pocper/SoC-GPS-Hybrid-Acquisition/firmware/hps_core/DE10_serial_parallel/INC/ARMCA9.h

/**************************************************************************//**
 * @file     ARMCA9.h
 * @brief    CMSIS-Core(A) Device Header File for Device ARMCA9
 *
 * @version  V1.1.0
 * @date     18. July 2023
 ******************************************************************************/
/*
 * Copyright (c) 2009-2023 Arm Limited. All rights reserved.
 *
 * SPDX-License-Identifier: Apache-2.0
 *
 * Licensed under the Apache License, Version 2.0 (the License); you may
 * not use this file except in compliance with the License.
 * You may obtain a copy of the License at
 *
 * www.apache.org/licenses/LICENSE-2.0
 *
 * Unless required by applicable law or agreed to in writing, software
 * distributed under the License is distributed on an AS IS BASIS, WITHOUT
 * WARRANTIES OR CONDITIONS OF ANY KIND, either express or implied.
 * See the License for the specific language governing permissions and
 * limitations under the License.
 */

#ifndef ARMCA9_H
#define ARMCA9_H

#ifdef __cplusplus
extern "C" {
#endif


/* ------------------  Interrupt Number Definition  ------------------------ */

typedef enum IRQn
{
/* ------------------  SGI Interrupts Numbers  ----------------------------- */
  SGI0_IRQn            =  0,        /* Software Generated Interrupt 0 */
  SGI1_IRQn            =  1,        /* Software Generated Interrupt 1 */
  SGI2_IRQn            =  2,        /* Software Generated Interrupt 2 */
  SGI3_IRQn            =  3,        /* Software Generated Interrupt 3 */
  SGI4_IRQn            =  4,        /* Software Generated Interrupt 4 */
  SGI5_IRQn            =  5,        /* Software Generated Interrupt 5 */
  SGI6_IRQn            =  6,        /* Software Generated Interrupt 6 */
  SGI7_IRQn            =  7,        /* Software Generated Interrupt 7 */
  SGI8_IRQn            =  8,        /* Software Generated Interrupt 8 */
  SGI9_IRQn            =  9,        /* Software Generated Interrupt 9 */
  SGI10_IRQn           = 10,        /* Software Generated Interrupt 10 */
  SGI11_IRQn           = 11,        /* Software Generated Interrupt 11 */
  SGI12_IRQn           = 12,        /* Software Generated Interrupt 12 */
  SGI13_IRQn           = 13,        /* Software Generated Interrupt 13 */
  SGI14_IRQn           = 14,        /* Software Generated Interrupt 14 */
  SGI15_IRQn           = 15,        /* Software Generated Interrupt 15 */

/* ------------------  Cortex-A9 Processor Exceptions Numbers  ------------- */
  GlobalTimer_IRQn     = 27,        /* Global Timer Interrupt */
  PrivTimer_IRQn       = 29,        /* Private Timer Interrupt */
  PrivWatchdog_IRQn    = 30,        /* Private Watchdog Interrupt */

/* ------------------  Platform Interrupt Numbers  ------------------------- */
  FPGA_IRQ0            = 72,        /* Parallel Search Interrupt */
  FPGA_IRQ1            = 73,
  FPGA_IRQ2            = 74,
  FPGA_IRQ3            = 75,
  UART0_IRQ            = 194,
  UART1_IRQ            = 195
} IRQn_Type;

/*****************************************************************************/
/*                         Peripheral memory map                             */
/*****************************************************************************/

/* Peripheral and RAM base address */
#define VE_A9_MP_FLASH_BASE0                  (0x00000000UL)                                /* (FLASH0     ) Base Address */
#define VE_A9_MP_FLASH_BASE1                  (0x0C000000UL)                                /* (FLASH1     ) Base Address */
#define VE_A9_MP_SRAM_BASE                    (0x14000000UL)                                /* (SRAM       ) Base Address */
#define VE_A9_MP_PERIPH_BASE_CS2              (0x18000000UL)                                /* (Peripheral ) Base Address */
#define VE_A9_MP_VRAM_BASE                    (0x00000000UL + VE_A9_MP_PERIPH_BASE_CS2)     /* (VRAM       ) Base Address */
#define VE_A9_MP_ETHERNET_BASE                (0x02000000UL + VE_A9_MP_PERIPH_BASE_CS2)     /* (ETHERNET   ) Base Address */
#define VE_A9_MP_USB_BASE                     (0x03000000UL + VE_A9_MP_PERIPH_BASE_CS2)     /* (USB        ) Base Address */
#define VE_A9_MP_PERIPH_BASE_CS3              (0x1C000000UL)                                /* (Peripheral ) Base Address */
#define VE_A9_MP_DAP_BASE                     (0x00000000UL + VE_A9_MP_PERIPH_BASE_CS3)     /* (LOCAL DAP  ) Base Address */
#define VE_A9_MP_SYSTEM_REG_BASE              (0x00010000UL + VE_A9_MP_PERIPH_BASE_CS3)     /* (SYSTEM REG ) Base Address */
#define VE_A9_MP_SERIAL_BASE                  (0x00030000UL + VE_A9_MP_PERIPH_BASE_CS3)     /* (SERIAL     ) Base Address */
#define VE_A9_MP_AACI_BASE                    (0x00040000UL + VE_A9_MP_PERIPH_BASE_CS3)     /* (AACI       ) Base Address */
#define VE_A9_MP_MMCI_BASE                    (0x00050000UL + VE_A9_MP_PERIPH_BASE_CS3)     /* (MMCI       ) Base Address */
#define VE_A9_MP_KMI0_BASE                    (0x00060000UL + VE_A9_MP_PERIPH_BASE_CS3)     /* (KMI0       ) Base Address */
#define VE_A9_MP_UART_BASE                    (0x00090000UL + VE_A9_MP_PERIPH_BASE_CS3)     /* (UART       ) Base Address */
#define VE_A9_MP_WDT_BASE                     (0x000F0000UL + VE_A9_MP_PERIPH_BASE_CS3)     /* (WDT        ) Base Address */
#define VE_A9_MP_TIMER_BASE                   (0x00110000UL + VE_A9_MP_PERIPH_BASE_CS3)     /* (TIMER      ) Base Address */
#define VE_A9_MP_DVI_BASE                     (0x00160000UL + VE_A9_MP_PERIPH_BASE_CS3)     /* (DVI        ) Base Address */
#define VE_A9_MP_RTC_BASE                     (0x00170000UL + VE_A9_MP_PERIPH_BASE_CS3)     /* (RTC        ) Base Address */
#define VE_A9_MP_UART4_BASE                   (0x001B0000UL + VE_A9_MP_PERIPH_BASE_CS3)     /* (UART4      ) Base Address */
#define VE_A9_MP_CLCD_BASE                    (0x001F0000UL + VE_A9_MP_PERIPH_BASE_CS3)     /* (CLCD       ) Base Address */
#define VE_A9_MP_PL310_BASE                   (0x1E00A000UL)                                /* (L2C-310    ) Base Address */
#define VE_A9_MP_PRIVATE_PERIPH_BASE          (0x2C000000UL)                                /* (Peripheral ) Base Address */
#define VE_A9_MP_GIC_DISTRIBUTOR_BASE         (0x00001000UL + VE_A9_MP_PRIVATE_PERIPH_BASE) /* (GIC DIST   ) Base Address */
#define VE_A9_MP_GIC_INTERFACE_BASE           (0x00000100UL + VE_A9_MP_PRIVATE_PERIPH_BASE) /* (GIC CPU IF ) Base Address */
#define VE_A9_MP_PRIVATE_TIMER                (0x00000600UL + VE_A9_MP_PRIVATE_PERIPH_BASE) /* (PTIM       ) Base Address */
#define VE_A9_MP_SSRAM_BASE                   (0x2E000000UL)                                /* (System SRAM) Base Address */
#define VE_A9_MP_DRAM_BASE                    (0x80000000UL)                                /* (DRAM       ) Base Address */

// Cyclone V HPS Register Address Map
// https://www.intel.com/content/www/us/en/programmable/hps/cyclone-v/hps.html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
#define GIC_DISTRIBUTOR_BASE (0xFFFED000UL)
#define GIC_INTERFACE_BASE   (0xFFFEC100UL)
#define GLOBAL_TIMER_BASE    (0xFFFEC200UL)
#define TIMER_BASE   (0xFFFEC600UL)

/* The VE-A9 model implements L1 cache as architecturally defined, but does not implement L2 cache */
/* Do not enable the L2 cache if you are running RTX on a VE-A9 model as it may cause a data abort */
#define L2C_310_BASE                          VE_A9_MP_PL310_BASE


/* ----  Start of section using anonymous unions and disabling warnings  --- */
#if   defined (__CC_ARM)
  #pragma push
  #pragma anon_unions
#elif defined (__ICCARM__)
  #pragma language=extended
#elif defined(__ARMCC_VERSION) && (__ARMCC_VERSION >= 6010050)
  #pragma clang diagnostic push
  #pragma clang diagnostic ignored "-Wc11-extensions"
  #pragma clang diagnostic ignored "-Wreserved-id-macro"
#elif defined (__GNUC__)
  /* anonymous unions are enabled by default */
#elif defined (__TMS470__)
  /* anonymous unions are enabled by default */
#elif defined (__TASKING__)
  #pragma warning 586
#elif defined (__CSMC__)
  /* anonymous unions are enabled by default */
#else
  #warning Not supported compiler type
#endif


/* ----  Configuration of Core Peripherals  -------------------------------- */
#define __CA_REV                  0x0000U   /* Core revision r0p0 */
#define __CORTEX_A                9U        /* Cortex-A9 Core */
#define __FPU_PRESENT             1U        /* FPU present */
#define __GIC_PRESENT             1U        /* GIC present */
#define __TIM_PRESENT             1U        /* TIM present */
#define __L2C_PRESENT             0U        /* L2C present */

#include "core_ca.h"                        /* Processor and core peripherals */
#include <system_ARMCA9.h>                  /* System Header */


/* ----  End of section using anonymous unions and disabling warnings  ----- */
#if   defined (__CC_ARM)
  #pragma pop
#elif defined (__ICCARM__)
  /* leave anonymous unions enabled */
#elif (defined(__ARMCC_VERSION) && (__ARMCC_VERSION >= 6010050))
  #pragma clang diagnostic pop
#elif defined (__GNUC__)
  /* anonymous unions are enabled by default */
#elif defined (__TMS470__)
  /* anonymous unions are enabled by default */
#elif defined (__TASKING__)
  #pragma warning restore
#elif defined (__CSMC__)
  /* anonymous unions are enabled by default */
#else
  #warning Not supported compiler type
#endif


#ifdef __cplusplus
}
#endif

#endif  /* ARMCA9_H */
