pocper/SoC-GPS-Hybrid-Acquisition/rtl/ip/FP_accumulator/FP_accumulator/FP_accumulator_0002.vhd

-- ------------------------------------------------------------------------- 
-- High Level Design Compiler for Intel(R) FPGAs Version 25.1std (Release Build #1129)
-- Quartus Prime development tool and MATLAB/Simulink Interface
-- 
-- Legal Notice: Copyright 2025 Intel Corporation.  All rights reserved.
-- Your use of  Intel Corporation's design tools,  logic functions and other
-- software and  tools, and its AMPP partner logic functions, and any output
-- files any  of the foregoing (including  device programming  or simulation
-- files), and  any associated  documentation  or information  are expressly
-- subject  to the terms and  conditions of the  Intel FPGA Software License
-- Agreement, Intel MegaCore Function License Agreement, or other applicable
-- license agreement,  including,  without limitation,  that your use is for
-- the  sole  purpose of  programming  logic devices  manufactured by  Intel
-- and  sold by Intel  or its authorized  distributors. Please refer  to the
-- applicable agreement for further details.
-- ---------------------------------------------------------------------------

-- VHDL created from FP_accumulator_0002
-- VHDL created on Mon Feb 23 20:37:34 2026


library IEEE;
use IEEE.std_logic_1164.all;
use IEEE.NUMERIC_STD.all;
use IEEE.MATH_REAL.all;
use std.TextIO.all;
use work.dspba_library_package.all;

LIBRARY altera_mf;
USE altera_mf.altera_mf_components.all;
LIBRARY altera_lnsim;
USE altera_lnsim.altera_lnsim_components.altera_syncram;
LIBRARY lpm;
USE lpm.lpm_components.all;

entity FP_accumulator_0002 is
    port (
        x : in std_logic_vector(31 downto 0);  -- float32_m23
        n : in std_logic_vector(0 downto 0);  -- ufix1
        r : out std_logic_vector(31 downto 0);  -- float32_m23
        xo : out std_logic_vector(0 downto 0);  -- ufix1
        xu : out std_logic_vector(0 downto 0);  -- ufix1
        ao : out std_logic_vector(0 downto 0);  -- ufix1
        clk : in std_logic;
        areset : in std_logic
    );
end FP_accumulator_0002;

architecture normal of FP_accumulator_0002 is

    attribute altera_attribute : string;
    attribute altera_attribute of normal : architecture is "-name AUTO_SHIFT_REGISTER_RECOGNITION OFF; -name PHYSICAL_SYNTHESIS_REGISTER_DUPLICATION ON; -name MESSAGE_DISABLE 10036; -name MESSAGE_DISABLE 10037; -name MESSAGE_DISABLE 14130; -name MESSAGE_DISABLE 14320; -name MESSAGE_DISABLE 15400; -name MESSAGE_DISABLE 14130; -name MESSAGE_DISABLE 10036; -name MESSAGE_DISABLE 12020; -name MESSAGE_DISABLE 12030; -name MESSAGE_DISABLE 12010; -name MESSAGE_DISABLE 12110; -name MESSAGE_DISABLE 14320; -name MESSAGE_DISABLE 13410; -name MESSAGE_DISABLE 113007";
    
    signal GND_q : STD_LOGIC_VECTOR (0 downto 0);
    signal VCC_q : STD_LOGIC_VECTOR (0 downto 0);
    signal expX_uid6_fpAccTest_b : STD_LOGIC_VECTOR (7 downto 0);
    signal fracX_uid7_fpAccTest_b : STD_LOGIC_VECTOR (22 downto 0);
    signal signX_uid8_fpAccTest_b : STD_LOGIC_VECTOR (0 downto 0);
    signal oFracX_uid10_fpAccTest_q : STD_LOGIC_VECTOR (23 downto 0);
    signal expLTLSBA_uid11_fpAccTest_q : STD_LOGIC_VECTOR (7 downto 0);
    signal cmpLT_expX_expLTLSBA_uid12_fpAccTest_a : STD_LOGIC_VECTOR (9 downto 0);
    signal cmpLT_expX_expLTLSBA_uid12_fpAccTest_b : STD_LOGIC_VECTOR (9 downto 0);
    signal cmpLT_expX_expLTLSBA_uid12_fpAccTest_o : STD_LOGIC_VECTOR (9 downto 0);
    signal cmpLT_expX_expLTLSBA_uid12_fpAccTest_c : STD_LOGIC_VECTOR (0 downto 0);
    signal expGTMaxMSBX_uid13_fpAccTest_q : STD_LOGIC_VECTOR (7 downto 0);
    signal cmpGT_expX_expGTMaxMSBX_uid14_fpAccTest_a : STD_LOGIC_VECTOR (9 downto 0);
    signal cmpGT_expX_expGTMaxMSBX_uid14_fpAccTest_b : STD_LOGIC_VECTOR (9 downto 0);
    signal cmpGT_expX_expGTMaxMSBX_uid14_fpAccTest_o : STD_LOGIC_VECTOR (9 downto 0);
    signal cmpGT_expX_expGTMaxMSBX_uid14_fpAccTest_c : STD_LOGIC_VECTOR (0 downto 0);
    signal rShiftConstant_uid15_fpAccTest_q : STD_LOGIC_VECTOR (8 downto 0);
    signal rightShiftValue_uid16_fpAccTest_a : STD_LOGIC_VECTOR (9 downto 0);
    signal rightShiftValue_uid16_fpAccTest_b : STD_LOGIC_VECTOR (9 downto 0);
    signal rightShiftValue_uid16_fpAccTest_o : STD_LOGIC_VECTOR (9 downto 0);
    signal rightShiftValue_uid16_fpAccTest_q : STD_LOGIC_VECTOR (9 downto 0);
    signal padConst_uid17_fpAccTest_q : STD_LOGIC_VECTOR (42 downto 0);
    signal rightPaddedIn_uid18_fpAccTest_q : STD_LOGIC_VECTOR (66 downto 0);
    signal shiftedFracUpper_uid20_fpAccTest_b : STD_LOGIC_VECTOR (42 downto 0);
    signal extendedAlignedShiftedFrac_uid21_fpAccTest_q : STD_LOGIC_VECTOR (43 downto 0);
    signal onesComplementExtendedFrac_uid22_fpAccTest_b : STD_LOGIC_VECTOR (43 downto 0);
    signal onesComplementExtendedFrac_uid22_fpAccTest_q : STD_LOGIC_VECTOR (43 downto 0);
    signal accumulator_uid24_fpAccTest_a : STD_LOGIC_VECTOR (60 downto 0);
    signal accumulator_uid24_fpAccTest_b : STD_LOGIC_VECTOR (60 downto 0);
    signal accumulator_uid24_fpAccTest_i : STD_LOGIC_VECTOR (60 downto 0);
    signal accumulator_uid24_fpAccTest_o : STD_LOGIC_VECTOR (60 downto 0);
    signal accumulator_uid24_fpAccTest_cin : STD_LOGIC_VECTOR (0 downto 0);
    signal accumulator_uid24_fpAccTest_c : STD_LOGIC_VECTOR (0 downto 0);
    signal accumulator_uid24_fpAccTest_q : STD_LOGIC_VECTOR (58 downto 0);
    signal os_uid25_fpAccTest_q : STD_LOGIC_VECTOR (59 downto 0);
    signal osr_uid26_fpAccTest_in : STD_LOGIC_VECTOR (58 downto 0);
    signal osr_uid26_fpAccTest_b : STD_LOGIC_VECTOR (58 downto 0);
    signal sum_uid27_fpAccTest_in : STD_LOGIC_VECTOR (57 downto 0);
    signal sum_uid27_fpAccTest_b : STD_LOGIC_VECTOR (57 downto 0);
    signal accumulatorSign_uid29_fpAccTest_in : STD_LOGIC_VECTOR (56 downto 0);
    signal accumulatorSign_uid29_fpAccTest_b : STD_LOGIC_VECTOR (0 downto 0);
    signal accOverflowBitMSB_uid30_fpAccTest_b : STD_LOGIC_VECTOR (0 downto 0);
    signal accOverflow_uid32_fpAccTest_q : STD_LOGIC_VECTOR (0 downto 0);
    signal accValidRange_uid33_fpAccTest_in : STD_LOGIC_VECTOR (56 downto 0);
    signal accValidRange_uid33_fpAccTest_b : STD_LOGIC_VECTOR (56 downto 0);
    signal accOnesComplement_uid34_fpAccTest_b : STD_LOGIC_VECTOR (56 downto 0);
    signal accOnesComplement_uid34_fpAccTest_q : STD_LOGIC_VECTOR (56 downto 0);
    signal accValuePositive_uid35_fpAccTest_a : STD_LOGIC_VECTOR (57 downto 0);
    signal accValuePositive_uid35_fpAccTest_b : STD_LOGIC_VECTOR (57 downto 0);
    signal accValuePositive_uid35_fpAccTest_o : STD_LOGIC_VECTOR (57 downto 0);
    signal accValuePositive_uid35_fpAccTest_q : STD_LOGIC_VECTOR (57 downto 0);
    signal posAccWoLeadingZeroBit_uid36_fpAccTest_in : STD_LOGIC_VECTOR (55 downto 0);
    signal posAccWoLeadingZeroBit_uid36_fpAccTest_b : STD_LOGIC_VECTOR (55 downto 0);
    signal ShiftedOutComparator_uid38_fpAccTest_q : STD_LOGIC_VECTOR (5 downto 0);
    signal accResOutOfExpRange_uid39_fpAccTest_q : STD_LOGIC_VECTOR (0 downto 0);
    signal expRBias_uid41_fpAccTest_q : STD_LOGIC_VECTOR (8 downto 0);
    signal zeroExponent_uid42_fpAccTest_q : STD_LOGIC_VECTOR (7 downto 0);
    signal fracR_uid46_fpAccTest_in : STD_LOGIC_VECTOR (54 downto 0);
    signal fracR_uid46_fpAccTest_b : STD_LOGIC_VECTOR (22 downto 0);
    signal R_uid47_fpAccTest_q : STD_LOGIC_VECTOR (31 downto 0);
    signal delayedXOverflowFeedbackSignal_uid50_fpAccTest_q : STD_LOGIC_VECTOR (0 downto 0);
    signal muxXOverflowFeedbackSignal_uid51_fpAccTest_s : STD_LOGIC_VECTOR (0 downto 0);
    signal muxXOverflowFeedbackSignal_uid51_fpAccTest_q : STD_LOGIC_VECTOR (0 downto 0);
    signal oRXOverflowFlagFeedback_uid52_fpAccTest_qi : STD_LOGIC_VECTOR (0 downto 0);
    signal oRXOverflowFlagFeedback_uid52_fpAccTest_q : STD_LOGIC_VECTOR (0 downto 0);
    signal muxXUnderflowFeedbackSignal_uid55_fpAccTest_s : STD_LOGIC_VECTOR (0 downto 0);
    signal muxXUnderflowFeedbackSignal_uid55_fpAccTest_q : STD_LOGIC_VECTOR (0 downto 0);
    signal expNotZero_uid56_fpAccTest_q : STD_LOGIC_VECTOR (0 downto 0);
    signal underflowCond_uid57_fpAccTest_q : STD_LOGIC_VECTOR (0 downto 0);
    signal oRXUnderflowFlagFeedback_uid58_fpAccTest_qi : STD_LOGIC_VECTOR (0 downto 0);
    signal oRXUnderflowFlagFeedback_uid58_fpAccTest_q : STD_LOGIC_VECTOR (0 downto 0);
    signal delayedAccOverflowFeedbackSignal_uid60_fpAccTest_q : STD_LOGIC_VECTOR (0 downto 0);
    signal muxAccOverflowFeedbackSignal_uid61_fpAccTest_s : STD_LOGIC_VECTOR (0 downto 0);
    signal muxAccOverflowFeedbackSignal_uid61_fpAccTest_q : STD_LOGIC_VECTOR (0 downto 0);
    signal oRAccOverflowFlagFeedback_uid62_fpAccTest_qi : STD_LOGIC_VECTOR (0 downto 0);
    signal oRAccOverflowFlagFeedback_uid62_fpAccTest_q : STD_LOGIC_VECTOR (0 downto 0);
    signal zs_uid66_zeroCounter_uid37_fpAccTest_q : STD_LOGIC_VECTOR (31 downto 0);
    signal vCount_uid68_zeroCounter_uid37_fpAccTest_q : STD_LOGIC_VECTOR (0 downto 0);
    signal mO_uid69_zeroCounter_uid37_fpAccTest_q : STD_LOGIC_VECTOR (7 downto 0);
    signal cStage_uid71_zeroCounter_uid37_fpAccTest_q : STD_LOGIC_VECTOR (31 downto 0);
    signal vStagei_uid73_zeroCounter_uid37_fpAccTest_s : STD_LOGIC_VECTOR (0 downto 0);
    signal vStagei_uid73_zeroCounter_uid37_fpAccTest_q : STD_LOGIC_VECTOR (31 downto 0);
    signal zs_uid74_zeroCounter_uid37_fpAccTest_q : STD_LOGIC_VECTOR (15 downto 0);
    signal vCount_uid76_zeroCounter_uid37_fpAccTest_q : STD_LOGIC_VECTOR (0 downto 0);
    signal vStagei_uid79_zeroCounter_uid37_fpAccTest_s : STD_LOGIC_VECTOR (0 downto 0);
    signal vStagei_uid79_zeroCounter_uid37_fpAccTest_q : STD_LOGIC_VECTOR (15 downto 0);
    signal vCount_uid82_zeroCounter_uid37_fpAccTest_q : STD_LOGIC_VECTOR (0 downto 0);
    signal vStagei_uid85_zeroCounter_uid37_fpAccTest_s : STD_LOGIC_VECTOR (0 downto 0);
    signal vStagei_uid85_zeroCounter_uid37_fpAccTest_q : STD_LOGIC_VECTOR (7 downto 0);
    signal zs_uid86_zeroCounter_uid37_fpAccTest_q : STD_LOGIC_VECTOR (3 downto 0);
    signal vCount_uid88_zeroCounter_uid37_fpAccTest_q : STD_LOGIC_VECTOR (0 downto 0);
    signal vStagei_uid91_zeroCounter_uid37_fpAccTest_s : STD_LOGIC_VECTOR (0 downto 0);
    signal vStagei_uid91_zeroCounter_uid37_fpAccTest_q : STD_LOGIC_VECTOR (3 downto 0);
    signal zs_uid92_zeroCounter_uid37_fpAccTest_q : STD_LOGIC_VECTOR (1 downto 0);
    signal vCount_uid94_zeroCounter_uid37_fpAccTest_q : STD_LOGIC_VECTOR (0 downto 0);
    signal vStagei_uid97_zeroCounter_uid37_fpAccTest_s : STD_LOGIC_VECTOR (0 downto 0);
    signal vStagei_uid97_zeroCounter_uid37_fpAccTest_q : STD_LOGIC_VECTOR (1 downto 0);
    signal rVStage_uid99_zeroCounter_uid37_fpAccTest_b : STD_LOGIC_VECTOR (0 downto 0);
    signal vCount_uid100_zeroCounter_uid37_fpAccTest_q : STD_LOGIC_VECTOR (0 downto 0);
    signal r_uid101_zeroCounter_uid37_fpAccTest_q : STD_LOGIC_VECTOR (5 downto 0);
    signal wIntCst_uid105_alignmentShifter_uid17_fpAccTest_q : STD_LOGIC_VECTOR (6 downto 0);
    signal shiftedOut_uid106_alignmentShifter_uid17_fpAccTest_a : STD_LOGIC_VECTOR (11 downto 0);
    signal shiftedOut_uid106_alignmentShifter_uid17_fpAccTest_b : STD_LOGIC_VECTOR (11 downto 0);
    signal shiftedOut_uid106_alignmentShifter_uid17_fpAccTest_o : STD_LOGIC_VECTOR (11 downto 0);
    signal shiftedOut_uid106_alignmentShifter_uid17_fpAccTest_n : STD_LOGIC_VECTOR (0 downto 0);
    signal rightShiftStage0Idx1Rng32_uid107_alignmentShifter_uid17_fpAccTest_b : STD_LOGIC_VECTOR (34 downto 0);
    signal rightShiftStage0Idx1_uid109_alignmentShifter_uid17_fpAccTest_q : STD_LOGIC_VECTOR (66 downto 0);
    signal rightShiftStage0Idx2Rng64_uid110_alignmentShifter_uid17_fpAccTest_b : STD_LOGIC_VECTOR (2 downto 0);
    signal rightShiftStage0Idx2Pad64_uid111_alignmentShifter_uid17_fpAccTest_q : STD_LOGIC_VECTOR (63 downto 0);
    signal rightShiftStage0Idx2_uid112_alignmentShifter_uid17_fpAccTest_q : STD_LOGIC_VECTOR (66 downto 0);
    signal rightShiftStage0Idx3_uid113_alignmentShifter_uid17_fpAccTest_q : STD_LOGIC_VECTOR (66 downto 0);
    signal rightShiftStage0_uid115_alignmentShifter_uid17_fpAccTest_s : STD_LOGIC_VECTOR (1 downto 0);
    signal rightShiftStage0_uid115_alignmentShifter_uid17_fpAccTest_q : STD_LOGIC_VECTOR (66 downto 0);
    signal rightShiftStage1Idx1Rng8_uid116_alignmentShifter_uid17_fpAccTest_b : STD_LOGIC_VECTOR (58 downto 0);
    signal rightShiftStage1Idx1_uid118_alignmentShifter_uid17_fpAccTest_q : STD_LOGIC_VECTOR (66 downto 0);
    signal rightShiftStage1Idx2Rng16_uid119_alignmentShifter_uid17_fpAccTest_b : STD_LOGIC_VECTOR (50 downto 0);
    signal rightShiftStage1Idx2_uid121_alignmentShifter_uid17_fpAccTest_q : STD_LOGIC_VECTOR (66 downto 0);
    signal rightShiftStage1Idx3Rng24_uid122_alignmentShifter_uid17_fpAccTest_b : STD_LOGIC_VECTOR (42 downto 0);
    signal rightShiftStage1Idx3Pad24_uid123_alignmentShifter_uid17_fpAccTest_q : STD_LOGIC_VECTOR (23 downto 0);
    signal rightShiftStage1Idx3_uid124_alignmentShifter_uid17_fpAccTest_q : STD_LOGIC_VECTOR (66 downto 0);
    signal rightShiftStage1_uid126_alignmentShifter_uid17_fpAccTest_s : STD_LOGIC_VECTOR (1 downto 0);
    signal rightShiftStage1_uid126_alignmentShifter_uid17_fpAccTest_q : STD_LOGIC_VECTOR (66 downto 0);
    signal rightShiftStage2Idx1Rng2_uid127_alignmentShifter_uid17_fpAccTest_b : STD_LOGIC_VECTOR (64 downto 0);
    signal rightShiftStage2Idx1_uid129_alignmentShifter_uid17_fpAccTest_q : STD_LOGIC_VECTOR (66 downto 0);
    signal rightShiftStage2Idx2Rng4_uid130_alignmentShifter_uid17_fpAccTest_b : STD_LOGIC_VECTOR (62 downto 0);
    signal rightShiftStage2Idx2_uid132_alignmentShifter_uid17_fpAccTest_q : STD_LOGIC_VECTOR (66 downto 0);
    signal rightShiftStage2Idx3Rng6_uid133_alignmentShifter_uid17_fpAccTest_b : STD_LOGIC_VECTOR (60 downto 0);
    signal rightShiftStage2Idx3Pad6_uid134_alignmentShifter_uid17_fpAccTest_q : STD_LOGIC_VECTOR (5 downto 0);
    signal rightShiftStage2Idx3_uid135_alignmentShifter_uid17_fpAccTest_q : STD_LOGIC_VECTOR (66 downto 0);
    signal rightShiftStage2_uid137_alignmentShifter_uid17_fpAccTest_s : STD_LOGIC_VECTOR (1 downto 0);
    signal rightShiftStage2_uid137_alignmentShifter_uid17_fpAccTest_q : STD_LOGIC_VECTOR (66 downto 0);
    signal rightShiftStage3Idx1Rng1_uid138_alignmentShifter_uid17_fpAccTest_b : STD_LOGIC_VECTOR (65 downto 0);
    signal rightShiftStage3Idx1_uid140_alignmentShifter_uid17_fpAccTest_q : STD_LOGIC_VECTOR (66 downto 0);
    signal rightShiftStage3_uid142_alignmentShifter_uid17_fpAccTest_s : STD_LOGIC_VECTOR (0 downto 0);
    signal rightShiftStage3_uid142_alignmentShifter_uid17_fpAccTest_q : STD_LOGIC_VECTOR (66 downto 0);
    signal r_uid144_alignmentShifter_uid17_fpAccTest_s : STD_LOGIC_VECTOR (0 downto 0);
    signal r_uid144_alignmentShifter_uid17_fpAccTest_q : STD_LOGIC_VECTOR (66 downto 0);
    signal leftShiftStage0Idx1Rng16_uid149_normalizationShifter_uid40_fpAccTest_in : STD_LOGIC_VECTOR (41 downto 0);
    signal leftShiftStage0Idx1Rng16_uid149_normalizationShifter_uid40_fpAccTest_b : STD_LOGIC_VECTOR (41 downto 0);
    signal leftShiftStage0Idx1_uid150_normalizationShifter_uid40_fpAccTest_q : STD_LOGIC_VECTOR (57 downto 0);
    signal leftShiftStage0Idx2Rng32_uid152_normalizationShifter_uid40_fpAccTest_in : STD_LOGIC_VECTOR (25 downto 0);
    signal leftShiftStage0Idx2Rng32_uid152_normalizationShifter_uid40_fpAccTest_b : STD_LOGIC_VECTOR (25 downto 0);
    signal leftShiftStage0Idx2_uid153_normalizationShifter_uid40_fpAccTest_q : STD_LOGIC_VECTOR (57 downto 0);
    signal leftShiftStage0Idx3Pad48_uid154_normalizationShifter_uid40_fpAccTest_q : STD_LOGIC_VECTOR (47 downto 0);
    signal leftShiftStage0Idx3Rng48_uid155_normalizationShifter_uid40_fpAccTest_in : STD_LOGIC_VECTOR (9 downto 0);
    signal leftShiftStage0Idx3Rng48_uid155_normalizationShifter_uid40_fpAccTest_b : STD_LOGIC_VECTOR (9 downto 0);
    signal leftShiftStage0Idx3_uid156_normalizationShifter_uid40_fpAccTest_q : STD_LOGIC_VECTOR (57 downto 0);
    signal leftShiftStage0_uid158_normalizationShifter_uid40_fpAccTest_s : STD_LOGIC_VECTOR (1 downto 0);
    signal leftShiftStage0_uid158_normalizationShifter_uid40_fpAccTest_q : STD_LOGIC_VECTOR (57 downto 0);
    signal leftShiftStage1Idx1Rng4_uid160_normalizationShifter_uid40_fpAccTest_in : STD_LOGIC_VECTOR (53 downto 0);
    signal leftShiftStage1Idx1Rng4_uid160_normalizationShifter_uid40_fpAccTest_b : STD_LOGIC_VECTOR (53 downto 0);
    signal leftShiftStage1Idx1_uid161_normalizationShifter_uid40_fpAccTest_q : STD_LOGIC_VECTOR (57 downto 0);
    signal leftShiftStage1Idx2Rng8_uid163_normalizationShifter_uid40_fpAccTest_in : STD_LOGIC_VECTOR (49 downto 0);
    signal leftShiftStage1Idx2Rng8_uid163_normalizationShifter_uid40_fpAccTest_b : STD_LOGIC_VECTOR (49 downto 0);
    signal leftShiftStage1Idx2_uid164_normalizationShifter_uid40_fpAccTest_q : STD_LOGIC_VECTOR (57 downto 0);
    signal leftShiftStage1Idx3Pad12_uid165_normalizationShifter_uid40_fpAccTest_q : STD_LOGIC_VECTOR (11 downto 0);
    signal leftShiftStage1Idx3Rng12_uid166_normalizationShifter_uid40_fpAccTest_in : STD_LOGIC_VECTOR (45 downto 0);
    signal leftShiftStage1Idx3Rng12_uid166_normalizationShifter_uid40_fpAccTest_b : STD_LOGIC_VECTOR (45 downto 0);
    signal leftShiftStage1Idx3_uid167_normalizationShifter_uid40_fpAccTest_q : STD_LOGIC_VECTOR (57 downto 0);
    signal leftShiftStage1_uid169_normalizationShifter_uid40_fpAccTest_s : STD_LOGIC_VECTOR (1 downto 0);
    signal leftShiftStage1_uid169_normalizationShifter_uid40_fpAccTest_q : STD_LOGIC_VECTOR (57 downto 0);
    signal leftShiftStage2Idx1Rng1_uid171_normalizationShifter_uid40_fpAccTest_in : STD_LOGIC_VECTOR (56 downto 0);
    signal leftShiftStage2Idx1Rng1_uid171_normalizationShifter_uid40_fpAccTest_b : STD_LOGIC_VECTOR (56 downto 0);
    signal leftShiftStage2Idx1_uid172_normalizationShifter_uid40_fpAccTest_q : STD_LOGIC_VECTOR (57 downto 0);
    signal leftShiftStage2Idx2Rng2_uid174_normalizationShifter_uid40_fpAccTest_in : STD_LOGIC_VECTOR (55 downto 0);
    signal leftShiftStage2Idx2Rng2_uid174_normalizationShifter_uid40_fpAccTest_b : STD_LOGIC_VECTOR (55 downto 0);
    signal leftShiftStage2Idx2_uid175_normalizationShifter_uid40_fpAccTest_q : STD_LOGIC_VECTOR (57 downto 0);
    signal leftShiftStage2Idx3Pad3_uid176_normalizationShifter_uid40_fpAccTest_q : STD_LOGIC_VECTOR (2 downto 0);
    signal leftShiftStage2Idx3Rng3_uid177_normalizationShifter_uid40_fpAccTest_in : STD_LOGIC_VECTOR (54 downto 0);
    signal leftShiftStage2Idx3Rng3_uid177_normalizationShifter_uid40_fpAccTest_b : STD_LOGIC_VECTOR (54 downto 0);
    signal leftShiftStage2Idx3_uid178_normalizationShifter_uid40_fpAccTest_q : STD_LOGIC_VECTOR (57 downto 0);
    signal leftShiftStage2_uid180_normalizationShifter_uid40_fpAccTest_s : STD_LOGIC_VECTOR (1 downto 0);
    signal leftShiftStage2_uid180_normalizationShifter_uid40_fpAccTest_q : STD_LOGIC_VECTOR (57 downto 0);
    signal resExpSub_uid43_fpAccTest_finalExpUpdated_uid45_fpAccTest_merged_a : STD_LOGIC_VECTOR (8 downto 0);
    signal resExpSub_uid43_fpAccTest_finalExpUpdated_uid45_fpAccTest_merged_b : STD_LOGIC_VECTOR (8 downto 0);
    signal resExpSub_uid43_fpAccTest_finalExpUpdated_uid45_fpAccTest_merged_i : STD_LOGIC_VECTOR (8 downto 0);
    signal resExpSub_uid43_fpAccTest_finalExpUpdated_uid45_fpAccTest_merged_o : STD_LOGIC_VECTOR (8 downto 0);
    signal resExpSub_uid43_fpAccTest_finalExpUpdated_uid45_fpAccTest_merged_q : STD_LOGIC_VECTOR (7 downto 0);
    signal rightShiftStageSel6Dto5_uid114_alignmentShifter_uid17_fpAccTest_merged_bit_select_in : STD_LOGIC_VECTOR (6 downto 0);
    signal rightShiftStageSel6Dto5_uid114_alignmentShifter_uid17_fpAccTest_merged_bit_select_b : STD_LOGIC_VECTOR (1 downto 0);
    signal rightShiftStageSel6Dto5_uid114_alignmentShifter_uid17_fpAccTest_merged_bit_select_c : STD_LOGIC_VECTOR (1 downto 0);
    signal rightShiftStageSel6Dto5_uid114_alignmentShifter_uid17_fpAccTest_merged_bit_select_d : STD_LOGIC_VECTOR (1 downto 0);
    signal rightShiftStageSel6Dto5_uid114_alignmentShifter_uid17_fpAccTest_merged_bit_select_e : STD_LOGIC_VECTOR (0 downto 0);
    signal rVStage_uid67_zeroCounter_uid37_fpAccTest_merged_bit_select_b : STD_LOGIC_VECTOR (31 downto 0);
    signal rVStage_uid67_zeroCounter_uid37_fpAccTest_merged_bit_select_c : STD_LOGIC_VECTOR (23 downto 0);
    signal rVStage_uid75_zeroCounter_uid37_fpAccTest_merged_bit_select_b : STD_LOGIC_VECTOR (15 downto 0);
    signal rVStage_uid75_zeroCounter_uid37_fpAccTest_merged_bit_select_c : STD_LOGIC_VECTOR (15 downto 0);
    signal rVStage_uid81_zeroCounter_uid37_fpAccTest_merged_bit_select_b : STD_LOGIC_VECTOR (7 downto 0);
    signal rVStage_uid81_zeroCounter_uid37_fpAccTest_merged_bit_select_c : STD_LOGIC_VECTOR (7 downto 0);
    signal rVStage_uid87_zeroCounter_uid37_fpAccTest_merged_bit_select_b : STD_LOGIC_VECTOR (3 downto 0);
    signal rVStage_uid87_zeroCounter_uid37_fpAccTest_merged_bit_select_c : STD_LOGIC_VECTOR (3 downto 0);
    signal rVStage_uid93_zeroCounter_uid37_fpAccTest_merged_bit_select_b : STD_LOGIC_VECTOR (1 downto 0);
    signal rVStage_uid93_zeroCounter_uid37_fpAccTest_merged_bit_select_c : STD_LOGIC_VECTOR (1 downto 0);
    signal leftShiftStageSel5Dto4_uid157_normalizationShifter_uid40_fpAccTest_merged_bit_select_b : STD_LOGIC_VECTOR (1 downto 0);
    signal leftShiftStageSel5Dto4_uid157_normalizationShifter_uid40_fpAccTest_merged_bit_select_c : STD_LOGIC_VECTOR (1 downto 0);
    signal leftShiftStageSel5Dto4_uid157_normalizationShifter_uid40_fpAccTest_merged_bit_select_d : STD_LOGIC_VECTOR (1 downto 0);
    signal redist1_oRXUnderflowFlagFeedback_uid58_fpAccTest_q_3_q : STD_LOGIC_VECTOR (0 downto 0);
    signal redist3_fracR_uid46_fpAccTest_b_1_q : STD_LOGIC_VECTOR (22 downto 0);
    signal redist4_accumulatorSign_uid29_fpAccTest_b_2_q : STD_LOGIC_VECTOR (0 downto 0);
    signal redist5_xIn_n_1_q : STD_LOGIC_VECTOR (0 downto 0);

begin


    -- VCC(CONSTANT,1)
    VCC_q <= "1";

    -- signX_uid8_fpAccTest(BITSELECT,7)@0
    signX_uid8_fpAccTest_b <= STD_LOGIC_VECTOR(x(31 downto 31));

    -- GND(CONSTANT,0)
    GND_q <= "0";

    -- rightShiftStage0Idx3_uid113_alignmentShifter_uid17_fpAccTest(CONSTANT,112)
    rightShiftStage0Idx3_uid113_alignmentShifter_uid17_fpAccTest_q <= "0000000000000000000000000000000000000000000000000000000000000000000";

    -- rightShiftStage3Idx1Rng1_uid138_alignmentShifter_uid17_fpAccTest(BITSELECT,137)@0
    rightShiftStage3Idx1Rng1_uid138_alignmentShifter_uid17_fpAccTest_b <= rightShiftStage2_uid137_alignmentShifter_uid17_fpAccTest_q(66 downto 1);

    -- rightShiftStage3Idx1_uid140_alignmentShifter_uid17_fpAccTest(BITJOIN,139)@0
    rightShiftStage3Idx1_uid140_alignmentShifter_uid17_fpAccTest_q <= GND_q & rightShiftStage3Idx1Rng1_uid138_alignmentShifter_uid17_fpAccTest_b;

    -- rightShiftStage2Idx3Pad6_uid134_alignmentShifter_uid17_fpAccTest(CONSTANT,133)
    rightShiftStage2Idx3Pad6_uid134_alignmentShifter_uid17_fpAccTest_q <= "000000";

    -- rightShiftStage2Idx3Rng6_uid133_alignmentShifter_uid17_fpAccTest(BITSELECT,132)@0
    rightShiftStage2Idx3Rng6_uid133_alignmentShifter_uid17_fpAccTest_b <= rightShiftStage1_uid126_alignmentShifter_uid17_fpAccTest_q(66 downto 6);

    -- rightShiftStage2Idx3_uid135_alignmentShifter_uid17_fpAccTest(BITJOIN,134)@0
    rightShiftStage2Idx3_uid135_alignmentShifter_uid17_fpAccTest_q <= rightShiftStage2Idx3Pad6_uid134_alignmentShifter_uid17_fpAccTest_q & rightShiftStage2Idx3Rng6_uid133_alignmentShifter_uid17_fpAccTest_b;

    -- zs_uid86_zeroCounter_uid37_fpAccTest(CONSTANT,85)
    zs_uid86_zeroCounter_uid37_fpAccTest_q <= "0000";

    -- rightShiftStage2Idx2Rng4_uid130_alignmentShifter_uid17_fpAccTest(BITSELECT,129)@0
    rightShiftStage2Idx2Rng4_uid130_alignmentShifter_uid17_fpAccTest_b <= rightShiftStage1_uid126_alignmentShifter_uid17_fpAccTest_q(66 downto 4);

    -- rightShiftStage2Idx2_uid132_alignmentShifter_uid17_fpAccTest(BITJOIN,131)@0
    rightShiftStage2Idx2_uid132_alignmentShifter_uid17_fpAccTest_q <= zs_uid86_zeroCounter_uid37_fpAccTest_q & rightShiftStage2Idx2Rng4_uid130_alignmentShifter_uid17_fpAccTest_b;

    -- zs_uid92_zeroCounter_uid37_fpAccTest(CONSTANT,91)
    zs_uid92_zeroCounter_uid37_fpAccTest_q <= "00";

    -- rightShiftStage2Idx1Rng2_uid127_alignmentShifter_uid17_fpAccTest(BITSELECT,126)@0
    rightShiftStage2Idx1Rng2_uid127_alignmentShifter_uid17_fpAccTest_b <= rightShiftStage1_uid126_alignmentShifter_uid17_fpAccTest_q(66 downto 2);

    -- rightShiftStage2Idx1_uid129_alignmentShifter_uid17_fpAccTest(BITJOIN,128)@0
    rightShiftStage2Idx1_uid129_alignmentShifter_uid17_fpAccTest_q <= zs_uid92_zeroCounter_uid37_fpAccTest_q & rightShiftStage2Idx1Rng2_uid127_alignmentShifter_uid17_fpAccTest_b;

    -- rightShiftStage1Idx3Pad24_uid123_alignmentShifter_uid17_fpAccTest(CONSTANT,122)
    rightShiftStage1Idx3Pad24_uid123_alignmentShifter_uid17_fpAccTest_q <= "000000000000000000000000";

    -- rightShiftStage1Idx3Rng24_uid122_alignmentShifter_uid17_fpAccTest(BITSELECT,121)@0
    rightShiftStage1Idx3Rng24_uid122_alignmentShifter_uid17_fpAccTest_b <= rightShiftStage0_uid115_alignmentShifter_uid17_fpAccTest_q(66 downto 24);

    -- rightShiftStage1Idx3_uid124_alignmentShifter_uid17_fpAccTest(BITJOIN,123)@0
    rightShiftStage1Idx3_uid124_alignmentShifter_uid17_fpAccTest_q <= rightShiftStage1Idx3Pad24_uid123_alignmentShifter_uid17_fpAccTest_q & rightShiftStage1Idx3Rng24_uid122_alignmentShifter_uid17_fpAccTest_b;

    -- zs_uid74_zeroCounter_uid37_fpAccTest(CONSTANT,73)
    zs_uid74_zeroCounter_uid37_fpAccTest_q <= "0000000000000000";

    -- rightShiftStage1Idx2Rng16_uid119_alignmentShifter_uid17_fpAccTest(BITSELECT,118)@0
    rightShiftStage1Idx2Rng16_uid119_alignmentShifter_uid17_fpAccTest_b <= rightShiftStage0_uid115_alignmentShifter_uid17_fpAccTest_q(66 downto 16);

    -- rightShiftStage1Idx2_uid121_alignmentShifter_uid17_fpAccTest(BITJOIN,120)@0
    rightShiftStage1Idx2_uid121_alignmentShifter_uid17_fpAccTest_q <= zs_uid74_zeroCounter_uid37_fpAccTest_q & rightShiftStage1Idx2Rng16_uid119_alignmentShifter_uid17_fpAccTest_b;

    -- zeroExponent_uid42_fpAccTest(CONSTANT,41)
    zeroExponent_uid42_fpAccTest_q <= "00000000";

    -- rightShiftStage1Idx1Rng8_uid116_alignmentShifter_uid17_fpAccTest(BITSELECT,115)@0
    rightShiftStage1Idx1Rng8_uid116_alignmentShifter_uid17_fpAccTest_b <= rightShiftStage0_uid115_alignmentShifter_uid17_fpAccTest_q(66 downto 8);

    -- rightShiftStage1Idx1_uid118_alignmentShifter_uid17_fpAccTest(BITJOIN,117)@0
    rightShiftStage1Idx1_uid118_alignmentShifter_uid17_fpAccTest_q <= zeroExponent_uid42_fpAccTest_q & rightShiftStage1Idx1Rng8_uid116_alignmentShifter_uid17_fpAccTest_b;

    -- rightShiftStage0Idx2Pad64_uid111_alignmentShifter_uid17_fpAccTest(CONSTANT,110)
    rightShiftStage0Idx2Pad64_uid111_alignmentShifter_uid17_fpAccTest_q <= "0000000000000000000000000000000000000000000000000000000000000000";

    -- rightShiftStage0Idx2Rng64_uid110_alignmentShifter_uid17_fpAccTest(BITSELECT,109)@0
    rightShiftStage0Idx2Rng64_uid110_alignmentShifter_uid17_fpAccTest_b <= rightPaddedIn_uid18_fpAccTest_q(66 downto 64);

    -- rightShiftStage0Idx2_uid112_alignmentShifter_uid17_fpAccTest(BITJOIN,111)@0
    rightShiftStage0Idx2_uid112_alignmentShifter_uid17_fpAccTest_q <= rightShiftStage0Idx2Pad64_uid111_alignmentShifter_uid17_fpAccTest_q & rightShiftStage0Idx2Rng64_uid110_alignmentShifter_uid17_fpAccTest_b;

    -- zs_uid66_zeroCounter_uid37_fpAccTest(CONSTANT,65)
    zs_uid66_zeroCounter_uid37_fpAccTest_q <= "00000000000000000000000000000000";

    -- rightShiftStage0Idx1Rng32_uid107_alignmentShifter_uid17_fpAccTest(BITSELECT,106)@0
    rightShiftStage0Idx1Rng32_uid107_alignmentShifter_uid17_fpAccTest_b <= rightPaddedIn_uid18_fpAccTest_q(66 downto 32);

    -- rightShiftStage0Idx1_uid109_alignmentShifter_uid17_fpAccTest(BITJOIN,108)@0
    rightShiftStage0Idx1_uid109_alignmentShifter_uid17_fpAccTest_q <= zs_uid66_zeroCounter_uid37_fpAccTest_q & rightShiftStage0Idx1Rng32_uid107_alignmentShifter_uid17_fpAccTest_b;

    -- fracX_uid7_fpAccTest(BITSELECT,6)@0
    fracX_uid7_fpAccTest_b <= x(22 downto 0);

    -- oFracX_uid10_fpAccTest(BITJOIN,9)@0
    oFracX_uid10_fpAccTest_q <= VCC_q & fracX_uid7_fpAccTest_b;

    -- padConst_uid17_fpAccTest(CONSTANT,16)
    padConst_uid17_fpAccTest_q <= "0000000000000000000000000000000000000000000";

    -- rightPaddedIn_uid18_fpAccTest(BITJOIN,17)@0
    rightPaddedIn_uid18_fpAccTest_q <= oFracX_uid10_fpAccTest_q & padConst_uid17_fpAccTest_q;

    -- rightShiftStage0_uid115_alignmentShifter_uid17_fpAccTest(MUX,114)@0
    rightShiftStage0_uid115_alignmentShifter_uid17_fpAccTest_s <= rightShiftStageSel6Dto5_uid114_alignmentShifter_uid17_fpAccTest_merged_bit_select_b;
    rightShiftStage0_uid115_alignmentShifter_uid17_fpAccTest_combproc: PROCESS (rightShiftStage0_uid115_alignmentShifter_uid17_fpAccTest_s, rightPaddedIn_uid18_fpAccTest_q, rightShiftStage0Idx1_uid109_alignmentShifter_uid17_fpAccTest_q, rightShiftStage0Idx2_uid112_alignmentShifter_uid17_fpAccTest_q, rightShiftStage0Idx3_uid113_alignmentShifter_uid17_fpAccTest_q)
    BEGIN
        CASE (rightShiftStage0_uid115_alignmentShifter_uid17_fpAccTest_s) IS
            WHEN "00" => rightShiftStage0_uid115_alignmentShifter_uid17_fpAccTest_q <= rightPaddedIn_uid18_fpAccTest_q;
            WHEN "01" => rightShiftStage0_uid115_alignmentShifter_uid17_fpAccTest_q <= rightShiftStage0Idx1_uid109_alignmentShifter_uid17_fpAccTest_q;
            WHEN "10" => rightShiftStage0_uid115_alignmentShifter_uid17_fpAccTest_q <= rightShiftStage0Idx2_uid112_alignmentShifter_uid17_fpAccTest_q;
            WHEN "11" => rightShiftStage0_uid115_alignmentShifter_uid17_fpAccTest_q <= rightShiftStage0Idx3_uid113_alignmentShifter_uid17_fpAccTest_q;
            WHEN OTHERS => rightShiftStage0_uid115_alignmentShifter_uid17_fpAccTest_q <= (others => '0');
        END CASE;
    END PROCESS;

    -- rightShiftStage1_uid126_alignmentShifter_uid17_fpAccTest(MUX,125)@0
    rightShiftStage1_uid126_alignmentShifter_uid17_fpAccTest_s <= rightShiftStageSel6Dto5_uid114_alignmentShifter_uid17_fpAccTest_merged_bit_select_c;
    rightShiftStage1_uid126_alignmentShifter_uid17_fpAccTest_combproc: PROCESS (rightShiftStage1_uid126_alignmentShifter_uid17_fpAccTest_s, rightShiftStage0_uid115_alignmentShifter_uid17_fpAccTest_q, rightShiftStage1Idx1_uid118_alignmentShifter_uid17_fpAccTest_q, rightShiftStage1Idx2_uid121_alignmentShifter_uid17_fpAccTest_q, rightShiftStage1Idx3_uid124_alignmentShifter_uid17_fpAccTest_q)
    BEGIN
        CASE (rightShiftStage1_uid126_alignmentShifter_uid17_fpAccTest_s) IS
            WHEN "00" => rightShiftStage1_uid126_alignmentShifter_uid17_fpAccTest_q <= rightShiftStage0_uid115_alignmentShifter_uid17_fpAccTest_q;
            WHEN "01" => rightShiftStage1_uid126_alignmentShifter_uid17_fpAccTest_q <= rightShiftStage1Idx1_uid118_alignmentShifter_uid17_fpAccTest_q;
            WHEN "10" => rightShiftStage1_uid126_alignmentShifter_uid17_fpAccTest_q <= rightShiftStage1Idx2_uid121_alignmentShifter_uid17_fpAccTest_q;
            WHEN "11" => rightShiftStage1_uid126_alignmentShifter_uid17_fpAccTest_q <= rightShiftStage1Idx3_uid124_alignmentShifter_uid17_fpAccTest_q;
            WHEN OTHERS => rightShiftStage1_uid126_alignmentShifter_uid17_fpAccTest_q <= (others => '0');
        END CASE;
    END PROCESS;

    -- rightShiftStage2_uid137_alignmentShifter_uid17_fpAccTest(MUX,136)@0
    rightShiftStage2_uid137_alignmentShifter_uid17_fpAccTest_s <= rightShiftStageSel6Dto5_uid114_alignmentShifter_uid17_fpAccTest_merged_bit_select_d;
    rightShiftStage2_uid137_alignmentShifter_uid17_fpAccTest_combproc: PROCESS (rightShiftStage2_uid137_alignmentShifter_uid17_fpAccTest_s, rightShiftStage1_uid126_alignmentShifter_uid17_fpAccTest_q, rightShiftStage2Idx1_uid129_alignmentShifter_uid17_fpAccTest_q, rightShiftStage2Idx2_uid132_alignmentShifter_uid17_fpAccTest_q, rightShiftStage2Idx3_uid135_alignmentShifter_uid17_fpAccTest_q)
    BEGIN
        CASE (rightShiftStage2_uid137_alignmentShifter_uid17_fpAccTest_s) IS
            WHEN "00" => rightShiftStage2_uid137_alignmentShifter_uid17_fpAccTest_q <= rightShiftStage1_uid126_alignmentShifter_uid17_fpAccTest_q;
            WHEN "01" => rightShiftStage2_uid137_alignmentShifter_uid17_fpAccTest_q <= rightShiftStage2Idx1_uid129_alignmentShifter_uid17_fpAccTest_q;
            WHEN "10" => rightShiftStage2_uid137_alignmentShifter_uid17_fpAccTest_q <= rightShiftStage2Idx2_uid132_alignmentShifter_uid17_fpAccTest_q;
            WHEN "11" => rightShiftStage2_uid137_alignmentShifter_uid17_fpAccTest_q <= rightShiftStage2Idx3_uid135_alignmentShifter_uid17_fpAccTest_q;
            WHEN OTHERS => rightShiftStage2_uid137_alignmentShifter_uid17_fpAccTest_q <= (others => '0');
        END CASE;
    END PROCESS;

    -- expX_uid6_fpAccTest(BITSELECT,5)@0
    expX_uid6_fpAccTest_b <= x(30 downto 23);

    -- rShiftConstant_uid15_fpAccTest(CONSTANT,14)
    rShiftConstant_uid15_fpAccTest_q <= "010010000";

    -- rightShiftValue_uid16_fpAccTest(SUB,15)@0
    rightShiftValue_uid16_fpAccTest_a <= STD_LOGIC_VECTOR("0" & rShiftConstant_uid15_fpAccTest_q);
    rightShiftValue_uid16_fpAccTest_b <= STD_LOGIC_VECTOR("00" & expX_uid6_fpAccTest_b);
    rightShiftValue_uid16_fpAccTest_o <= STD_LOGIC_VECTOR(UNSIGNED(rightShiftValue_uid16_fpAccTest_a) - UNSIGNED(rightShiftValue_uid16_fpAccTest_b));
    rightShiftValue_uid16_fpAccTest_q <= rightShiftValue_uid16_fpAccTest_o(9 downto 0);

    -- rightShiftStageSel6Dto5_uid114_alignmentShifter_uid17_fpAccTest_merged_bit_select(BITSELECT,182)@0
    rightShiftStageSel6Dto5_uid114_alignmentShifter_uid17_fpAccTest_merged_bit_select_in <= rightShiftValue_uid16_fpAccTest_q(6 downto 0);
    rightShiftStageSel6Dto5_uid114_alignmentShifter_uid17_fpAccTest_merged_bit_select_b <= rightShiftStageSel6Dto5_uid114_alignmentShifter_uid17_fpAccTest_merged_bit_select_in(6 downto 5);
    rightShiftStageSel6Dto5_uid114_alignmentShifter_uid17_fpAccTest_merged_bit_select_c <= rightShiftStageSel6Dto5_uid114_alignmentShifter_uid17_fpAccTest_merged_bit_select_in(4 downto 3);
    rightShiftStageSel6Dto5_uid114_alignmentShifter_uid17_fpAccTest_merged_bit_select_d <= rightShiftStageSel6Dto5_uid114_alignmentShifter_uid17_fpAccTest_merged_bit_select_in(2 downto 1);
    rightShiftStageSel6Dto5_uid114_alignmentShifter_uid17_fpAccTest_merged_bit_select_e <= rightShiftStageSel6Dto5_uid114_alignmentShifter_uid17_fpAccTest_merged_bit_select_in(0 downto 0);

    -- rightShiftStage3_uid142_alignmentShifter_uid17_fpAccTest(MUX,141)@0
    rightShiftStage3_uid142_alignmentShifter_uid17_fpAccTest_s <= rightShiftStageSel6Dto5_uid114_alignmentShifter_uid17_fpAccTest_merged_bit_select_e;
    rightShiftStage3_uid142_alignmentShifter_uid17_fpAccTest_combproc: PROCESS (rightShiftStage3_uid142_alignmentShifter_uid17_fpAccTest_s, rightShiftStage2_uid137_alignmentShifter_uid17_fpAccTest_q, rightShiftStage3Idx1_uid140_alignmentShifter_uid17_fpAccTest_q)
    BEGIN
        CASE (rightShiftStage3_uid142_alignmentShifter_uid17_fpAccTest_s) IS
            WHEN "0" => rightShiftStage3_uid142_alignmentShifter_uid17_fpAccTest_q <= rightShiftStage2_uid137_alignmentShifter_uid17_fpAccTest_q;
            WHEN "1" => rightShiftStage3_uid142_alignmentShifter_uid17_fpAccTest_q <= rightShiftStage3Idx1_uid140_alignmentShifter_uid17_fpAccTest_q;
            WHEN OTHERS => rightShiftStage3_uid142_alignmentShifter_uid17_fpAccTest_q <= (others => '0');
        END CASE;
    END PROCESS;

    -- wIntCst_uid105_alignmentShifter_uid17_fpAccTest(CONSTANT,104)
    wIntCst_uid105_alignmentShifter_uid17_fpAccTest_q <= "1000011";

    -- shiftedOut_uid106_alignmentShifter_uid17_fpAccTest(COMPARE,105)@0
    shiftedOut_uid106_alignmentShifter_uid17_fpAccTest_a <= STD_LOGIC_VECTOR("00" & rightShiftValue_uid16_fpAccTest_q);
    shiftedOut_uid106_alignmentShifter_uid17_fpAccTest_b <= STD_LOGIC_VECTOR("00000" & wIntCst_uid105_alignmentShifter_uid17_fpAccTest_q);
    shiftedOut_uid106_alignmentShifter_uid17_fpAccTest_o <= STD_LOGIC_VECTOR(UNSIGNED(shiftedOut_uid106_alignmentShifter_uid17_fpAccTest_a) - UNSIGNED(shiftedOut_uid106_alignmentShifter_uid17_fpAccTest_b));
    shiftedOut_uid106_alignmentShifter_uid17_fpAccTest_n(0) <= not (shiftedOut_uid106_alignmentShifter_uid17_fpAccTest_o(11));

    -- r_uid144_alignmentShifter_uid17_fpAccTest(MUX,143)@0
    r_uid144_alignmentShifter_uid17_fpAccTest_s <= shiftedOut_uid106_alignmentShifter_uid17_fpAccTest_n;
    r_uid144_alignmentShifter_uid17_fpAccTest_combproc: PROCESS (r_uid144_alignmentShifter_uid17_fpAccTest_s, rightShiftStage3_uid142_alignmentShifter_uid17_fpAccTest_q, rightShiftStage0Idx3_uid113_alignmentShifter_uid17_fpAccTest_q)
    BEGIN
        CASE (r_uid144_alignmentShifter_uid17_fpAccTest_s) IS
            WHEN "0" => r_uid144_alignmentShifter_uid17_fpAccTest_q <= rightShiftStage3_uid142_alignmentShifter_uid17_fpAccTest_q;
            WHEN "1" => r_uid144_alignmentShifter_uid17_fpAccTest_q <= rightShiftStage0Idx3_uid113_alignmentShifter_uid17_fpAccTest_q;
            WHEN OTHERS => r_uid144_alignmentShifter_uid17_fpAccTest_q <= (others => '0');
        END CASE;
    END PROCESS;

    -- shiftedFracUpper_uid20_fpAccTest(BITSELECT,19)@0
    shiftedFracUpper_uid20_fpAccTest_b <= r_uid144_alignmentShifter_uid17_fpAccTest_q(66 downto 24);

    -- extendedAlignedShiftedFrac_uid21_fpAccTest(BITJOIN,20)@0
    extendedAlignedShiftedFrac_uid21_fpAccTest_q <= GND_q & shiftedFracUpper_uid20_fpAccTest_b;

    -- onesComplementExtendedFrac_uid22_fpAccTest(LOGICAL,21)@0
    onesComplementExtendedFrac_uid22_fpAccTest_b <= STD_LOGIC_VECTOR(STD_LOGIC_VECTOR((43 downto 1 => signX_uid8_fpAccTest_b(0)) & signX_uid8_fpAccTest_b));
    onesComplementExtendedFrac_uid22_fpAccTest_q <= extendedAlignedShiftedFrac_uid21_fpAccTest_q xor onesComplementExtendedFrac_uid22_fpAccTest_b;

    -- accumulator_uid24_fpAccTest(ADD,23)@0 + 1
    accumulator_uid24_fpAccTest_cin <= signX_uid8_fpAccTest_b;
    accumulator_uid24_fpAccTest_a <= STD_LOGIC_VECTOR(STD_LOGIC_VECTOR((59 downto 58 => sum_uid27_fpAccTest_b(57)) & sum_uid27_fpAccTest_b) & '1');
    accumulator_uid24_fpAccTest_b <= STD_LOGIC_VECTOR(STD_LOGIC_VECTOR((59 downto 44 => onesComplementExtendedFrac_uid22_fpAccTest_q(43)) & onesComplementExtendedFrac_uid22_fpAccTest_q) & accumulator_uid24_fpAccTest_cin(0));
    accumulator_uid24_fpAccTest_i <= accumulator_uid24_fpAccTest_b;
    accumulator_uid24_fpAccTest_clkproc: PROCESS (clk, areset)
    BEGIN
        IF (areset = '1') THEN
            accumulator_uid24_fpAccTest_o <= (others => '0');
        ELSIF (clk'EVENT AND clk = '1') THEN
            IF (n = "1") THEN
                accumulator_uid24_fpAccTest_o <= accumulator_uid24_fpAccTest_i;
            ELSE
                accumulator_uid24_fpAccTest_o <= STD_LOGIC_VECTOR(SIGNED(accumulator_uid24_fpAccTest_a) + SIGNED(accumulator_uid24_fpAccTest_b));
            END IF;
        END IF;
    END PROCESS;
    accumulator_uid24_fpAccTest_c(0) <= accumulator_uid24_fpAccTest_o(60);
    accumulator_uid24_fpAccTest_q <= accumulator_uid24_fpAccTest_o(59 downto 1);

    -- os_uid25_fpAccTest(BITJOIN,24)@1
    os_uid25_fpAccTest_q <= accumulator_uid24_fpAccTest_c & accumulator_uid24_fpAccTest_q;

    -- osr_uid26_fpAccTest(BITSELECT,25)@1
    osr_uid26_fpAccTest_in <= STD_LOGIC_VECTOR(os_uid25_fpAccTest_q(58 downto 0));
    osr_uid26_fpAccTest_b <= STD_LOGIC_VECTOR(osr_uid26_fpAccTest_in(58 downto 0));

    -- sum_uid27_fpAccTest(BITSELECT,26)@1
    sum_uid27_fpAccTest_in <= STD_LOGIC_VECTOR(osr_uid26_fpAccTest_b(57 downto 0));
    sum_uid27_fpAccTest_b <= STD_LOGIC_VECTOR(sum_uid27_fpAccTest_in(57 downto 0));

    -- accumulatorSign_uid29_fpAccTest(BITSELECT,28)@1
    accumulatorSign_uid29_fpAccTest_in <= sum_uid27_fpAccTest_b(56 downto 0);
    accumulatorSign_uid29_fpAccTest_b <= accumulatorSign_uid29_fpAccTest_in(56 downto 56);

    -- accOverflowBitMSB_uid30_fpAccTest(BITSELECT,29)@1
    accOverflowBitMSB_uid30_fpAccTest_b <= sum_uid27_fpAccTest_b(57 downto 57);

    -- accOverflow_uid32_fpAccTest(LOGICAL,31)@1
    accOverflow_uid32_fpAccTest_q <= accOverflowBitMSB_uid30_fpAccTest_b xor accumulatorSign_uid29_fpAccTest_b;

    -- redist5_xIn_n_1(DELAY,194)
    redist5_xIn_n_1 : dspba_delay
    GENERIC MAP ( width => 1, depth => 1, reset_kind => "ASYNC" )
    PORT MAP ( xin => n, xout => redist5_xIn_n_1_q, clk => clk, aclr => areset );

    -- muxAccOverflowFeedbackSignal_uid61_fpAccTest(MUX,60)@1
    muxAccOverflowFeedbackSignal_uid61_fpAccTest_s <= redist5_xIn_n_1_q;
    muxAccOverflowFeedbackSignal_uid61_fpAccTest_combproc: PROCESS (muxAccOverflowFeedbackSignal_uid61_fpAccTest_s, oRAccOverflowFlagFeedback_uid62_fpAccTest_q, GND_q)
    BEGIN
        CASE (muxAccOverflowFeedbackSignal_uid61_fpAccTest_s) IS
            WHEN "0" => muxAccOverflowFeedbackSignal_uid61_fpAccTest_q <= oRAccOverflowFlagFeedback_uid62_fpAccTest_q;
            WHEN "1" => muxAccOverflowFeedbackSignal_uid61_fpAccTest_q <= GND_q;
            WHEN OTHERS => muxAccOverflowFeedbackSignal_uid61_fpAccTest_q <= (others => '0');
        END CASE;
    END PROCESS;

    -- oRAccOverflowFlagFeedback_uid62_fpAccTest(LOGICAL,61)@1 + 1
    oRAccOverflowFlagFeedback_uid62_fpAccTest_qi <= muxAccOverflowFeedbackSignal_uid61_fpAccTest_q or accOverflow_uid32_fpAccTest_q;
    oRAccOverflowFlagFeedback_uid62_fpAccTest_delay : dspba_delay
    GENERIC MAP ( width => 1, depth => 1, reset_kind => "ASYNC" )
    PORT MAP ( xin => oRAccOverflowFlagFeedback_uid62_fpAccTest_qi, xout => oRAccOverflowFlagFeedback_uid62_fpAccTest_q, clk => clk, aclr => areset );

    -- delayedAccOverflowFeedbackSignal_uid60_fpAccTest(DELAY,59)
    delayedAccOverflowFeedbackSignal_uid60_fpAccTest : dspba_delay
    GENERIC MAP ( width => 1, depth => 1, reset_kind => "ASYNC" )
    PORT MAP ( xin => oRAccOverflowFlagFeedback_uid62_fpAccTest_q, xout => delayedAccOverflowFeedbackSignal_uid60_fpAccTest_q, clk => clk, aclr => areset );

    -- expNotZero_uid56_fpAccTest(LOGICAL,55)@0
    expNotZero_uid56_fpAccTest_q <= "1" WHEN expX_uid6_fpAccTest_b /= "00000000" ELSE "0";

    -- expLTLSBA_uid11_fpAccTest(CONSTANT,10)
    expLTLSBA_uid11_fpAccTest_q <= "01100101";

    -- cmpLT_expX_expLTLSBA_uid12_fpAccTest(COMPARE,11)@0
    cmpLT_expX_expLTLSBA_uid12_fpAccTest_a <= STD_LOGIC_VECTOR("00" & expX_uid6_fpAccTest_b);
    cmpLT_expX_expLTLSBA_uid12_fpAccTest_b <= STD_LOGIC_VECTOR("00" & expLTLSBA_uid11_fpAccTest_q);
    cmpLT_expX_expLTLSBA_uid12_fpAccTest_o <= STD_LOGIC_VECTOR(UNSIGNED(cmpLT_expX_expLTLSBA_uid12_fpAccTest_a) - UNSIGNED(cmpLT_expX_expLTLSBA_uid12_fpAccTest_b));
    cmpLT_expX_expLTLSBA_uid12_fpAccTest_c(0) <= cmpLT_expX_expLTLSBA_uid12_fpAccTest_o(9);

    -- underflowCond_uid57_fpAccTest(LOGICAL,56)@0
    underflowCond_uid57_fpAccTest_q <= cmpLT_expX_expLTLSBA_uid12_fpAccTest_c and expNotZero_uid56_fpAccTest_q;

    -- muxXUnderflowFeedbackSignal_uid55_fpAccTest(MUX,54)@0
    muxXUnderflowFeedbackSignal_uid55_fpAccTest_s <= n;
    muxXUnderflowFeedbackSignal_uid55_fpAccTest_combproc: PROCESS (muxXUnderflowFeedbackSignal_uid55_fpAccTest_s, oRXUnderflowFlagFeedback_uid58_fpAccTest_q, GND_q)
    BEGIN
        CASE (muxXUnderflowFeedbackSignal_uid55_fpAccTest_s) IS
            WHEN "0" => muxXUnderflowFeedbackSignal_uid55_fpAccTest_q <= oRXUnderflowFlagFeedback_uid58_fpAccTest_q;
            WHEN "1" => muxXUnderflowFeedbackSignal_uid55_fpAccTest_q <= GND_q;
            WHEN OTHERS => muxXUnderflowFeedbackSignal_uid55_fpAccTest_q <= (others => '0');
        END CASE;
    END PROCESS;

    -- oRXUnderflowFlagFeedback_uid58_fpAccTest(LOGICAL,57)@0 + 1
    oRXUnderflowFlagFeedback_uid58_fpAccTest_qi <= muxXUnderflowFeedbackSignal_uid55_fpAccTest_q or underflowCond_uid57_fpAccTest_q;
    oRXUnderflowFlagFeedback_uid58_fpAccTest_delay : dspba_delay
    GENERIC MAP ( width => 1, depth => 1, reset_kind => "ASYNC" )
    PORT MAP ( xin => oRXUnderflowFlagFeedback_uid58_fpAccTest_qi, xout => oRXUnderflowFlagFeedback_uid58_fpAccTest_q, clk => clk, aclr => areset );

    -- redist1_oRXUnderflowFlagFeedback_uid58_fpAccTest_q_3(DELAY,190)
    redist1_oRXUnderflowFlagFeedback_uid58_fpAccTest_q_3 : dspba_delay
    GENERIC MAP ( width => 1, depth => 2, reset_kind => "ASYNC" )
    PORT MAP ( xin => oRXUnderflowFlagFeedback_uid58_fpAccTest_q, xout => redist1_oRXUnderflowFlagFeedback_uid58_fpAccTest_q_3_q, clk => clk, aclr => areset );

    -- expGTMaxMSBX_uid13_fpAccTest(CONSTANT,12)
    expGTMaxMSBX_uid13_fpAccTest_q <= "10010000";

    -- cmpGT_expX_expGTMaxMSBX_uid14_fpAccTest(COMPARE,13)@0 + 1
    cmpGT_expX_expGTMaxMSBX_uid14_fpAccTest_a <= STD_LOGIC_VECTOR("00" & expGTMaxMSBX_uid13_fpAccTest_q);
    cmpGT_expX_expGTMaxMSBX_uid14_fpAccTest_b <= STD_LOGIC_VECTOR("00" & expX_uid6_fpAccTest_b);
    cmpGT_expX_expGTMaxMSBX_uid14_fpAccTest_clkproc: PROCESS (clk, areset)
    BEGIN
        IF (areset = '1') THEN
            cmpGT_expX_expGTMaxMSBX_uid14_fpAccTest_o <= (others => '0');
        ELSIF (clk'EVENT AND clk = '1') THEN
            cmpGT_expX_expGTMaxMSBX_uid14_fpAccTest_o <= STD_LOGIC_VECTOR(UNSIGNED(cmpGT_expX_expGTMaxMSBX_uid14_fpAccTest_a) - UNSIGNED(cmpGT_expX_expGTMaxMSBX_uid14_fpAccTest_b));
        END IF;
    END PROCESS;
    cmpGT_expX_expGTMaxMSBX_uid14_fpAccTest_c(0) <= cmpGT_expX_expGTMaxMSBX_uid14_fpAccTest_o(9);

    -- muxXOverflowFeedbackSignal_uid51_fpAccTest(MUX,50)@1
    muxXOverflowFeedbackSignal_uid51_fpAccTest_s <= redist5_xIn_n_1_q;
    muxXOverflowFeedbackSignal_uid51_fpAccTest_combproc: PROCESS (muxXOverflowFeedbackSignal_uid51_fpAccTest_s, oRXOverflowFlagFeedback_uid52_fpAccTest_q, GND_q)
    BEGIN
        CASE (muxXOverflowFeedbackSignal_uid51_fpAccTest_s) IS
            WHEN "0" => muxXOverflowFeedbackSignal_uid51_fpAccTest_q <= oRXOverflowFlagFeedback_uid52_fpAccTest_q;
            WHEN "1" => muxXOverflowFeedbackSignal_uid51_fpAccTest_q <= GND_q;
            WHEN OTHERS => muxXOverflowFeedbackSignal_uid51_fpAccTest_q <= (others => '0');
        END CASE;
    END PROCESS;

    -- oRXOverflowFlagFeedback_uid52_fpAccTest(LOGICAL,51)@1 + 1
    oRXOverflowFlagFeedback_uid52_fpAccTest_qi <= muxXOverflowFeedbackSignal_uid51_fpAccTest_q or cmpGT_expX_expGTMaxMSBX_uid14_fpAccTest_c;
    oRXOverflowFlagFeedback_uid52_fpAccTest_delay : dspba_delay
    GENERIC MAP ( width => 1, depth => 1, reset_kind => "ASYNC" )
    PORT MAP ( xin => oRXOverflowFlagFeedback_uid52_fpAccTest_qi, xout => oRXOverflowFlagFeedback_uid52_fpAccTest_q, clk => clk, aclr => areset );

    -- delayedXOverflowFeedbackSignal_uid50_fpAccTest(DELAY,49)
    delayedXOverflowFeedbackSignal_uid50_fpAccTest : dspba_delay
    GENERIC MAP ( width => 1, depth => 1, reset_kind => "ASYNC" )
    PORT MAP ( xin => oRXOverflowFlagFeedback_uid52_fpAccTest_q, xout => delayedXOverflowFeedbackSignal_uid50_fpAccTest_q, clk => clk, aclr => areset );

    -- redist4_accumulatorSign_uid29_fpAccTest_b_2(DELAY,193)
    redist4_accumulatorSign_uid29_fpAccTest_b_2 : dspba_delay
    GENERIC MAP ( width => 1, depth => 2, reset_kind => "ASYNC" )
    PORT MAP ( xin => accumulatorSign_uid29_fpAccTest_b, xout => redist4_accumulatorSign_uid29_fpAccTest_b_2_q, clk => clk, aclr => areset );

    -- ShiftedOutComparator_uid38_fpAccTest(CONSTANT,37)
    ShiftedOutComparator_uid38_fpAccTest_q <= "111000";

    -- accResOutOfExpRange_uid39_fpAccTest(LOGICAL,38)@2
    accResOutOfExpRange_uid39_fpAccTest_q <= "1" WHEN ShiftedOutComparator_uid38_fpAccTest_q = r_uid101_zeroCounter_uid37_fpAccTest_q ELSE "0";

    -- accValidRange_uid33_fpAccTest(BITSELECT,32)@1
    accValidRange_uid33_fpAccTest_in <= sum_uid27_fpAccTest_b(56 downto 0);
    accValidRange_uid33_fpAccTest_b <= accValidRange_uid33_fpAccTest_in(56 downto 0);

    -- accOnesComplement_uid34_fpAccTest(LOGICAL,33)@1
    accOnesComplement_uid34_fpAccTest_b <= STD_LOGIC_VECTOR(STD_LOGIC_VECTOR((56 downto 1 => accumulatorSign_uid29_fpAccTest_b(0)) & accumulatorSign_uid29_fpAccTest_b));
    accOnesComplement_uid34_fpAccTest_q <= accValidRange_uid33_fpAccTest_b xor accOnesComplement_uid34_fpAccTest_b;

    -- accValuePositive_uid35_fpAccTest(ADD,34)@1 + 1
    accValuePositive_uid35_fpAccTest_a <= STD_LOGIC_VECTOR("0" & accOnesComplement_uid34_fpAccTest_q);
    accValuePositive_uid35_fpAccTest_b <= STD_LOGIC_VECTOR("000000000000000000000000000000000000000000000000000000000" & accumulatorSign_uid29_fpAccTest_b);
    accValuePositive_uid35_fpAccTest_clkproc: PROCESS (clk, areset)
    BEGIN
        IF (areset = '1') THEN
            accValuePositive_uid35_fpAccTest_o <= (others => '0');
        ELSIF (clk'EVENT AND clk = '1') THEN
            accValuePositive_uid35_fpAccTest_o <= STD_LOGIC_VECTOR(UNSIGNED(accValuePositive_uid35_fpAccTest_a) + UNSIGNED(accValuePositive_uid35_fpAccTest_b));
        END IF;
    END PROCESS;
    accValuePositive_uid35_fpAccTest_q <= accValuePositive_uid35_fpAccTest_o(57 downto 0);

    -- posAccWoLeadingZeroBit_uid36_fpAccTest(BITSELECT,35)@2
    posAccWoLeadingZeroBit_uid36_fpAccTest_in <= accValuePositive_uid35_fpAccTest_q(55 downto 0);
    posAccWoLeadingZeroBit_uid36_fpAccTest_b <= posAccWoLeadingZeroBit_uid36_fpAccTest_in(55 downto 0);

    -- rVStage_uid67_zeroCounter_uid37_fpAccTest_merged_bit_select(BITSELECT,183)@2
    rVStage_uid67_zeroCounter_uid37_fpAccTest_merged_bit_select_b <= posAccWoLeadingZeroBit_uid36_fpAccTest_b(55 downto 24);
    rVStage_uid67_zeroCounter_uid37_fpAccTest_merged_bit_select_c <= posAccWoLeadingZeroBit_uid36_fpAccTest_b(23 downto 0);

    -- vCount_uid68_zeroCounter_uid37_fpAccTest(LOGICAL,67)@2
    vCount_uid68_zeroCounter_uid37_fpAccTest_q <= "1" WHEN rVStage_uid67_zeroCounter_uid37_fpAccTest_merged_bit_select_b = zs_uid66_zeroCounter_uid37_fpAccTest_q ELSE "0";

    -- mO_uid69_zeroCounter_uid37_fpAccTest(CONSTANT,68)
    mO_uid69_zeroCounter_uid37_fpAccTest_q <= "11111111";

    -- cStage_uid71_zeroCounter_uid37_fpAccTest(BITJOIN,70)@2
    cStage_uid71_zeroCounter_uid37_fpAccTest_q <= rVStage_uid67_zeroCounter_uid37_fpAccTest_merged_bit_select_c & mO_uid69_zeroCounter_uid37_fpAccTest_q;

    -- vStagei_uid73_zeroCounter_uid37_fpAccTest(MUX,72)@2
    vStagei_uid73_zeroCounter_uid37_fpAccTest_s <= vCount_uid68_zeroCounter_uid37_fpAccTest_q;
    vStagei_uid73_zeroCounter_uid37_fpAccTest_combproc: PROCESS (vStagei_uid73_zeroCounter_uid37_fpAccTest_s, rVStage_uid67_zeroCounter_uid37_fpAccTest_merged_bit_select_b, cStage_uid71_zeroCounter_uid37_fpAccTest_q)
    BEGIN
        CASE (vStagei_uid73_zeroCounter_uid37_fpAccTest_s) IS
            WHEN "0" => vStagei_uid73_zeroCounter_uid37_fpAccTest_q <= rVStage_uid67_zeroCounter_uid37_fpAccTest_merged_bit_select_b;
            WHEN "1" => vStagei_uid73_zeroCounter_uid37_fpAccTest_q <= cStage_uid71_zeroCounter_uid37_fpAccTest_q;
            WHEN OTHERS => vStagei_uid73_zeroCounter_uid37_fpAccTest_q <= (others => '0');
        END CASE;
    END PROCESS;

    -- rVStage_uid75_zeroCounter_uid37_fpAccTest_merged_bit_select(BITSELECT,184)@2
    rVStage_uid75_zeroCounter_uid37_fpAccTest_merged_bit_select_b <= vStagei_uid73_zeroCounter_uid37_fpAccTest_q(31 downto 16);
    rVStage_uid75_zeroCounter_uid37_fpAccTest_merged_bit_select_c <= vStagei_uid73_zeroCounter_uid37_fpAccTest_q(15 downto 0);

    -- vCount_uid76_zeroCounter_uid37_fpAccTest(LOGICAL,75)@2
    vCount_uid76_zeroCounter_uid37_fpAccTest_q <= "1" WHEN rVStage_uid75_zeroCounter_uid37_fpAccTest_merged_bit_select_b = zs_uid74_zeroCounter_uid37_fpAccTest_q ELSE "0";

    -- vStagei_uid79_zeroCounter_uid37_fpAccTest(MUX,78)@2
    vStagei_uid79_zeroCounter_uid37_fpAccTest_s <= vCount_uid76_zeroCounter_uid37_fpAccTest_q;
    vStagei_uid79_zeroCounter_uid37_fpAccTest_combproc: PROCESS (vStagei_uid79_zeroCounter_uid37_fpAccTest_s, rVStage_uid75_zeroCounter_uid37_fpAccTest_merged_bit_select_b, rVStage_uid75_zeroCounter_uid37_fpAccTest_merged_bit_select_c)
    BEGIN
        CASE (vStagei_uid79_zeroCounter_uid37_fpAccTest_s) IS
            WHEN "0" => vStagei_uid79_zeroCounter_uid37_fpAccTest_q <= rVStage_uid75_zeroCounter_uid37_fpAccTest_merged_bit_select_b;
            WHEN "1" => vStagei_uid79_zeroCounter_uid37_fpAccTest_q <= rVStage_uid75_zeroCounter_uid37_fpAccTest_merged_bit_select_c;
            WHEN OTHERS => vStagei_uid79_zeroCounter_uid37_fpAccTest_q <= (others => '0');
        END CASE;
    END PROCESS;

    -- rVStage_uid81_zeroCounter_uid37_fpAccTest_merged_bit_select(BITSELECT,185)@2
    rVStage_uid81_zeroCounter_uid37_fpAccTest_merged_bit_select_b <= vStagei_uid79_zeroCounter_uid37_fpAccTest_q(15 downto 8);
    rVStage_uid81_zeroCounter_uid37_fpAccTest_merged_bit_select_c <= vStagei_uid79_zeroCounter_uid37_fpAccTest_q(7 downto 0);

    -- vCount_uid82_zeroCounter_uid37_fpAccTest(LOGICAL,81)@2
    vCount_uid82_zeroCounter_uid37_fpAccTest_q <= "1" WHEN rVStage_uid81_zeroCounter_uid37_fpAccTest_merged_bit_select_b = zeroExponent_uid42_fpAccTest_q ELSE "0";

    -- vStagei_uid85_zeroCounter_uid37_fpAccTest(MUX,84)@2
    vStagei_uid85_zeroCounter_uid37_fpAccTest_s <= vCount_uid82_zeroCounter_uid37_fpAccTest_q;
    vStagei_uid85_zeroCounter_uid37_fpAccTest_combproc: PROCESS (vStagei_uid85_zeroCounter_uid37_fpAccTest_s, rVStage_uid81_zeroCounter_uid37_fpAccTest_merged_bit_select_b, rVStage_uid81_zeroCounter_uid37_fpAccTest_merged_bit_select_c)
    BEGIN
        CASE (vStagei_uid85_zeroCounter_uid37_fpAccTest_s) IS
            WHEN "0" => vStagei_uid85_zeroCounter_uid37_fpAccTest_q <= rVStage_uid81_zeroCounter_uid37_fpAccTest_merged_bit_select_b;
            WHEN "1" => vStagei_uid85_zeroCounter_uid37_fpAccTest_q <= rVStage_uid81_zeroCounter_uid37_fpAccTest_merged_bit_select_c;
            WHEN OTHERS => vStagei_uid85_zeroCounter_uid37_fpAccTest_q <= (others => '0');
        END CASE;
    END PROCESS;

    -- rVStage_uid87_zeroCounter_uid37_fpAccTest_merged_bit_select(BITSELECT,186)@2
    rVStage_uid87_zeroCounter_uid37_fpAccTest_merged_bit_select_b <= vStagei_uid85_zeroCounter_uid37_fpAccTest_q(7 downto 4);
    rVStage_uid87_zeroCounter_uid37_fpAccTest_merged_bit_select_c <= vStagei_uid85_zeroCounter_uid37_fpAccTest_q(3 downto 0);

    -- vCount_uid88_zeroCounter_uid37_fpAccTest(LOGICAL,87)@2
    vCount_uid88_zeroCounter_uid37_fpAccTest_q <= "1" WHEN rVStage_uid87_zeroCounter_uid37_fpAccTest_merged_bit_select_b = zs_uid86_zeroCounter_uid37_fpAccTest_q ELSE "0";

    -- vStagei_uid91_zeroCounter_uid37_fpAccTest(MUX,90)@2
    vStagei_uid91_zeroCounter_uid37_fpAccTest_s <= vCount_uid88_zeroCounter_uid37_fpAccTest_q;
    vStagei_uid91_zeroCounter_uid37_fpAccTest_combproc: PROCESS (vStagei_uid91_zeroCounter_uid37_fpAccTest_s, rVStage_uid87_zeroCounter_uid37_fpAccTest_merged_bit_select_b, rVStage_uid87_zeroCounter_uid37_fpAccTest_merged_bit_select_c)
    BEGIN
        CASE (vStagei_uid91_zeroCounter_uid37_fpAccTest_s) IS
            WHEN "0" => vStagei_uid91_zeroCounter_uid37_fpAccTest_q <= rVStage_uid87_zeroCounter_uid37_fpAccTest_merged_bit_select_b;
            WHEN "1" => vStagei_uid91_zeroCounter_uid37_fpAccTest_q <= rVStage_uid87_zeroCounter_uid37_fpAccTest_merged_bit_select_c;
            WHEN OTHERS => vStagei_uid91_zeroCounter_uid37_fpAccTest_q <= (others => '0');
        END CASE;
    END PROCESS;

    -- rVStage_uid93_zeroCounter_uid37_fpAccTest_merged_bit_select(BITSELECT,187)@2
    rVStage_uid93_zeroCounter_uid37_fpAccTest_merged_bit_select_b <= vStagei_uid91_zeroCounter_uid37_fpAccTest_q(3 downto 2);
    rVStage_uid93_zeroCounter_uid37_fpAccTest_merged_bit_select_c <= vStagei_uid91_zeroCounter_uid37_fpAccTest_q(1 downto 0);

    -- vCount_uid94_zeroCounter_uid37_fpAccTest(LOGICAL,93)@2
    vCount_uid94_zeroCounter_uid37_fpAccTest_q <= "1" WHEN rVStage_uid93_zeroCounter_uid37_fpAccTest_merged_bit_select_b = zs_uid92_zeroCounter_uid37_fpAccTest_q ELSE "0";

    -- vStagei_uid97_zeroCounter_uid37_fpAccTest(MUX,96)@2
    vStagei_uid97_zeroCounter_uid37_fpAccTest_s <= vCount_uid94_zeroCounter_uid37_fpAccTest_q;
    vStagei_uid97_zeroCounter_uid37_fpAccTest_combproc: PROCESS (vStagei_uid97_zeroCounter_uid37_fpAccTest_s, rVStage_uid93_zeroCounter_uid37_fpAccTest_merged_bit_select_b, rVStage_uid93_zeroCounter_uid37_fpAccTest_merged_bit_select_c)
    BEGIN
        CASE (vStagei_uid97_zeroCounter_uid37_fpAccTest_s) IS
            WHEN "0" => vStagei_uid97_zeroCounter_uid37_fpAccTest_q <= rVStage_uid93_zeroCounter_uid37_fpAccTest_merged_bit_select_b;
            WHEN "1" => vStagei_uid97_zeroCounter_uid37_fpAccTest_q <= rVStage_uid93_zeroCounter_uid37_fpAccTest_merged_bit_select_c;
            WHEN OTHERS => vStagei_uid97_zeroCounter_uid37_fpAccTest_q <= (others => '0');
        END CASE;
    END PROCESS;

    -- rVStage_uid99_zeroCounter_uid37_fpAccTest(BITSELECT,98)@2
    rVStage_uid99_zeroCounter_uid37_fpAccTest_b <= vStagei_uid97_zeroCounter_uid37_fpAccTest_q(1 downto 1);

    -- vCount_uid100_zeroCounter_uid37_fpAccTest(LOGICAL,99)@2
    vCount_uid100_zeroCounter_uid37_fpAccTest_q <= "1" WHEN rVStage_uid99_zeroCounter_uid37_fpAccTest_b = GND_q ELSE "0";

    -- r_uid101_zeroCounter_uid37_fpAccTest(BITJOIN,100)@2
    r_uid101_zeroCounter_uid37_fpAccTest_q <= vCount_uid68_zeroCounter_uid37_fpAccTest_q & vCount_uid76_zeroCounter_uid37_fpAccTest_q & vCount_uid82_zeroCounter_uid37_fpAccTest_q & vCount_uid88_zeroCounter_uid37_fpAccTest_q & vCount_uid94_zeroCounter_uid37_fpAccTest_q & vCount_uid100_zeroCounter_uid37_fpAccTest_q;

    -- expRBias_uid41_fpAccTest(CONSTANT,40)
    expRBias_uid41_fpAccTest_q <= "010011101";

    -- resExpSub_uid43_fpAccTest_finalExpUpdated_uid45_fpAccTest_merged(SUB,181)@2 + 1
    resExpSub_uid43_fpAccTest_finalExpUpdated_uid45_fpAccTest_merged_a <= expRBias_uid41_fpAccTest_q;
    resExpSub_uid43_fpAccTest_finalExpUpdated_uid45_fpAccTest_merged_b <= STD_LOGIC_VECTOR("000" & r_uid101_zeroCounter_uid37_fpAccTest_q);
    resExpSub_uid43_fpAccTest_finalExpUpdated_uid45_fpAccTest_merged_i <= "0" & zeroExponent_uid42_fpAccTest_q;
    resExpSub_uid43_fpAccTest_finalExpUpdated_uid45_fpAccTest_merged_clkproc: PROCESS (clk, areset)
    BEGIN
        IF (areset = '1') THEN
            resExpSub_uid43_fpAccTest_finalExpUpdated_uid45_fpAccTest_merged_o <= (others => '0');
        ELSIF (clk'EVENT AND clk = '1') THEN
            IF (accResOutOfExpRange_uid39_fpAccTest_q = "1") THEN
                resExpSub_uid43_fpAccTest_finalExpUpdated_uid45_fpAccTest_merged_o <= resExpSub_uid43_fpAccTest_finalExpUpdated_uid45_fpAccTest_merged_i;
            ELSE
                resExpSub_uid43_fpAccTest_finalExpUpdated_uid45_fpAccTest_merged_o <= STD_LOGIC_VECTOR(UNSIGNED(resExpSub_uid43_fpAccTest_finalExpUpdated_uid45_fpAccTest_merged_a) - UNSIGNED(resExpSub_uid43_fpAccTest_finalExpUpdated_uid45_fpAccTest_merged_b));
            END IF;
        END IF;
    END PROCESS;
    resExpSub_uid43_fpAccTest_finalExpUpdated_uid45_fpAccTest_merged_q <= resExpSub_uid43_fpAccTest_finalExpUpdated_uid45_fpAccTest_merged_o(7 downto 0);

    -- leftShiftStage2Idx3Rng3_uid177_normalizationShifter_uid40_fpAccTest(BITSELECT,176)@2
    leftShiftStage2Idx3Rng3_uid177_normalizationShifter_uid40_fpAccTest_in <= leftShiftStage1_uid169_normalizationShifter_uid40_fpAccTest_q(54 downto 0);
    leftShiftStage2Idx3Rng3_uid177_normalizationShifter_uid40_fpAccTest_b <= leftShiftStage2Idx3Rng3_uid177_normalizationShifter_uid40_fpAccTest_in(54 downto 0);

    -- leftShiftStage2Idx3Pad3_uid176_normalizationShifter_uid40_fpAccTest(CONSTANT,175)
    leftShiftStage2Idx3Pad3_uid176_normalizationShifter_uid40_fpAccTest_q <= "000";

    -- leftShiftStage2Idx3_uid178_normalizationShifter_uid40_fpAccTest(BITJOIN,177)@2
    leftShiftStage2Idx3_uid178_normalizationShifter_uid40_fpAccTest_q <= leftShiftStage2Idx3Rng3_uid177_normalizationShifter_uid40_fpAccTest_b & leftShiftStage2Idx3Pad3_uid176_normalizationShifter_uid40_fpAccTest_q;

    -- leftShiftStage2Idx2Rng2_uid174_normalizationShifter_uid40_fpAccTest(BITSELECT,173)@2
    leftShiftStage2Idx2Rng2_uid174_normalizationShifter_uid40_fpAccTest_in <= leftShiftStage1_uid169_normalizationShifter_uid40_fpAccTest_q(55 downto 0);
    leftShiftStage2Idx2Rng2_uid174_normalizationShifter_uid40_fpAccTest_b <= leftShiftStage2Idx2Rng2_uid174_normalizationShifter_uid40_fpAccTest_in(55 downto 0);

    -- leftShiftStage2Idx2_uid175_normalizationShifter_uid40_fpAccTest(BITJOIN,174)@2
    leftShiftStage2Idx2_uid175_normalizationShifter_uid40_fpAccTest_q <= leftShiftStage2Idx2Rng2_uid174_normalizationShifter_uid40_fpAccTest_b & zs_uid92_zeroCounter_uid37_fpAccTest_q;

    -- leftShiftStage2Idx1Rng1_uid171_normalizationShifter_uid40_fpAccTest(BITSELECT,170)@2
    leftShiftStage2Idx1Rng1_uid171_normalizationShifter_uid40_fpAccTest_in <= leftShiftStage1_uid169_normalizationShifter_uid40_fpAccTest_q(56 downto 0);
    leftShiftStage2Idx1Rng1_uid171_normalizationShifter_uid40_fpAccTest_b <= leftShiftStage2Idx1Rng1_uid171_normalizationShifter_uid40_fpAccTest_in(56 downto 0);

    -- leftShiftStage2Idx1_uid172_normalizationShifter_uid40_fpAccTest(BITJOIN,171)@2
    leftShiftStage2Idx1_uid172_normalizationShifter_uid40_fpAccTest_q <= leftShiftStage2Idx1Rng1_uid171_normalizationShifter_uid40_fpAccTest_b & GND_q;

    -- leftShiftStage1Idx3Rng12_uid166_normalizationShifter_uid40_fpAccTest(BITSELECT,165)@2
    leftShiftStage1Idx3Rng12_uid166_normalizationShifter_uid40_fpAccTest_in <= leftShiftStage0_uid158_normalizationShifter_uid40_fpAccTest_q(45 downto 0);
    leftShiftStage1Idx3Rng12_uid166_normalizationShifter_uid40_fpAccTest_b <= leftShiftStage1Idx3Rng12_uid166_normalizationShifter_uid40_fpAccTest_in(45 downto 0);

    -- leftShiftStage1Idx3Pad12_uid165_normalizationShifter_uid40_fpAccTest(CONSTANT,164)
    leftShiftStage1Idx3Pad12_uid165_normalizationShifter_uid40_fpAccTest_q <= "000000000000";

    -- leftShiftStage1Idx3_uid167_normalizationShifter_uid40_fpAccTest(BITJOIN,166)@2
    leftShiftStage1Idx3_uid167_normalizationShifter_uid40_fpAccTest_q <= leftShiftStage1Idx3Rng12_uid166_normalizationShifter_uid40_fpAccTest_b & leftShiftStage1Idx3Pad12_uid165_normalizationShifter_uid40_fpAccTest_q;

    -- leftShiftStage1Idx2Rng8_uid163_normalizationShifter_uid40_fpAccTest(BITSELECT,162)@2
    leftShiftStage1Idx2Rng8_uid163_normalizationShifter_uid40_fpAccTest_in <= leftShiftStage0_uid158_normalizationShifter_uid40_fpAccTest_q(49 downto 0);
    leftShiftStage1Idx2Rng8_uid163_normalizationShifter_uid40_fpAccTest_b <= leftShiftStage1Idx2Rng8_uid163_normalizationShifter_uid40_fpAccTest_in(49 downto 0);

    -- leftShiftStage1Idx2_uid164_normalizationShifter_uid40_fpAccTest(BITJOIN,163)@2
    leftShiftStage1Idx2_uid164_normalizationShifter_uid40_fpAccTest_q <= leftShiftStage1Idx2Rng8_uid163_normalizationShifter_uid40_fpAccTest_b & zeroExponent_uid42_fpAccTest_q;

    -- leftShiftStage1Idx1Rng4_uid160_normalizationShifter_uid40_fpAccTest(BITSELECT,159)@2
    leftShiftStage1Idx1Rng4_uid160_normalizationShifter_uid40_fpAccTest_in <= leftShiftStage0_uid158_normalizationShifter_uid40_fpAccTest_q(53 downto 0);
    leftShiftStage1Idx1Rng4_uid160_normalizationShifter_uid40_fpAccTest_b <= leftShiftStage1Idx1Rng4_uid160_normalizationShifter_uid40_fpAccTest_in(53 downto 0);

    -- leftShiftStage1Idx1_uid161_normalizationShifter_uid40_fpAccTest(BITJOIN,160)@2
    leftShiftStage1Idx1_uid161_normalizationShifter_uid40_fpAccTest_q <= leftShiftStage1Idx1Rng4_uid160_normalizationShifter_uid40_fpAccTest_b & zs_uid86_zeroCounter_uid37_fpAccTest_q;

    -- leftShiftStage0Idx3Rng48_uid155_normalizationShifter_uid40_fpAccTest(BITSELECT,154)@2
    leftShiftStage0Idx3Rng48_uid155_normalizationShifter_uid40_fpAccTest_in <= accValuePositive_uid35_fpAccTest_q(9 downto 0);
    leftShiftStage0Idx3Rng48_uid155_normalizationShifter_uid40_fpAccTest_b <= leftShiftStage0Idx3Rng48_uid155_normalizationShifter_uid40_fpAccTest_in(9 downto 0);

    -- leftShiftStage0Idx3Pad48_uid154_normalizationShifter_uid40_fpAccTest(CONSTANT,153)
    leftShiftStage0Idx3Pad48_uid154_normalizationShifter_uid40_fpAccTest_q <= "000000000000000000000000000000000000000000000000";

    -- leftShiftStage0Idx3_uid156_normalizationShifter_uid40_fpAccTest(BITJOIN,155)@2
    leftShiftStage0Idx3_uid156_normalizationShifter_uid40_fpAccTest_q <= leftShiftStage0Idx3Rng48_uid155_normalizationShifter_uid40_fpAccTest_b & leftShiftStage0Idx3Pad48_uid154_normalizationShifter_uid40_fpAccTest_q;

    -- leftShiftStage0Idx2Rng32_uid152_normalizationShifter_uid40_fpAccTest(BITSELECT,151)@2
    leftShiftStage0Idx2Rng32_uid152_normalizationShifter_uid40_fpAccTest_in <= accValuePositive_uid35_fpAccTest_q(25 downto 0);
    leftShiftStage0Idx2Rng32_uid152_normalizationShifter_uid40_fpAccTest_b <= leftShiftStage0Idx2Rng32_uid152_normalizationShifter_uid40_fpAccTest_in(25 downto 0);

    -- leftShiftStage0Idx2_uid153_normalizationShifter_uid40_fpAccTest(BITJOIN,152)@2
    leftShiftStage0Idx2_uid153_normalizationShifter_uid40_fpAccTest_q <= leftShiftStage0Idx2Rng32_uid152_normalizationShifter_uid40_fpAccTest_b & zs_uid66_zeroCounter_uid37_fpAccTest_q;

    -- leftShiftStage0Idx1Rng16_uid149_normalizationShifter_uid40_fpAccTest(BITSELECT,148)@2
    leftShiftStage0Idx1Rng16_uid149_normalizationShifter_uid40_fpAccTest_in <= accValuePositive_uid35_fpAccTest_q(41 downto 0);
    leftShiftStage0Idx1Rng16_uid149_normalizationShifter_uid40_fpAccTest_b <= leftShiftStage0Idx1Rng16_uid149_normalizationShifter_uid40_fpAccTest_in(41 downto 0);

    -- leftShiftStage0Idx1_uid150_normalizationShifter_uid40_fpAccTest(BITJOIN,149)@2
    leftShiftStage0Idx1_uid150_normalizationShifter_uid40_fpAccTest_q <= leftShiftStage0Idx1Rng16_uid149_normalizationShifter_uid40_fpAccTest_b & zs_uid74_zeroCounter_uid37_fpAccTest_q;

    -- leftShiftStage0_uid158_normalizationShifter_uid40_fpAccTest(MUX,157)@2
    leftShiftStage0_uid158_normalizationShifter_uid40_fpAccTest_s <= leftShiftStageSel5Dto4_uid157_normalizationShifter_uid40_fpAccTest_merged_bit_select_b;
    leftShiftStage0_uid158_normalizationShifter_uid40_fpAccTest_combproc: PROCESS (leftShiftStage0_uid158_normalizationShifter_uid40_fpAccTest_s, accValuePositive_uid35_fpAccTest_q, leftShiftStage0Idx1_uid150_normalizationShifter_uid40_fpAccTest_q, leftShiftStage0Idx2_uid153_normalizationShifter_uid40_fpAccTest_q, leftShiftStage0Idx3_uid156_normalizationShifter_uid40_fpAccTest_q)
    BEGIN
        CASE (leftShiftStage0_uid158_normalizationShifter_uid40_fpAccTest_s) IS
            WHEN "00" => leftShiftStage0_uid158_normalizationShifter_uid40_fpAccTest_q <= accValuePositive_uid35_fpAccTest_q;
            WHEN "01" => leftShiftStage0_uid158_normalizationShifter_uid40_fpAccTest_q <= leftShiftStage0Idx1_uid150_normalizationShifter_uid40_fpAccTest_q;
            WHEN "10" => leftShiftStage0_uid158_normalizationShifter_uid40_fpAccTest_q <= leftShiftStage0Idx2_uid153_normalizationShifter_uid40_fpAccTest_q;
            WHEN "11" => leftShiftStage0_uid158_normalizationShifter_uid40_fpAccTest_q <= leftShiftStage0Idx3_uid156_normalizationShifter_uid40_fpAccTest_q;
            WHEN OTHERS => leftShiftStage0_uid158_normalizationShifter_uid40_fpAccTest_q <= (others => '0');
        END CASE;
    END PROCESS;

    -- leftShiftStage1_uid169_normalizationShifter_uid40_fpAccTest(MUX,168)@2
    leftShiftStage1_uid169_normalizationShifter_uid40_fpAccTest_s <= leftShiftStageSel5Dto4_uid157_normalizationShifter_uid40_fpAccTest_merged_bit_select_c;
    leftShiftStage1_uid169_normalizationShifter_uid40_fpAccTest_combproc: PROCESS (leftShiftStage1_uid169_normalizationShifter_uid40_fpAccTest_s, leftShiftStage0_uid158_normalizationShifter_uid40_fpAccTest_q, leftShiftStage1Idx1_uid161_normalizationShifter_uid40_fpAccTest_q, leftShiftStage1Idx2_uid164_normalizationShifter_uid40_fpAccTest_q, leftShiftStage1Idx3_uid167_normalizationShifter_uid40_fpAccTest_q)
    BEGIN
        CASE (leftShiftStage1_uid169_normalizationShifter_uid40_fpAccTest_s) IS
            WHEN "00" => leftShiftStage1_uid169_normalizationShifter_uid40_fpAccTest_q <= leftShiftStage0_uid158_normalizationShifter_uid40_fpAccTest_q;
            WHEN "01" => leftShiftStage1_uid169_normalizationShifter_uid40_fpAccTest_q <= leftShiftStage1Idx1_uid161_normalizationShifter_uid40_fpAccTest_q;
            WHEN "10" => leftShiftStage1_uid169_normalizationShifter_uid40_fpAccTest_q <= leftShiftStage1Idx2_uid164_normalizationShifter_uid40_fpAccTest_q;
            WHEN "11" => leftShiftStage1_uid169_normalizationShifter_uid40_fpAccTest_q <= leftShiftStage1Idx3_uid167_normalizationShifter_uid40_fpAccTest_q;
            WHEN OTHERS => leftShiftStage1_uid169_normalizationShifter_uid40_fpAccTest_q <= (others => '0');
        END CASE;
    END PROCESS;

    -- leftShiftStageSel5Dto4_uid157_normalizationShifter_uid40_fpAccTest_merged_bit_select(BITSELECT,188)@2
    leftShiftStageSel5Dto4_uid157_normalizationShifter_uid40_fpAccTest_merged_bit_select_b <= r_uid101_zeroCounter_uid37_fpAccTest_q(5 downto 4);
    leftShiftStageSel5Dto4_uid157_normalizationShifter_uid40_fpAccTest_merged_bit_select_c <= r_uid101_zeroCounter_uid37_fpAccTest_q(3 downto 2);
    leftShiftStageSel5Dto4_uid157_normalizationShifter_uid40_fpAccTest_merged_bit_select_d <= r_uid101_zeroCounter_uid37_fpAccTest_q(1 downto 0);

    -- leftShiftStage2_uid180_normalizationShifter_uid40_fpAccTest(MUX,179)@2
    leftShiftStage2_uid180_normalizationShifter_uid40_fpAccTest_s <= leftShiftStageSel5Dto4_uid157_normalizationShifter_uid40_fpAccTest_merged_bit_select_d;
    leftShiftStage2_uid180_normalizationShifter_uid40_fpAccTest_combproc: PROCESS (leftShiftStage2_uid180_normalizationShifter_uid40_fpAccTest_s, leftShiftStage1_uid169_normalizationShifter_uid40_fpAccTest_q, leftShiftStage2Idx1_uid172_normalizationShifter_uid40_fpAccTest_q, leftShiftStage2Idx2_uid175_normalizationShifter_uid40_fpAccTest_q, leftShiftStage2Idx3_uid178_normalizationShifter_uid40_fpAccTest_q)
    BEGIN
        CASE (leftShiftStage2_uid180_normalizationShifter_uid40_fpAccTest_s) IS
            WHEN "00" => leftShiftStage2_uid180_normalizationShifter_uid40_fpAccTest_q <= leftShiftStage1_uid169_normalizationShifter_uid40_fpAccTest_q;
            WHEN "01" => leftShiftStage2_uid180_normalizationShifter_uid40_fpAccTest_q <= leftShiftStage2Idx1_uid172_normalizationShifter_uid40_fpAccTest_q;
            WHEN "10" => leftShiftStage2_uid180_normalizationShifter_uid40_fpAccTest_q <= leftShiftStage2Idx2_uid175_normalizationShifter_uid40_fpAccTest_q;
            WHEN "11" => leftShiftStage2_uid180_normalizationShifter_uid40_fpAccTest_q <= leftShiftStage2Idx3_uid178_normalizationShifter_uid40_fpAccTest_q;
            WHEN OTHERS => leftShiftStage2_uid180_normalizationShifter_uid40_fpAccTest_q <= (others => '0');
        END CASE;
    END PROCESS;

    -- fracR_uid46_fpAccTest(BITSELECT,45)@2
    fracR_uid46_fpAccTest_in <= leftShiftStage2_uid180_normalizationShifter_uid40_fpAccTest_q(54 downto 0);
    fracR_uid46_fpAccTest_b <= fracR_uid46_fpAccTest_in(54 downto 32);

    -- redist3_fracR_uid46_fpAccTest_b_1(DELAY,192)
    redist3_fracR_uid46_fpAccTest_b_1 : dspba_delay
    GENERIC MAP ( width => 23, depth => 1, reset_kind => "ASYNC" )
    PORT MAP ( xin => fracR_uid46_fpAccTest_b, xout => redist3_fracR_uid46_fpAccTest_b_1_q, clk => clk, aclr => areset );

    -- R_uid47_fpAccTest(BITJOIN,46)@3
    R_uid47_fpAccTest_q <= redist4_accumulatorSign_uid29_fpAccTest_b_2_q & resExpSub_uid43_fpAccTest_finalExpUpdated_uid45_fpAccTest_merged_q & redist3_fracR_uid46_fpAccTest_b_1_q;

    -- xOut(GPOUT,4)@3
    r <= R_uid47_fpAccTest_q;
    xo <= delayedXOverflowFeedbackSignal_uid50_fpAccTest_q;
    xu <= redist1_oRXUnderflowFlagFeedback_uid58_fpAccTest_q_3_q;
    ao <= delayedAccOverflowFeedbackSignal_uid60_fpAccTest_q;

END normal;
