pocper/SoC-GPS-Hybrid-Acquisition/rtl/ip/FP_complex_mult/FP_complex_mult/FP_complex_mult_0002.vhd

-- ------------------------------------------------------------------------- 
-- High Level Design Compiler for Intel(R) FPGAs Version 25.1std (Release Build #1129)
-- Quartus Prime development tool and MATLAB/Simulink Interface
-- 
-- Legal Notice: Copyright 2025 Intel Corporation.  All rights reserved.
-- Your use of  Intel Corporation's design tools,  logic functions and other
-- software and  tools, and its AMPP partner logic functions, and any output
-- files any  of the foregoing (including  device programming  or simulation
-- files), and  any associated  documentation  or information  are expressly
-- subject  to the terms and  conditions of the  Intel FPGA Software License
-- Agreement, Intel MegaCore Function License Agreement, or other applicable
-- license agreement,  including,  without limitation,  that your use is for
-- the  sole  purpose of  programming  logic devices  manufactured by  Intel
-- and  sold by Intel  or its authorized  distributors. Please refer  to the
-- applicable agreement for further details.
-- ---------------------------------------------------------------------------

-- VHDL created from FP_complex_mult_0002
-- VHDL created on Sat Feb 21 22:27:09 2026


library IEEE;
use IEEE.std_logic_1164.all;
use IEEE.NUMERIC_STD.all;
use IEEE.MATH_REAL.all;
use std.TextIO.all;
use work.dspba_library_package.all;

LIBRARY altera_mf;
USE altera_mf.altera_mf_components.all;
LIBRARY altera_lnsim;
USE altera_lnsim.altera_lnsim_components.altera_syncram;
LIBRARY lpm;
USE lpm.lpm_components.all;

entity FP_complex_mult_0002 is
    port (
        a : in std_logic_vector(31 downto 0);  -- float32_m23
        b : in std_logic_vector(31 downto 0);  -- float32_m23
        c : in std_logic_vector(31 downto 0);  -- float32_m23
        d : in std_logic_vector(31 downto 0);  -- float32_m23
        q : out std_logic_vector(31 downto 0);  -- float32_m23
        r : out std_logic_vector(31 downto 0);  -- float32_m23
        clk : in std_logic;
        areset : in std_logic
    );
end FP_complex_mult_0002;

architecture normal of FP_complex_mult_0002 is

    attribute altera_attribute : string;
    attribute altera_attribute of normal : architecture is "-name AUTO_SHIFT_REGISTER_RECOGNITION OFF; -name PHYSICAL_SYNTHESIS_REGISTER_DUPLICATION ON; -name MESSAGE_DISABLE 10036; -name MESSAGE_DISABLE 10037; -name MESSAGE_DISABLE 14130; -name MESSAGE_DISABLE 14320; -name MESSAGE_DISABLE 15400; -name MESSAGE_DISABLE 14130; -name MESSAGE_DISABLE 10036; -name MESSAGE_DISABLE 12020; -name MESSAGE_DISABLE 12030; -name MESSAGE_DISABLE 12010; -name MESSAGE_DISABLE 12110; -name MESSAGE_DISABLE 14320; -name MESSAGE_DISABLE 13410; -name MESSAGE_DISABLE 113007";
    
    signal GND_q : STD_LOGIC_VECTOR (0 downto 0);
    signal VCC_q : STD_LOGIC_VECTOR (0 downto 0);
    signal ySign_uid10_fpComplexMulTest_b : STD_LOGIC_VECTOR (0 downto 0);
    signal excBits_uid11_fpComplexMulTest_b : STD_LOGIC_VECTOR (1 downto 0);
    signal fraction_uid12_fpComplexMulTest_b : STD_LOGIC_VECTOR (22 downto 0);
    signal exp_uid13_fpComplexMulTest_b : STD_LOGIC_VECTOR (7 downto 0);
    signal invYSign_uid14_fpComplexMulTest_q : STD_LOGIC_VECTOR (0 downto 0);
    signal minusY_uid15_fpComplexMulTest_q : STD_LOGIC_VECTOR (33 downto 0);
    signal expX_uid20_ac_uid6_fpComplexMulTest_b : STD_LOGIC_VECTOR (7 downto 0);
    signal expY_uid21_ac_uid6_fpComplexMulTest_b : STD_LOGIC_VECTOR (7 downto 0);
    signal signX_uid22_ac_uid6_fpComplexMulTest_b : STD_LOGIC_VECTOR (0 downto 0);
    signal signY_uid23_ac_uid6_fpComplexMulTest_b : STD_LOGIC_VECTOR (0 downto 0);
    signal cstAllOWE_uid24_ac_uid6_fpComplexMulTest_q : STD_LOGIC_VECTOR (7 downto 0);
    signal cstZeroWF_uid25_ac_uid6_fpComplexMulTest_q : STD_LOGIC_VECTOR (22 downto 0);
    signal cstAllZWE_uid26_ac_uid6_fpComplexMulTest_q : STD_LOGIC_VECTOR (7 downto 0);
    signal frac_x_uid28_ac_uid6_fpComplexMulTest_b : STD_LOGIC_VECTOR (22 downto 0);
    signal excZ_x_uid29_ac_uid6_fpComplexMulTest_q : STD_LOGIC_VECTOR (0 downto 0);
    signal expXIsMax_uid30_ac_uid6_fpComplexMulTest_q : STD_LOGIC_VECTOR (0 downto 0);
    signal fracXIsZero_uid31_ac_uid6_fpComplexMulTest_qi : STD_LOGIC_VECTOR (0 downto 0);
    signal fracXIsZero_uid31_ac_uid6_fpComplexMulTest_q : STD_LOGIC_VECTOR (0 downto 0);
    signal fracXIsNotZero_uid32_ac_uid6_fpComplexMulTest_q : STD_LOGIC_VECTOR (0 downto 0);
    signal excI_x_uid33_ac_uid6_fpComplexMulTest_q : STD_LOGIC_VECTOR (0 downto 0);
    signal excN_x_uid34_ac_uid6_fpComplexMulTest_q : STD_LOGIC_VECTOR (0 downto 0);
    signal invExpXIsMax_uid35_ac_uid6_fpComplexMulTest_q : STD_LOGIC_VECTOR (0 downto 0);
    signal InvExpXIsZero_uid36_ac_uid6_fpComplexMulTest_q : STD_LOGIC_VECTOR (0 downto 0);
    signal excR_x_uid37_ac_uid6_fpComplexMulTest_q : STD_LOGIC_VECTOR (0 downto 0);
    signal frac_y_uid42_ac_uid6_fpComplexMulTest_b : STD_LOGIC_VECTOR (22 downto 0);
    signal excZ_y_uid43_ac_uid6_fpComplexMulTest_q : STD_LOGIC_VECTOR (0 downto 0);
    signal expXIsMax_uid44_ac_uid6_fpComplexMulTest_q : STD_LOGIC_VECTOR (0 downto 0);
    signal fracXIsZero_uid45_ac_uid6_fpComplexMulTest_qi : STD_LOGIC_VECTOR (0 downto 0);
    signal fracXIsZero_uid45_ac_uid6_fpComplexMulTest_q : STD_LOGIC_VECTOR (0 downto 0);
    signal fracXIsNotZero_uid46_ac_uid6_fpComplexMulTest_q : STD_LOGIC_VECTOR (0 downto 0);
    signal excI_y_uid47_ac_uid6_fpComplexMulTest_q : STD_LOGIC_VECTOR (0 downto 0);
    signal excN_y_uid48_ac_uid6_fpComplexMulTest_q : STD_LOGIC_VECTOR (0 downto 0);
    signal invExpXIsMax_uid49_ac_uid6_fpComplexMulTest_q : STD_LOGIC_VECTOR (0 downto 0);
    signal InvExpXIsZero_uid50_ac_uid6_fpComplexMulTest_q : STD_LOGIC_VECTOR (0 downto 0);
    signal excR_y_uid51_ac_uid6_fpComplexMulTest_q : STD_LOGIC_VECTOR (0 downto 0);
    signal ofracX_uid54_ac_uid6_fpComplexMulTest_q : STD_LOGIC_VECTOR (23 downto 0);
    signal ofracY_uid57_ac_uid6_fpComplexMulTest_q : STD_LOGIC_VECTOR (23 downto 0);
    signal expSum_uid58_ac_uid6_fpComplexMulTest_a : STD_LOGIC_VECTOR (8 downto 0);
    signal expSum_uid58_ac_uid6_fpComplexMulTest_b : STD_LOGIC_VECTOR (8 downto 0);
    signal expSum_uid58_ac_uid6_fpComplexMulTest_o : STD_LOGIC_VECTOR (8 downto 0);
    signal expSum_uid58_ac_uid6_fpComplexMulTest_q : STD_LOGIC_VECTOR (8 downto 0);
    signal biasInc_uid59_ac_uid6_fpComplexMulTest_q : STD_LOGIC_VECTOR (9 downto 0);
    signal expSumMBias_uid60_ac_uid6_fpComplexMulTest_a : STD_LOGIC_VECTOR (11 downto 0);
    signal expSumMBias_uid60_ac_uid6_fpComplexMulTest_b : STD_LOGIC_VECTOR (11 downto 0);
    signal expSumMBias_uid60_ac_uid6_fpComplexMulTest_o : STD_LOGIC_VECTOR (11 downto 0);
    signal expSumMBias_uid60_ac_uid6_fpComplexMulTest_q : STD_LOGIC_VECTOR (10 downto 0);
    signal signR_uid62_ac_uid6_fpComplexMulTest_q : STD_LOGIC_VECTOR (0 downto 0);
    signal normalizeBit_uid63_ac_uid6_fpComplexMulTest_b : STD_LOGIC_VECTOR (0 downto 0);
    signal fracRPostNormHigh_uid65_ac_uid6_fpComplexMulTest_in : STD_LOGIC_VECTOR (46 downto 0);
    signal fracRPostNormHigh_uid65_ac_uid6_fpComplexMulTest_b : STD_LOGIC_VECTOR (23 downto 0);
    signal fracRPostNormLow_uid66_ac_uid6_fpComplexMulTest_in : STD_LOGIC_VECTOR (45 downto 0);
    signal fracRPostNormLow_uid66_ac_uid6_fpComplexMulTest_b : STD_LOGIC_VECTOR (23 downto 0);
    signal fracRPostNorm_uid67_ac_uid6_fpComplexMulTest_s : STD_LOGIC_VECTOR (0 downto 0);
    signal fracRPostNorm_uid67_ac_uid6_fpComplexMulTest_q : STD_LOGIC_VECTOR (23 downto 0);
    signal stickyRange_uid68_ac_uid6_fpComplexMulTest_in : STD_LOGIC_VECTOR (21 downto 0);
    signal stickyRange_uid68_ac_uid6_fpComplexMulTest_b : STD_LOGIC_VECTOR (21 downto 0);
    signal extraStickyBitOfProd_uid69_ac_uid6_fpComplexMulTest_in : STD_LOGIC_VECTOR (22 downto 0);
    signal extraStickyBitOfProd_uid69_ac_uid6_fpComplexMulTest_b : STD_LOGIC_VECTOR (0 downto 0);
    signal extraStickyBit_uid70_ac_uid6_fpComplexMulTest_s : STD_LOGIC_VECTOR (0 downto 0);
    signal extraStickyBit_uid70_ac_uid6_fpComplexMulTest_q : STD_LOGIC_VECTOR (0 downto 0);
    signal stickyExtendedRange_uid71_ac_uid6_fpComplexMulTest_q : STD_LOGIC_VECTOR (22 downto 0);
    signal stickyRangeComparator_uid73_ac_uid6_fpComplexMulTest_q : STD_LOGIC_VECTOR (0 downto 0);
    signal sticky_uid74_ac_uid6_fpComplexMulTest_q : STD_LOGIC_VECTOR (0 downto 0);
    signal fracRPostNorm1dto0_uid75_ac_uid6_fpComplexMulTest_in : STD_LOGIC_VECTOR (1 downto 0);
    signal fracRPostNorm1dto0_uid75_ac_uid6_fpComplexMulTest_b : STD_LOGIC_VECTOR (1 downto 0);
    signal lrs_uid76_ac_uid6_fpComplexMulTest_q : STD_LOGIC_VECTOR (2 downto 0);
    signal roundBitDetectionConstant_uid77_ac_uid6_fpComplexMulTest_q : STD_LOGIC_VECTOR (2 downto 0);
    signal roundBitDetectionPattern_uid78_ac_uid6_fpComplexMulTest_q : STD_LOGIC_VECTOR (0 downto 0);
    signal roundBit_uid79_ac_uid6_fpComplexMulTest_q : STD_LOGIC_VECTOR (0 downto 0);
    signal expFracPreRound_uid80_ac_uid6_fpComplexMulTest_q : STD_LOGIC_VECTOR (34 downto 0);
    signal roundBitAndNormalizationOp_uid82_ac_uid6_fpComplexMulTest_q : STD_LOGIC_VECTOR (25 downto 0);
    signal expFracRPostRounding_uid83_ac_uid6_fpComplexMulTest_a : STD_LOGIC_VECTOR (36 downto 0);
    signal expFracRPostRounding_uid83_ac_uid6_fpComplexMulTest_b : STD_LOGIC_VECTOR (36 downto 0);
    signal expFracRPostRounding_uid83_ac_uid6_fpComplexMulTest_o : STD_LOGIC_VECTOR (36 downto 0);
    signal expFracRPostRounding_uid83_ac_uid6_fpComplexMulTest_q : STD_LOGIC_VECTOR (35 downto 0);
    signal fracRPreExc_uid84_ac_uid6_fpComplexMulTest_in : STD_LOGIC_VECTOR (23 downto 0);
    signal fracRPreExc_uid84_ac_uid6_fpComplexMulTest_b : STD_LOGIC_VECTOR (22 downto 0);
    signal expRPreExcExt_uid85_ac_uid6_fpComplexMulTest_b : STD_LOGIC_VECTOR (11 downto 0);
    signal expRPreExc_uid86_ac_uid6_fpComplexMulTest_in : STD_LOGIC_VECTOR (7 downto 0);
    signal expRPreExc_uid86_ac_uid6_fpComplexMulTest_b : STD_LOGIC_VECTOR (7 downto 0);
    signal expOvf_uid89_ac_uid6_fpComplexMulTest_a : STD_LOGIC_VECTOR (13 downto 0);
    signal expOvf_uid89_ac_uid6_fpComplexMulTest_b : STD_LOGIC_VECTOR (13 downto 0);
    signal expOvf_uid89_ac_uid6_fpComplexMulTest_o : STD_LOGIC_VECTOR (13 downto 0);
    signal expOvf_uid89_ac_uid6_fpComplexMulTest_c : STD_LOGIC_VECTOR (0 downto 0);
    signal excXZAndExcYZ_uid90_ac_uid6_fpComplexMulTest_q : STD_LOGIC_VECTOR (0 downto 0);
    signal excXZAndExcYR_uid91_ac_uid6_fpComplexMulTest_q : STD_LOGIC_VECTOR (0 downto 0);
    signal excYZAndExcXR_uid92_ac_uid6_fpComplexMulTest_q : STD_LOGIC_VECTOR (0 downto 0);
    signal excZC3_uid93_ac_uid6_fpComplexMulTest_q : STD_LOGIC_VECTOR (0 downto 0);
    signal excRZero_uid94_ac_uid6_fpComplexMulTest_q : STD_LOGIC_VECTOR (0 downto 0);
    signal excXIAndExcYI_uid95_ac_uid6_fpComplexMulTest_q : STD_LOGIC_VECTOR (0 downto 0);
    signal excXRAndExcYI_uid96_ac_uid6_fpComplexMulTest_q : STD_LOGIC_VECTOR (0 downto 0);
    signal excYRAndExcXI_uid97_ac_uid6_fpComplexMulTest_q : STD_LOGIC_VECTOR (0 downto 0);
    signal ExcROvfAndInReg_uid98_ac_uid6_fpComplexMulTest_q : STD_LOGIC_VECTOR (0 downto 0);
    signal excRInf_uid99_ac_uid6_fpComplexMulTest_q : STD_LOGIC_VECTOR (0 downto 0);
    signal excYZAndExcXI_uid100_ac_uid6_fpComplexMulTest_q : STD_LOGIC_VECTOR (0 downto 0);
    signal excXZAndExcYI_uid101_ac_uid6_fpComplexMulTest_q : STD_LOGIC_VECTOR (0 downto 0);
    signal ZeroTimesInf_uid102_ac_uid6_fpComplexMulTest_q : STD_LOGIC_VECTOR (0 downto 0);
    signal excRNaN_uid103_ac_uid6_fpComplexMulTest_q : STD_LOGIC_VECTOR (0 downto 0);
    signal concExc_uid104_ac_uid6_fpComplexMulTest_q : STD_LOGIC_VECTOR (2 downto 0);
    signal excREnc_uid105_ac_uid6_fpComplexMulTest_q : STD_LOGIC_VECTOR (1 downto 0);
    signal invExcRNaN_uid106_ac_uid6_fpComplexMulTest_q : STD_LOGIC_VECTOR (0 downto 0);
    signal signRPostExc_uid107_ac_uid6_fpComplexMulTest_qi : STD_LOGIC_VECTOR (0 downto 0);
    signal signRPostExc_uid107_ac_uid6_fpComplexMulTest_q : STD_LOGIC_VECTOR (0 downto 0);
    signal R_uid108_ac_uid6_fpComplexMulTest_q : STD_LOGIC_VECTOR (33 downto 0);
    signal expX_uid110_bd_uid7_fpComplexMulTest_b : STD_LOGIC_VECTOR (7 downto 0);
    signal expY_uid111_bd_uid7_fpComplexMulTest_b : STD_LOGIC_VECTOR (7 downto 0);
    signal signX_uid112_bd_uid7_fpComplexMulTest_b : STD_LOGIC_VECTOR (0 downto 0);
    signal signY_uid113_bd_uid7_fpComplexMulTest_b : STD_LOGIC_VECTOR (0 downto 0);
    signal frac_x_uid118_bd_uid7_fpComplexMulTest_b : STD_LOGIC_VECTOR (22 downto 0);
    signal excZ_x_uid119_bd_uid7_fpComplexMulTest_q : STD_LOGIC_VECTOR (0 downto 0);
    signal expXIsMax_uid120_bd_uid7_fpComplexMulTest_q : STD_LOGIC_VECTOR (0 downto 0);
    signal fracXIsZero_uid121_bd_uid7_fpComplexMulTest_qi : STD_LOGIC_VECTOR (0 downto 0);
    signal fracXIsZero_uid121_bd_uid7_fpComplexMulTest_q : STD_LOGIC_VECTOR (0 downto 0);
    signal fracXIsNotZero_uid122_bd_uid7_fpComplexMulTest_q : STD_LOGIC_VECTOR (0 downto 0);
    signal excI_x_uid123_bd_uid7_fpComplexMulTest_q : STD_LOGIC_VECTOR (0 downto 0);
    signal excN_x_uid124_bd_uid7_fpComplexMulTest_q : STD_LOGIC_VECTOR (0 downto 0);
    signal invExpXIsMax_uid125_bd_uid7_fpComplexMulTest_q : STD_LOGIC_VECTOR (0 downto 0);
    signal InvExpXIsZero_uid126_bd_uid7_fpComplexMulTest_q : STD_LOGIC_VECTOR (0 downto 0);
    signal excR_x_uid127_bd_uid7_fpComplexMulTest_q : STD_LOGIC_VECTOR (0 downto 0);
    signal frac_y_uid132_bd_uid7_fpComplexMulTest_b : STD_LOGIC_VECTOR (22 downto 0);
    signal excZ_y_uid133_bd_uid7_fpComplexMulTest_q : STD_LOGIC_VECTOR (0 downto 0);
    signal expXIsMax_uid134_bd_uid7_fpComplexMulTest_q : STD_LOGIC_VECTOR (0 downto 0);
    signal fracXIsZero_uid135_bd_uid7_fpComplexMulTest_qi : STD_LOGIC_VECTOR (0 downto 0);
    signal fracXIsZero_uid135_bd_uid7_fpComplexMulTest_q : STD_LOGIC_VECTOR (0 downto 0);
    signal fracXIsNotZero_uid136_bd_uid7_fpComplexMulTest_q : STD_LOGIC_VECTOR (0 downto 0);
    signal excI_y_uid137_bd_uid7_fpComplexMulTest_q : STD_LOGIC_VECTOR (0 downto 0);
    signal excN_y_uid138_bd_uid7_fpComplexMulTest_q : STD_LOGIC_VECTOR (0 downto 0);
    signal invExpXIsMax_uid139_bd_uid7_fpComplexMulTest_q : STD_LOGIC_VECTOR (0 downto 0);
    signal InvExpXIsZero_uid140_bd_uid7_fpComplexMulTest_q : STD_LOGIC_VECTOR (0 downto 0);
    signal excR_y_uid141_bd_uid7_fpComplexMulTest_q : STD_LOGIC_VECTOR (0 downto 0);
    signal ofracX_uid144_bd_uid7_fpComplexMulTest_q : STD_LOGIC_VECTOR (23 downto 0);
    signal ofracY_uid147_bd_uid7_fpComplexMulTest_q : STD_LOGIC_VECTOR (23 downto 0);
    signal expSum_uid148_bd_uid7_fpComplexMulTest_a : STD_LOGIC_VECTOR (8 downto 0);
    signal expSum_uid148_bd_uid7_fpComplexMulTest_b : STD_LOGIC_VECTOR (8 downto 0);
    signal expSum_uid148_bd_uid7_fpComplexMulTest_o : STD_LOGIC_VECTOR (8 downto 0);
    signal expSum_uid148_bd_uid7_fpComplexMulTest_q : STD_LOGIC_VECTOR (8 downto 0);
    signal expSumMBias_uid150_bd_uid7_fpComplexMulTest_a : STD_LOGIC_VECTOR (11 downto 0);
    signal expSumMBias_uid150_bd_uid7_fpComplexMulTest_b : STD_LOGIC_VECTOR (11 downto 0);
    signal expSumMBias_uid150_bd_uid7_fpComplexMulTest_o : STD_LOGIC_VECTOR (11 downto 0);
    signal expSumMBias_uid150_bd_uid7_fpComplexMulTest_q : STD_LOGIC_VECTOR (10 downto 0);
    signal signR_uid152_bd_uid7_fpComplexMulTest_q : STD_LOGIC_VECTOR (0 downto 0);
    signal normalizeBit_uid153_bd_uid7_fpComplexMulTest_b : STD_LOGIC_VECTOR (0 downto 0);
    signal fracRPostNormHigh_uid155_bd_uid7_fpComplexMulTest_in : STD_LOGIC_VECTOR (46 downto 0);
    signal fracRPostNormHigh_uid155_bd_uid7_fpComplexMulTest_b : STD_LOGIC_VECTOR (23 downto 0);
    signal fracRPostNormLow_uid156_bd_uid7_fpComplexMulTest_in : STD_LOGIC_VECTOR (45 downto 0);
    signal fracRPostNormLow_uid156_bd_uid7_fpComplexMulTest_b : STD_LOGIC_VECTOR (23 downto 0);
    signal fracRPostNorm_uid157_bd_uid7_fpComplexMulTest_s : STD_LOGIC_VECTOR (0 downto 0);
    signal fracRPostNorm_uid157_bd_uid7_fpComplexMulTest_q : STD_LOGIC_VECTOR (23 downto 0);
    signal stickyRange_uid158_bd_uid7_fpComplexMulTest_in : STD_LOGIC_VECTOR (21 downto 0);
    signal stickyRange_uid158_bd_uid7_fpComplexMulTest_b : STD_LOGIC_VECTOR (21 downto 0);
    signal extraStickyBitOfProd_uid159_bd_uid7_fpComplexMulTest_in : STD_LOGIC_VECTOR (22 downto 0);
    signal extraStickyBitOfProd_uid159_bd_uid7_fpComplexMulTest_b : STD_LOGIC_VECTOR (0 downto 0);
    signal extraStickyBit_uid160_bd_uid7_fpComplexMulTest_s : STD_LOGIC_VECTOR (0 downto 0);
    signal extraStickyBit_uid160_bd_uid7_fpComplexMulTest_q : STD_LOGIC_VECTOR (0 downto 0);
    signal stickyExtendedRange_uid161_bd_uid7_fpComplexMulTest_q : STD_LOGIC_VECTOR (22 downto 0);
    signal stickyRangeComparator_uid163_bd_uid7_fpComplexMulTest_q : STD_LOGIC_VECTOR (0 downto 0);
    signal sticky_uid164_bd_uid7_fpComplexMulTest_q : STD_LOGIC_VECTOR (0 downto 0);
    signal fracRPostNorm1dto0_uid165_bd_uid7_fpComplexMulTest_in : STD_LOGIC_VECTOR (1 downto 0);
    signal fracRPostNorm1dto0_uid165_bd_uid7_fpComplexMulTest_b : STD_LOGIC_VECTOR (1 downto 0);
    signal lrs_uid166_bd_uid7_fpComplexMulTest_q : STD_LOGIC_VECTOR (2 downto 0);
    signal roundBitDetectionPattern_uid168_bd_uid7_fpComplexMulTest_q : STD_LOGIC_VECTOR (0 downto 0);
    signal roundBit_uid169_bd_uid7_fpComplexMulTest_q : STD_LOGIC_VECTOR (0 downto 0);
    signal expFracPreRound_uid170_bd_uid7_fpComplexMulTest_q : STD_LOGIC_VECTOR (34 downto 0);
    signal roundBitAndNormalizationOp_uid172_bd_uid7_fpComplexMulTest_q : STD_LOGIC_VECTOR (25 downto 0);
    signal expFracRPostRounding_uid173_bd_uid7_fpComplexMulTest_a : STD_LOGIC_VECTOR (36 downto 0);
    signal expFracRPostRounding_uid173_bd_uid7_fpComplexMulTest_b : STD_LOGIC_VECTOR (36 downto 0);
    signal expFracRPostRounding_uid173_bd_uid7_fpComplexMulTest_o : STD_LOGIC_VECTOR (36 downto 0);
    signal expFracRPostRounding_uid173_bd_uid7_fpComplexMulTest_q : STD_LOGIC_VECTOR (35 downto 0);
    signal fracRPreExc_uid174_bd_uid7_fpComplexMulTest_in : STD_LOGIC_VECTOR (23 downto 0);
    signal fracRPreExc_uid174_bd_uid7_fpComplexMulTest_b : STD_LOGIC_VECTOR (22 downto 0);
    signal expRPreExcExt_uid175_bd_uid7_fpComplexMulTest_b : STD_LOGIC_VECTOR (11 downto 0);
    signal expRPreExc_uid176_bd_uid7_fpComplexMulTest_in : STD_LOGIC_VECTOR (7 downto 0);
    signal expRPreExc_uid176_bd_uid7_fpComplexMulTest_b : STD_LOGIC_VECTOR (7 downto 0);
    signal expOvf_uid179_bd_uid7_fpComplexMulTest_a : STD_LOGIC_VECTOR (13 downto 0);
    signal expOvf_uid179_bd_uid7_fpComplexMulTest_b : STD_LOGIC_VECTOR (13 downto 0);
    signal expOvf_uid179_bd_uid7_fpComplexMulTest_o : STD_LOGIC_VECTOR (13 downto 0);
    signal expOvf_uid179_bd_uid7_fpComplexMulTest_c : STD_LOGIC_VECTOR (0 downto 0);
    signal excXZAndExcYZ_uid180_bd_uid7_fpComplexMulTest_q : STD_LOGIC_VECTOR (0 downto 0);
    signal excXZAndExcYR_uid181_bd_uid7_fpComplexMulTest_q : STD_LOGIC_VECTOR (0 downto 0);
    signal excYZAndExcXR_uid182_bd_uid7_fpComplexMulTest_q : STD_LOGIC_VECTOR (0 downto 0);
    signal excZC3_uid183_bd_uid7_fpComplexMulTest_q : STD_LOGIC_VECTOR (0 downto 0);
    signal excRZero_uid184_bd_uid7_fpComplexMulTest_q : STD_LOGIC_VECTOR (0 downto 0);
    signal excXIAndExcYI_uid185_bd_uid7_fpComplexMulTest_q : STD_LOGIC_VECTOR (0 downto 0);
    signal excXRAndExcYI_uid186_bd_uid7_fpComplexMulTest_q : STD_LOGIC_VECTOR (0 downto 0);
    signal excYRAndExcXI_uid187_bd_uid7_fpComplexMulTest_q : STD_LOGIC_VECTOR (0 downto 0);
    signal ExcROvfAndInReg_uid188_bd_uid7_fpComplexMulTest_q : STD_LOGIC_VECTOR (0 downto 0);
    signal excRInf_uid189_bd_uid7_fpComplexMulTest_q : STD_LOGIC_VECTOR (0 downto 0);
    signal excYZAndExcXI_uid190_bd_uid7_fpComplexMulTest_q : STD_LOGIC_VECTOR (0 downto 0);
    signal excXZAndExcYI_uid191_bd_uid7_fpComplexMulTest_q : STD_LOGIC_VECTOR (0 downto 0);
    signal ZeroTimesInf_uid192_bd_uid7_fpComplexMulTest_q : STD_LOGIC_VECTOR (0 downto 0);
    signal excRNaN_uid193_bd_uid7_fpComplexMulTest_q : STD_LOGIC_VECTOR (0 downto 0);
    signal concExc_uid194_bd_uid7_fpComplexMulTest_q : STD_LOGIC_VECTOR (2 downto 0);
    signal excREnc_uid195_bd_uid7_fpComplexMulTest_q : STD_LOGIC_VECTOR (1 downto 0);
    signal invExcRNaN_uid196_bd_uid7_fpComplexMulTest_q : STD_LOGIC_VECTOR (0 downto 0);
    signal signRPostExc_uid197_bd_uid7_fpComplexMulTest_q : STD_LOGIC_VECTOR (0 downto 0);
    signal R_uid198_bd_uid7_fpComplexMulTest_q : STD_LOGIC_VECTOR (33 downto 0);
    signal expSum_uid238_ad_uid8_fpComplexMulTest_a : STD_LOGIC_VECTOR (8 downto 0);
    signal expSum_uid238_ad_uid8_fpComplexMulTest_b : STD_LOGIC_VECTOR (8 downto 0);
    signal expSum_uid238_ad_uid8_fpComplexMulTest_o : STD_LOGIC_VECTOR (8 downto 0);
    signal expSum_uid238_ad_uid8_fpComplexMulTest_q : STD_LOGIC_VECTOR (8 downto 0);
    signal expSumMBias_uid240_ad_uid8_fpComplexMulTest_a : STD_LOGIC_VECTOR (11 downto 0);
    signal expSumMBias_uid240_ad_uid8_fpComplexMulTest_b : STD_LOGIC_VECTOR (11 downto 0);
    signal expSumMBias_uid240_ad_uid8_fpComplexMulTest_o : STD_LOGIC_VECTOR (11 downto 0);
    signal expSumMBias_uid240_ad_uid8_fpComplexMulTest_q : STD_LOGIC_VECTOR (10 downto 0);
    signal signR_uid242_ad_uid8_fpComplexMulTest_q : STD_LOGIC_VECTOR (0 downto 0);
    signal normalizeBit_uid243_ad_uid8_fpComplexMulTest_b : STD_LOGIC_VECTOR (0 downto 0);
    signal fracRPostNormHigh_uid245_ad_uid8_fpComplexMulTest_in : STD_LOGIC_VECTOR (46 downto 0);
    signal fracRPostNormHigh_uid245_ad_uid8_fpComplexMulTest_b : STD_LOGIC_VECTOR (23 downto 0);
    signal fracRPostNormLow_uid246_ad_uid8_fpComplexMulTest_in : STD_LOGIC_VECTOR (45 downto 0);
    signal fracRPostNormLow_uid246_ad_uid8_fpComplexMulTest_b : STD_LOGIC_VECTOR (23 downto 0);
    signal fracRPostNorm_uid247_ad_uid8_fpComplexMulTest_s : STD_LOGIC_VECTOR (0 downto 0);
    signal fracRPostNorm_uid247_ad_uid8_fpComplexMulTest_q : STD_LOGIC_VECTOR (23 downto 0);
    signal stickyRange_uid248_ad_uid8_fpComplexMulTest_in : STD_LOGIC_VECTOR (21 downto 0);
    signal stickyRange_uid248_ad_uid8_fpComplexMulTest_b : STD_LOGIC_VECTOR (21 downto 0);
    signal extraStickyBitOfProd_uid249_ad_uid8_fpComplexMulTest_in : STD_LOGIC_VECTOR (22 downto 0);
    signal extraStickyBitOfProd_uid249_ad_uid8_fpComplexMulTest_b : STD_LOGIC_VECTOR (0 downto 0);
    signal extraStickyBit_uid250_ad_uid8_fpComplexMulTest_s : STD_LOGIC_VECTOR (0 downto 0);
    signal extraStickyBit_uid250_ad_uid8_fpComplexMulTest_q : STD_LOGIC_VECTOR (0 downto 0);
    signal stickyExtendedRange_uid251_ad_uid8_fpComplexMulTest_q : STD_LOGIC_VECTOR (22 downto 0);
    signal stickyRangeComparator_uid253_ad_uid8_fpComplexMulTest_q : STD_LOGIC_VECTOR (0 downto 0);
    signal sticky_uid254_ad_uid8_fpComplexMulTest_q : STD_LOGIC_VECTOR (0 downto 0);
    signal fracRPostNorm1dto0_uid255_ad_uid8_fpComplexMulTest_in : STD_LOGIC_VECTOR (1 downto 0);
    signal fracRPostNorm1dto0_uid255_ad_uid8_fpComplexMulTest_b : STD_LOGIC_VECTOR (1 downto 0);
    signal lrs_uid256_ad_uid8_fpComplexMulTest_q : STD_LOGIC_VECTOR (2 downto 0);
    signal roundBitDetectionPattern_uid258_ad_uid8_fpComplexMulTest_q : STD_LOGIC_VECTOR (0 downto 0);
    signal roundBit_uid259_ad_uid8_fpComplexMulTest_q : STD_LOGIC_VECTOR (0 downto 0);
    signal expFracPreRound_uid260_ad_uid8_fpComplexMulTest_q : STD_LOGIC_VECTOR (34 downto 0);
    signal roundBitAndNormalizationOp_uid262_ad_uid8_fpComplexMulTest_q : STD_LOGIC_VECTOR (25 downto 0);
    signal expFracRPostRounding_uid263_ad_uid8_fpComplexMulTest_a : STD_LOGIC_VECTOR (36 downto 0);
    signal expFracRPostRounding_uid263_ad_uid8_fpComplexMulTest_b : STD_LOGIC_VECTOR (36 downto 0);
    signal expFracRPostRounding_uid263_ad_uid8_fpComplexMulTest_o : STD_LOGIC_VECTOR (36 downto 0);
    signal expFracRPostRounding_uid263_ad_uid8_fpComplexMulTest_q : STD_LOGIC_VECTOR (35 downto 0);
    signal fracRPreExc_uid264_ad_uid8_fpComplexMulTest_in : STD_LOGIC_VECTOR (23 downto 0);
    signal fracRPreExc_uid264_ad_uid8_fpComplexMulTest_b : STD_LOGIC_VECTOR (22 downto 0);
    signal expRPreExcExt_uid265_ad_uid8_fpComplexMulTest_b : STD_LOGIC_VECTOR (11 downto 0);
    signal expRPreExc_uid266_ad_uid8_fpComplexMulTest_in : STD_LOGIC_VECTOR (7 downto 0);
    signal expRPreExc_uid266_ad_uid8_fpComplexMulTest_b : STD_LOGIC_VECTOR (7 downto 0);
    signal expOvf_uid269_ad_uid8_fpComplexMulTest_a : STD_LOGIC_VECTOR (13 downto 0);
    signal expOvf_uid269_ad_uid8_fpComplexMulTest_b : STD_LOGIC_VECTOR (13 downto 0);
    signal expOvf_uid269_ad_uid8_fpComplexMulTest_o : STD_LOGIC_VECTOR (13 downto 0);
    signal expOvf_uid269_ad_uid8_fpComplexMulTest_c : STD_LOGIC_VECTOR (0 downto 0);
    signal excXZAndExcYZ_uid270_ad_uid8_fpComplexMulTest_q : STD_LOGIC_VECTOR (0 downto 0);
    signal excXZAndExcYR_uid271_ad_uid8_fpComplexMulTest_q : STD_LOGIC_VECTOR (0 downto 0);
    signal excYZAndExcXR_uid272_ad_uid8_fpComplexMulTest_q : STD_LOGIC_VECTOR (0 downto 0);
    signal excZC3_uid273_ad_uid8_fpComplexMulTest_q : STD_LOGIC_VECTOR (0 downto 0);
    signal excRZero_uid274_ad_uid8_fpComplexMulTest_q : STD_LOGIC_VECTOR (0 downto 0);
    signal excXIAndExcYI_uid275_ad_uid8_fpComplexMulTest_q : STD_LOGIC_VECTOR (0 downto 0);
    signal excXRAndExcYI_uid276_ad_uid8_fpComplexMulTest_q : STD_LOGIC_VECTOR (0 downto 0);
    signal excYRAndExcXI_uid277_ad_uid8_fpComplexMulTest_q : STD_LOGIC_VECTOR (0 downto 0);
    signal ExcROvfAndInReg_uid278_ad_uid8_fpComplexMulTest_q : STD_LOGIC_VECTOR (0 downto 0);
    signal excRInf_uid279_ad_uid8_fpComplexMulTest_q : STD_LOGIC_VECTOR (0 downto 0);
    signal excYZAndExcXI_uid280_ad_uid8_fpComplexMulTest_q : STD_LOGIC_VECTOR (0 downto 0);
    signal excXZAndExcYI_uid281_ad_uid8_fpComplexMulTest_q : STD_LOGIC_VECTOR (0 downto 0);
    signal ZeroTimesInf_uid282_ad_uid8_fpComplexMulTest_q : STD_LOGIC_VECTOR (0 downto 0);
    signal excRNaN_uid283_ad_uid8_fpComplexMulTest_q : STD_LOGIC_VECTOR (0 downto 0);
    signal concExc_uid284_ad_uid8_fpComplexMulTest_q : STD_LOGIC_VECTOR (2 downto 0);
    signal excREnc_uid285_ad_uid8_fpComplexMulTest_q : STD_LOGIC_VECTOR (1 downto 0);
    signal invExcRNaN_uid286_ad_uid8_fpComplexMulTest_q : STD_LOGIC_VECTOR (0 downto 0);
    signal signRPostExc_uid287_ad_uid8_fpComplexMulTest_qi : STD_LOGIC_VECTOR (0 downto 0);
    signal signRPostExc_uid287_ad_uid8_fpComplexMulTest_q : STD_LOGIC_VECTOR (0 downto 0);
    signal R_uid288_ad_uid8_fpComplexMulTest_q : STD_LOGIC_VECTOR (33 downto 0);
    signal expSum_uid328_bc_uid9_fpComplexMulTest_a : STD_LOGIC_VECTOR (8 downto 0);
    signal expSum_uid328_bc_uid9_fpComplexMulTest_b : STD_LOGIC_VECTOR (8 downto 0);
    signal expSum_uid328_bc_uid9_fpComplexMulTest_o : STD_LOGIC_VECTOR (8 downto 0);
    signal expSum_uid328_bc_uid9_fpComplexMulTest_q : STD_LOGIC_VECTOR (8 downto 0);
    signal expSumMBias_uid330_bc_uid9_fpComplexMulTest_a : STD_LOGIC_VECTOR (11 downto 0);
    signal expSumMBias_uid330_bc_uid9_fpComplexMulTest_b : STD_LOGIC_VECTOR (11 downto 0);
    signal expSumMBias_uid330_bc_uid9_fpComplexMulTest_o : STD_LOGIC_VECTOR (11 downto 0);
    signal expSumMBias_uid330_bc_uid9_fpComplexMulTest_q : STD_LOGIC_VECTOR (10 downto 0);
    signal signR_uid332_bc_uid9_fpComplexMulTest_q : STD_LOGIC_VECTOR (0 downto 0);
    signal normalizeBit_uid333_bc_uid9_fpComplexMulTest_b : STD_LOGIC_VECTOR (0 downto 0);
    signal fracRPostNormHigh_uid335_bc_uid9_fpComplexMulTest_in : STD_LOGIC_VECTOR (46 downto 0);
    signal fracRPostNormHigh_uid335_bc_uid9_fpComplexMulTest_b : STD_LOGIC_VECTOR (23 downto 0);
    signal fracRPostNormLow_uid336_bc_uid9_fpComplexMulTest_in : STD_LOGIC_VECTOR (45 downto 0);
    signal fracRPostNormLow_uid336_bc_uid9_fpComplexMulTest_b : STD_LOGIC_VECTOR (23 downto 0);
    signal fracRPostNorm_uid337_bc_uid9_fpComplexMulTest_s : STD_LOGIC_VECTOR (0 downto 0);
    signal fracRPostNorm_uid337_bc_uid9_fpComplexMulTest_q : STD_LOGIC_VECTOR (23 downto 0);
    signal stickyRange_uid338_bc_uid9_fpComplexMulTest_in : STD_LOGIC_VECTOR (21 downto 0);
    signal stickyRange_uid338_bc_uid9_fpComplexMulTest_b : STD_LOGIC_VECTOR (21 downto 0);
    signal extraStickyBitOfProd_uid339_bc_uid9_fpComplexMulTest_in : STD_LOGIC_VECTOR (22 downto 0);
    signal extraStickyBitOfProd_uid339_bc_uid9_fpComplexMulTest_b : STD_LOGIC_VECTOR (0 downto 0);
    signal extraStickyBit_uid340_bc_uid9_fpComplexMulTest_s : STD_LOGIC_VECTOR (0 downto 0);
    signal extraStickyBit_uid340_bc_uid9_fpComplexMulTest_q : STD_LOGIC_VECTOR (0 downto 0);
    signal stickyExtendedRange_uid341_bc_uid9_fpComplexMulTest_q : STD_LOGIC_VECTOR (22 downto 0);
    signal stickyRangeComparator_uid343_bc_uid9_fpComplexMulTest_q : STD_LOGIC_VECTOR (0 downto 0);
    signal sticky_uid344_bc_uid9_fpComplexMulTest_q : STD_LOGIC_VECTOR (0 downto 0);
    signal fracRPostNorm1dto0_uid345_bc_uid9_fpComplexMulTest_in : STD_LOGIC_VECTOR (1 downto 0);
    signal fracRPostNorm1dto0_uid345_bc_uid9_fpComplexMulTest_b : STD_LOGIC_VECTOR (1 downto 0);
    signal lrs_uid346_bc_uid9_fpComplexMulTest_q : STD_LOGIC_VECTOR (2 downto 0);
    signal roundBitDetectionPattern_uid348_bc_uid9_fpComplexMulTest_q : STD_LOGIC_VECTOR (0 downto 0);
    signal roundBit_uid349_bc_uid9_fpComplexMulTest_q : STD_LOGIC_VECTOR (0 downto 0);
    signal expFracPreRound_uid350_bc_uid9_fpComplexMulTest_q : STD_LOGIC_VECTOR (34 downto 0);
    signal roundBitAndNormalizationOp_uid352_bc_uid9_fpComplexMulTest_q : STD_LOGIC_VECTOR (25 downto 0);
    signal expFracRPostRounding_uid353_bc_uid9_fpComplexMulTest_a : STD_LOGIC_VECTOR (36 downto 0);
    signal expFracRPostRounding_uid353_bc_uid9_fpComplexMulTest_b : STD_LOGIC_VECTOR (36 downto 0);
    signal expFracRPostRounding_uid353_bc_uid9_fpComplexMulTest_o : STD_LOGIC_VECTOR (36 downto 0);
    signal expFracRPostRounding_uid353_bc_uid9_fpComplexMulTest_q : STD_LOGIC_VECTOR (35 downto 0);
    signal fracRPreExc_uid354_bc_uid9_fpComplexMulTest_in : STD_LOGIC_VECTOR (23 downto 0);
    signal fracRPreExc_uid354_bc_uid9_fpComplexMulTest_b : STD_LOGIC_VECTOR (22 downto 0);
    signal expRPreExcExt_uid355_bc_uid9_fpComplexMulTest_b : STD_LOGIC_VECTOR (11 downto 0);
    signal expRPreExc_uid356_bc_uid9_fpComplexMulTest_in : STD_LOGIC_VECTOR (7 downto 0);
    signal expRPreExc_uid356_bc_uid9_fpComplexMulTest_b : STD_LOGIC_VECTOR (7 downto 0);
    signal expOvf_uid359_bc_uid9_fpComplexMulTest_a : STD_LOGIC_VECTOR (13 downto 0);
    signal expOvf_uid359_bc_uid9_fpComplexMulTest_b : STD_LOGIC_VECTOR (13 downto 0);
    signal expOvf_uid359_bc_uid9_fpComplexMulTest_o : STD_LOGIC_VECTOR (13 downto 0);
    signal expOvf_uid359_bc_uid9_fpComplexMulTest_c : STD_LOGIC_VECTOR (0 downto 0);
    signal excXZAndExcYZ_uid360_bc_uid9_fpComplexMulTest_q : STD_LOGIC_VECTOR (0 downto 0);
    signal excXZAndExcYR_uid361_bc_uid9_fpComplexMulTest_q : STD_LOGIC_VECTOR (0 downto 0);
    signal excYZAndExcXR_uid362_bc_uid9_fpComplexMulTest_q : STD_LOGIC_VECTOR (0 downto 0);
    signal excZC3_uid363_bc_uid9_fpComplexMulTest_q : STD_LOGIC_VECTOR (0 downto 0);
    signal excRZero_uid364_bc_uid9_fpComplexMulTest_q : STD_LOGIC_VECTOR (0 downto 0);
    signal excXIAndExcYI_uid365_bc_uid9_fpComplexMulTest_q : STD_LOGIC_VECTOR (0 downto 0);
    signal excXRAndExcYI_uid366_bc_uid9_fpComplexMulTest_q : STD_LOGIC_VECTOR (0 downto 0);
    signal excYRAndExcXI_uid367_bc_uid9_fpComplexMulTest_q : STD_LOGIC_VECTOR (0 downto 0);
    signal ExcROvfAndInReg_uid368_bc_uid9_fpComplexMulTest_q : STD_LOGIC_VECTOR (0 downto 0);
    signal excRInf_uid369_bc_uid9_fpComplexMulTest_q : STD_LOGIC_VECTOR (0 downto 0);
    signal excYZAndExcXI_uid370_bc_uid9_fpComplexMulTest_q : STD_LOGIC_VECTOR (0 downto 0);
    signal excXZAndExcYI_uid371_bc_uid9_fpComplexMulTest_q : STD_LOGIC_VECTOR (0 downto 0);
    signal ZeroTimesInf_uid372_bc_uid9_fpComplexMulTest_q : STD_LOGIC_VECTOR (0 downto 0);
    signal excRNaN_uid373_bc_uid9_fpComplexMulTest_q : STD_LOGIC_VECTOR (0 downto 0);
    signal concExc_uid374_bc_uid9_fpComplexMulTest_q : STD_LOGIC_VECTOR (2 downto 0);
    signal excREnc_uid375_bc_uid9_fpComplexMulTest_q : STD_LOGIC_VECTOR (1 downto 0);
    signal invExcRNaN_uid376_bc_uid9_fpComplexMulTest_q : STD_LOGIC_VECTOR (0 downto 0);
    signal signRPostExc_uid377_bc_uid9_fpComplexMulTest_qi : STD_LOGIC_VECTOR (0 downto 0);
    signal signRPostExc_uid377_bc_uid9_fpComplexMulTest_q : STD_LOGIC_VECTOR (0 downto 0);
    signal R_uid378_bc_uid9_fpComplexMulTest_q : STD_LOGIC_VECTOR (33 downto 0);
    signal excX_uid385_rReal_uid16_fpComplexMulTest_b : STD_LOGIC_VECTOR (1 downto 0);
    signal zero2b_uid386_rReal_uid16_fpComplexMulTest_q : STD_LOGIC_VECTOR (1 downto 0);
    signal one2b_uid387_rReal_uid16_fpComplexMulTest_q : STD_LOGIC_VECTOR (1 downto 0);
    signal two2b_uid388_rReal_uid16_fpComplexMulTest_q : STD_LOGIC_VECTOR (1 downto 0);
    signal three2b_uid389_rReal_uid16_fpComplexMulTest_q : STD_LOGIC_VECTOR (1 downto 0);
    signal excXZero_uid390_rReal_uid16_fpComplexMulTest_q : STD_LOGIC_VECTOR (0 downto 0);
    signal excXReg_uid391_rReal_uid16_fpComplexMulTest_q : STD_LOGIC_VECTOR (0 downto 0);
    signal excXInf_uid392_rReal_uid16_fpComplexMulTest_q : STD_LOGIC_VECTOR (0 downto 0);
    signal excXNaN_uid393_rReal_uid16_fpComplexMulTest_q : STD_LOGIC_VECTOR (0 downto 0);
    signal excX_uid399_rReal_uid16_fpComplexMulTest_b : STD_LOGIC_VECTOR (1 downto 0);
    signal excXZero_uid404_rReal_uid16_fpComplexMulTest_q : STD_LOGIC_VECTOR (0 downto 0);
    signal excXReg_uid405_rReal_uid16_fpComplexMulTest_q : STD_LOGIC_VECTOR (0 downto 0);
    signal excXInf_uid406_rReal_uid16_fpComplexMulTest_q : STD_LOGIC_VECTOR (0 downto 0);
    signal excXNaN_uid407_rReal_uid16_fpComplexMulTest_q : STD_LOGIC_VECTOR (0 downto 0);
    signal expFracX_uid408_rReal_uid16_fpComplexMulTest_b : STD_LOGIC_VECTOR (30 downto 0);
    signal expFracY_uid409_rReal_uid16_fpComplexMulTest_in : STD_LOGIC_VECTOR (30 downto 0);
    signal expFracY_uid409_rReal_uid16_fpComplexMulTest_b : STD_LOGIC_VECTOR (30 downto 0);
    signal xGTEy_uid410_rReal_uid16_fpComplexMulTest_a : STD_LOGIC_VECTOR (32 downto 0);
    signal xGTEy_uid410_rReal_uid16_fpComplexMulTest_b : STD_LOGIC_VECTOR (32 downto 0);
    signal xGTEy_uid410_rReal_uid16_fpComplexMulTest_o : STD_LOGIC_VECTOR (32 downto 0);
    signal xGTEy_uid410_rReal_uid16_fpComplexMulTest_n : STD_LOGIC_VECTOR (0 downto 0);
    signal xGTEyOrYz_uid411_rReal_uid16_fpComplexMulTest_q : STD_LOGIC_VECTOR (0 downto 0);
    signal invExcXZ_uid412_rReal_uid16_fpComplexMulTest_q : STD_LOGIC_VECTOR (0 downto 0);
    signal xGTEy_uid413_rReal_uid16_fpComplexMulTest_q : STD_LOGIC_VECTOR (0 downto 0);
    signal sigY_uid414_rReal_uid16_fpComplexMulTest_in : STD_LOGIC_VECTOR (31 downto 0);
    signal sigY_uid414_rReal_uid16_fpComplexMulTest_b : STD_LOGIC_VECTOR (0 downto 0);
    signal fracY_uid415_rReal_uid16_fpComplexMulTest_in : STD_LOGIC_VECTOR (22 downto 0);
    signal fracY_uid415_rReal_uid16_fpComplexMulTest_b : STD_LOGIC_VECTOR (22 downto 0);
    signal expY_uid416_rReal_uid16_fpComplexMulTest_in : STD_LOGIC_VECTOR (30 downto 0);
    signal expY_uid416_rReal_uid16_fpComplexMulTest_b : STD_LOGIC_VECTOR (7 downto 0);
    signal ypn_uid417_rReal_uid16_fpComplexMulTest_q : STD_LOGIC_VECTOR (31 downto 0);
    signal xMuxRange_uid419_rReal_uid16_fpComplexMulTest_in : STD_LOGIC_VECTOR (31 downto 0);
    signal xMuxRange_uid419_rReal_uid16_fpComplexMulTest_b : STD_LOGIC_VECTOR (31 downto 0);
    signal aSig_uid421_rReal_uid16_fpComplexMulTest_s : STD_LOGIC_VECTOR (0 downto 0);
    signal aSig_uid421_rReal_uid16_fpComplexMulTest_q : STD_LOGIC_VECTOR (31 downto 0);
    signal bSig_uid422_rReal_uid16_fpComplexMulTest_s : STD_LOGIC_VECTOR (0 downto 0);
    signal bSig_uid422_rReal_uid16_fpComplexMulTest_q : STD_LOGIC_VECTOR (31 downto 0);
    signal excAI_uid423_rReal_uid16_fpComplexMulTest_s : STD_LOGIC_VECTOR (0 downto 0);
    signal excAI_uid423_rReal_uid16_fpComplexMulTest_q : STD_LOGIC_VECTOR (0 downto 0);
    signal excAN_uid424_rReal_uid16_fpComplexMulTest_s : STD_LOGIC_VECTOR (0 downto 0);
    signal excAN_uid424_rReal_uid16_fpComplexMulTest_q : STD_LOGIC_VECTOR (0 downto 0);
    signal excAR_uid425_rReal_uid16_fpComplexMulTest_s : STD_LOGIC_VECTOR (0 downto 0);
    signal excAR_uid425_rReal_uid16_fpComplexMulTest_q : STD_LOGIC_VECTOR (0 downto 0);
    signal excAZ_uid426_rReal_uid16_fpComplexMulTest_s : STD_LOGIC_VECTOR (0 downto 0);
    signal excAZ_uid426_rReal_uid16_fpComplexMulTest_q : STD_LOGIC_VECTOR (0 downto 0);
    signal excBI_uid427_rReal_uid16_fpComplexMulTest_s : STD_LOGIC_VECTOR (0 downto 0);
    signal excBI_uid427_rReal_uid16_fpComplexMulTest_q : STD_LOGIC_VECTOR (0 downto 0);
    signal excBN_uid428_rReal_uid16_fpComplexMulTest_s : STD_LOGIC_VECTOR (0 downto 0);
    signal excBN_uid428_rReal_uid16_fpComplexMulTest_q : STD_LOGIC_VECTOR (0 downto 0);
    signal excBR_uid429_rReal_uid16_fpComplexMulTest_s : STD_LOGIC_VECTOR (0 downto 0);
    signal excBR_uid429_rReal_uid16_fpComplexMulTest_q : STD_LOGIC_VECTOR (0 downto 0);
    signal excBZ_uid430_rReal_uid16_fpComplexMulTest_s : STD_LOGIC_VECTOR (0 downto 0);
    signal excBZ_uid430_rReal_uid16_fpComplexMulTest_q : STD_LOGIC_VECTOR (0 downto 0);
    signal expA_uid431_rReal_uid16_fpComplexMulTest_in : STD_LOGIC_VECTOR (30 downto 0);
    signal expA_uid431_rReal_uid16_fpComplexMulTest_b : STD_LOGIC_VECTOR (7 downto 0);
    signal expB_uid432_rReal_uid16_fpComplexMulTest_in : STD_LOGIC_VECTOR (30 downto 0);
    signal expB_uid432_rReal_uid16_fpComplexMulTest_b : STD_LOGIC_VECTOR (7 downto 0);
    signal fracA_uid433_rReal_uid16_fpComplexMulTest_in : STD_LOGIC_VECTOR (22 downto 0);
    signal fracA_uid433_rReal_uid16_fpComplexMulTest_b : STD_LOGIC_VECTOR (22 downto 0);
    signal fracB_uid434_rReal_uid16_fpComplexMulTest_in : STD_LOGIC_VECTOR (22 downto 0);
    signal fracB_uid434_rReal_uid16_fpComplexMulTest_b : STD_LOGIC_VECTOR (22 downto 0);
    signal sigA_uid435_rReal_uid16_fpComplexMulTest_b : STD_LOGIC_VECTOR (0 downto 0);
    signal sigB_uid436_rReal_uid16_fpComplexMulTest_b : STD_LOGIC_VECTOR (0 downto 0);
    signal effSub_uid437_rReal_uid16_fpComplexMulTest_q : STD_LOGIC_VECTOR (0 downto 0);
    signal fracBz_uid443_rReal_uid16_fpComplexMulTest_s : STD_LOGIC_VECTOR (0 downto 0);
    signal fracBz_uid443_rReal_uid16_fpComplexMulTest_q : STD_LOGIC_VECTOR (22 downto 0);
    signal invExcBZ_uid445_rReal_uid16_fpComplexMulTest_q : STD_LOGIC_VECTOR (0 downto 0);
    signal oFracB_uid446_rReal_uid16_fpComplexMulTest_q : STD_LOGIC_VECTOR (23 downto 0);
    signal expAmExpB_uid447_rReal_uid16_fpComplexMulTest_a : STD_LOGIC_VECTOR (8 downto 0);
    signal expAmExpB_uid447_rReal_uid16_fpComplexMulTest_b : STD_LOGIC_VECTOR (8 downto 0);
    signal expAmExpB_uid447_rReal_uid16_fpComplexMulTest_i : STD_LOGIC_VECTOR (8 downto 0);
    signal expAmExpB_uid447_rReal_uid16_fpComplexMulTest_o : STD_LOGIC_VECTOR (8 downto 0);
    signal expAmExpB_uid447_rReal_uid16_fpComplexMulTest_q : STD_LOGIC_VECTOR (8 downto 0);
    signal cWFP2_uid448_rReal_uid16_fpComplexMulTest_q : STD_LOGIC_VECTOR (4 downto 0);
    signal shiftedOut_uid450_rReal_uid16_fpComplexMulTest_a : STD_LOGIC_VECTOR (10 downto 0);
    signal shiftedOut_uid450_rReal_uid16_fpComplexMulTest_b : STD_LOGIC_VECTOR (10 downto 0);
    signal shiftedOut_uid450_rReal_uid16_fpComplexMulTest_o : STD_LOGIC_VECTOR (10 downto 0);
    signal shiftedOut_uid450_rReal_uid16_fpComplexMulTest_c : STD_LOGIC_VECTOR (0 downto 0);
    signal padConst_uid451_rReal_uid16_fpComplexMulTest_q : STD_LOGIC_VECTOR (24 downto 0);
    signal rightPaddedIn_uid452_rReal_uid16_fpComplexMulTest_q : STD_LOGIC_VECTOR (48 downto 0);
    signal iShiftedOut_uid454_rReal_uid16_fpComplexMulTest_q : STD_LOGIC_VECTOR (0 downto 0);
    signal alignFracBPostShiftOut_uid455_rReal_uid16_fpComplexMulTest_b : STD_LOGIC_VECTOR (48 downto 0);
    signal alignFracBPostShiftOut_uid455_rReal_uid16_fpComplexMulTest_q : STD_LOGIC_VECTOR (48 downto 0);
    signal cmpEQ_stickyBits_cZwF_uid458_rReal_uid16_fpComplexMulTest_q : STD_LOGIC_VECTOR (0 downto 0);
    signal invCmpEQ_stickyBits_cZwF_uid459_rReal_uid16_fpComplexMulTest_qi : STD_LOGIC_VECTOR (0 downto 0);
    signal invCmpEQ_stickyBits_cZwF_uid459_rReal_uid16_fpComplexMulTest_q : STD_LOGIC_VECTOR (0 downto 0);
    signal effSubInvSticky_uid461_rReal_uid16_fpComplexMulTest_q : STD_LOGIC_VECTOR (0 downto 0);
    signal fracAAddOp_uid464_rReal_uid16_fpComplexMulTest_q : STD_LOGIC_VECTOR (26 downto 0);
    signal fracBAddOp_uid467_rReal_uid16_fpComplexMulTest_q : STD_LOGIC_VECTOR (26 downto 0);
    signal fracBAddOpPostXor_uid468_rReal_uid16_fpComplexMulTest_b : STD_LOGIC_VECTOR (26 downto 0);
    signal fracBAddOpPostXor_uid468_rReal_uid16_fpComplexMulTest_q : STD_LOGIC_VECTOR (26 downto 0);
    signal fracAddResult_uid469_rReal_uid16_fpComplexMulTest_a : STD_LOGIC_VECTOR (27 downto 0);
    signal fracAddResult_uid469_rReal_uid16_fpComplexMulTest_b : STD_LOGIC_VECTOR (27 downto 0);
    signal fracAddResult_uid469_rReal_uid16_fpComplexMulTest_o : STD_LOGIC_VECTOR (27 downto 0);
    signal fracAddResult_uid469_rReal_uid16_fpComplexMulTest_q : STD_LOGIC_VECTOR (27 downto 0);
    signal rangeFracAddResultMwfp3Dto0_uid470_rReal_uid16_fpComplexMulTest_in : STD_LOGIC_VECTOR (26 downto 0);
    signal rangeFracAddResultMwfp3Dto0_uid470_rReal_uid16_fpComplexMulTest_b : STD_LOGIC_VECTOR (26 downto 0);
    signal fracGRS_uid471_rReal_uid16_fpComplexMulTest_q : STD_LOGIC_VECTOR (27 downto 0);
    signal cAmA_uid473_rReal_uid16_fpComplexMulTest_q : STD_LOGIC_VECTOR (4 downto 0);
    signal aMinusA_uid474_rReal_uid16_fpComplexMulTest_q : STD_LOGIC_VECTOR (0 downto 0);
    signal fracPostNorm_uid476_rReal_uid16_fpComplexMulTest_b : STD_LOGIC_VECTOR (26 downto 0);
    signal oneCST_uid477_rReal_uid16_fpComplexMulTest_q : STD_LOGIC_VECTOR (7 downto 0);
    signal expInc_uid478_rReal_uid16_fpComplexMulTest_a : STD_LOGIC_VECTOR (8 downto 0);
    signal expInc_uid478_rReal_uid16_fpComplexMulTest_b : STD_LOGIC_VECTOR (8 downto 0);
    signal expInc_uid478_rReal_uid16_fpComplexMulTest_o : STD_LOGIC_VECTOR (8 downto 0);
    signal expInc_uid478_rReal_uid16_fpComplexMulTest_q : STD_LOGIC_VECTOR (8 downto 0);
    signal expPostNorm_uid479_rReal_uid16_fpComplexMulTest_a : STD_LOGIC_VECTOR (9 downto 0);
    signal expPostNorm_uid479_rReal_uid16_fpComplexMulTest_b : STD_LOGIC_VECTOR (9 downto 0);
    signal expPostNorm_uid479_rReal_uid16_fpComplexMulTest_o : STD_LOGIC_VECTOR (9 downto 0);
    signal expPostNorm_uid479_rReal_uid16_fpComplexMulTest_q : STD_LOGIC_VECTOR (9 downto 0);
    signal Sticky0_uid480_rReal_uid16_fpComplexMulTest_in : STD_LOGIC_VECTOR (0 downto 0);
    signal Sticky0_uid480_rReal_uid16_fpComplexMulTest_b : STD_LOGIC_VECTOR (0 downto 0);
    signal Sticky1_uid481_rReal_uid16_fpComplexMulTest_in : STD_LOGIC_VECTOR (1 downto 0);
    signal Sticky1_uid481_rReal_uid16_fpComplexMulTest_b : STD_LOGIC_VECTOR (0 downto 0);
    signal Round_uid482_rReal_uid16_fpComplexMulTest_in : STD_LOGIC_VECTOR (2 downto 0);
    signal Round_uid482_rReal_uid16_fpComplexMulTest_b : STD_LOGIC_VECTOR (0 downto 0);
    signal Guard_uid483_rReal_uid16_fpComplexMulTest_in : STD_LOGIC_VECTOR (3 downto 0);
    signal Guard_uid483_rReal_uid16_fpComplexMulTest_b : STD_LOGIC_VECTOR (0 downto 0);
    signal LSB_uid484_rReal_uid16_fpComplexMulTest_in : STD_LOGIC_VECTOR (4 downto 0);
    signal LSB_uid484_rReal_uid16_fpComplexMulTest_b : STD_LOGIC_VECTOR (0 downto 0);
    signal rndBitCond_uid485_rReal_uid16_fpComplexMulTest_q : STD_LOGIC_VECTOR (4 downto 0);
    signal cRBit_uid486_rReal_uid16_fpComplexMulTest_q : STD_LOGIC_VECTOR (4 downto 0);
    signal rBi_uid487_rReal_uid16_fpComplexMulTest_qi : STD_LOGIC_VECTOR (0 downto 0);
    signal rBi_uid487_rReal_uid16_fpComplexMulTest_q : STD_LOGIC_VECTOR (0 downto 0);
    signal roundBit_uid488_rReal_uid16_fpComplexMulTest_q : STD_LOGIC_VECTOR (0 downto 0);
    signal fracPostNormRndRange_uid489_rReal_uid16_fpComplexMulTest_in : STD_LOGIC_VECTOR (25 downto 0);
    signal fracPostNormRndRange_uid489_rReal_uid16_fpComplexMulTest_b : STD_LOGIC_VECTOR (23 downto 0);
    signal expFracR_uid490_rReal_uid16_fpComplexMulTest_q : STD_LOGIC_VECTOR (33 downto 0);
    signal rndExpFrac_uid491_rReal_uid16_fpComplexMulTest_a : STD_LOGIC_VECTOR (34 downto 0);
    signal rndExpFrac_uid491_rReal_uid16_fpComplexMulTest_b : STD_LOGIC_VECTOR (34 downto 0);
    signal rndExpFrac_uid491_rReal_uid16_fpComplexMulTest_o : STD_LOGIC_VECTOR (34 downto 0);
    signal rndExpFrac_uid491_rReal_uid16_fpComplexMulTest_q : STD_LOGIC_VECTOR (34 downto 0);
    signal wEP2AllOwE_uid492_rReal_uid16_fpComplexMulTest_q : STD_LOGIC_VECTOR (9 downto 0);
    signal rndExp_uid493_rReal_uid16_fpComplexMulTest_in : STD_LOGIC_VECTOR (33 downto 0);
    signal rndExp_uid493_rReal_uid16_fpComplexMulTest_b : STD_LOGIC_VECTOR (9 downto 0);
    signal rOvfEQMax_uid494_rReal_uid16_fpComplexMulTest_q : STD_LOGIC_VECTOR (0 downto 0);
    signal rndExpFracOvfBits_uid496_rReal_uid16_fpComplexMulTest_in : STD_LOGIC_VECTOR (33 downto 0);
    signal rndExpFracOvfBits_uid496_rReal_uid16_fpComplexMulTest_b : STD_LOGIC_VECTOR (1 downto 0);
    signal rOvfExtraBits_uid497_rReal_uid16_fpComplexMulTest_q : STD_LOGIC_VECTOR (0 downto 0);
    signal rOvf_uid498_rReal_uid16_fpComplexMulTest_q : STD_LOGIC_VECTOR (0 downto 0);
    signal wEP2AllZ_uid499_rReal_uid16_fpComplexMulTest_q : STD_LOGIC_VECTOR (9 downto 0);
    signal rUdfEQMin_uid500_rReal_uid16_fpComplexMulTest_q : STD_LOGIC_VECTOR (0 downto 0);
    signal rUdfExtraBit_uid501_rReal_uid16_fpComplexMulTest_in : STD_LOGIC_VECTOR (33 downto 0);
    signal rUdfExtraBit_uid501_rReal_uid16_fpComplexMulTest_b : STD_LOGIC_VECTOR (0 downto 0);
    signal rUdf_uid502_rReal_uid16_fpComplexMulTest_q : STD_LOGIC_VECTOR (0 downto 0);
    signal fracRPreExc_uid503_rReal_uid16_fpComplexMulTest_in : STD_LOGIC_VECTOR (23 downto 0);
    signal fracRPreExc_uid503_rReal_uid16_fpComplexMulTest_b : STD_LOGIC_VECTOR (22 downto 0);
    signal expRPreExc_uid504_rReal_uid16_fpComplexMulTest_in : STD_LOGIC_VECTOR (31 downto 0);
    signal expRPreExc_uid504_rReal_uid16_fpComplexMulTest_b : STD_LOGIC_VECTOR (7 downto 0);
    signal regInputs_uid505_rReal_uid16_fpComplexMulTest_q : STD_LOGIC_VECTOR (0 downto 0);
    signal excRZeroVInC_uid506_rReal_uid16_fpComplexMulTest_q : STD_LOGIC_VECTOR (4 downto 0);
    signal excRZero_uid507_rReal_uid16_fpComplexMulTest_q : STD_LOGIC_VECTOR (0 downto 0);
    signal aRegBZeroFPLib_uid508_rReal_uid16_fpComplexMulTest_q : STD_LOGIC_VECTOR (0 downto 0);
    signal aZeroBRegFPLib_uid509_rReal_uid16_fpComplexMulTest_q : STD_LOGIC_VECTOR (0 downto 0);
    signal fpLibRegInputs_uid510_rReal_uid16_fpComplexMulTest_q : STD_LOGIC_VECTOR (0 downto 0);
    signal rInfOvf_uid511_rReal_uid16_fpComplexMulTest_q : STD_LOGIC_VECTOR (0 downto 0);
    signal excRInfVInC_uid512_rReal_uid16_fpComplexMulTest_q : STD_LOGIC_VECTOR (5 downto 0);
    signal excRInf_uid513_rReal_uid16_fpComplexMulTest_q : STD_LOGIC_VECTOR (0 downto 0);
    signal excRNaN2_uid514_rReal_uid16_fpComplexMulTest_q : STD_LOGIC_VECTOR (0 downto 0);
    signal excAIBISub_uid515_rReal_uid16_fpComplexMulTest_q : STD_LOGIC_VECTOR (0 downto 0);
    signal excRNaN_uid516_rReal_uid16_fpComplexMulTest_q : STD_LOGIC_VECTOR (0 downto 0);
    signal concExc_uid517_rReal_uid16_fpComplexMulTest_q : STD_LOGIC_VECTOR (2 downto 0);
    signal excREnc_uid518_rReal_uid16_fpComplexMulTest_q : STD_LOGIC_VECTOR (1 downto 0);
    signal invAMinusA_uid519_rReal_uid16_fpComplexMulTest_q : STD_LOGIC_VECTOR (0 downto 0);
    signal signRReg_uid520_rReal_uid16_fpComplexMulTest_q : STD_LOGIC_VECTOR (0 downto 0);
    signal sigBBInf_uid521_rReal_uid16_fpComplexMulTest_q : STD_LOGIC_VECTOR (0 downto 0);
    signal sigAAInf_uid522_rReal_uid16_fpComplexMulTest_q : STD_LOGIC_VECTOR (0 downto 0);
    signal signRInf_uid523_rReal_uid16_fpComplexMulTest_q : STD_LOGIC_VECTOR (0 downto 0);
    signal excAZBZSigASigB_uid524_rReal_uid16_fpComplexMulTest_q : STD_LOGIC_VECTOR (0 downto 0);
    signal excBZARSigA_uid525_rReal_uid16_fpComplexMulTest_q : STD_LOGIC_VECTOR (0 downto 0);
    signal signRZero_uid526_rReal_uid16_fpComplexMulTest_q : STD_LOGIC_VECTOR (0 downto 0);
    signal signRInfRZRReg_uid527_rReal_uid16_fpComplexMulTest_qi : STD_LOGIC_VECTOR (0 downto 0);
    signal signRInfRZRReg_uid527_rReal_uid16_fpComplexMulTest_q : STD_LOGIC_VECTOR (0 downto 0);
    signal invExcRNaN_uid528_rReal_uid16_fpComplexMulTest_q : STD_LOGIC_VECTOR (0 downto 0);
    signal signRPostExc_uid529_rReal_uid16_fpComplexMulTest_q : STD_LOGIC_VECTOR (0 downto 0);
    signal oneFracRPostExc2_uid530_rReal_uid16_fpComplexMulTest_q : STD_LOGIC_VECTOR (22 downto 0);
    signal fracRPostExc_uid533_rReal_uid16_fpComplexMulTest_s : STD_LOGIC_VECTOR (1 downto 0);
    signal fracRPostExc_uid533_rReal_uid16_fpComplexMulTest_q : STD_LOGIC_VECTOR (22 downto 0);
    signal expRPostExc_uid537_rReal_uid16_fpComplexMulTest_s : STD_LOGIC_VECTOR (1 downto 0);
    signal expRPostExc_uid537_rReal_uid16_fpComplexMulTest_q : STD_LOGIC_VECTOR (7 downto 0);
    signal R_uid538_rReal_uid16_fpComplexMulTest_q : STD_LOGIC_VECTOR (31 downto 0);
    signal excX_uid545_rImag_uid17_fpComplexMulTest_b : STD_LOGIC_VECTOR (1 downto 0);
    signal excXZero_uid550_rImag_uid17_fpComplexMulTest_q : STD_LOGIC_VECTOR (0 downto 0);
    signal excXReg_uid551_rImag_uid17_fpComplexMulTest_q : STD_LOGIC_VECTOR (0 downto 0);
    signal excXInf_uid552_rImag_uid17_fpComplexMulTest_q : STD_LOGIC_VECTOR (0 downto 0);
    signal excXNaN_uid553_rImag_uid17_fpComplexMulTest_q : STD_LOGIC_VECTOR (0 downto 0);
    signal excX_uid559_rImag_uid17_fpComplexMulTest_b : STD_LOGIC_VECTOR (1 downto 0);
    signal excXZero_uid564_rImag_uid17_fpComplexMulTest_q : STD_LOGIC_VECTOR (0 downto 0);
    signal excXReg_uid565_rImag_uid17_fpComplexMulTest_q : STD_LOGIC_VECTOR (0 downto 0);
    signal excXInf_uid566_rImag_uid17_fpComplexMulTest_q : STD_LOGIC_VECTOR (0 downto 0);
    signal excXNaN_uid567_rImag_uid17_fpComplexMulTest_q : STD_LOGIC_VECTOR (0 downto 0);
    signal expFracX_uid568_rImag_uid17_fpComplexMulTest_b : STD_LOGIC_VECTOR (30 downto 0);
    signal expFracY_uid569_rImag_uid17_fpComplexMulTest_b : STD_LOGIC_VECTOR (30 downto 0);
    signal xGTEy_uid570_rImag_uid17_fpComplexMulTest_a : STD_LOGIC_VECTOR (32 downto 0);
    signal xGTEy_uid570_rImag_uid17_fpComplexMulTest_b : STD_LOGIC_VECTOR (32 downto 0);
    signal xGTEy_uid570_rImag_uid17_fpComplexMulTest_o : STD_LOGIC_VECTOR (32 downto 0);
    signal xGTEy_uid570_rImag_uid17_fpComplexMulTest_n : STD_LOGIC_VECTOR (0 downto 0);
    signal xGTEyOrYz_uid571_rImag_uid17_fpComplexMulTest_q : STD_LOGIC_VECTOR (0 downto 0);
    signal invExcXZ_uid572_rImag_uid17_fpComplexMulTest_q : STD_LOGIC_VECTOR (0 downto 0);
    signal xGTEy_uid573_rImag_uid17_fpComplexMulTest_q : STD_LOGIC_VECTOR (0 downto 0);
    signal sigY_uid574_rImag_uid17_fpComplexMulTest_b : STD_LOGIC_VECTOR (0 downto 0);
    signal fracY_uid575_rImag_uid17_fpComplexMulTest_b : STD_LOGIC_VECTOR (22 downto 0);
    signal expY_uid576_rImag_uid17_fpComplexMulTest_b : STD_LOGIC_VECTOR (7 downto 0);
    signal ypn_uid577_rImag_uid17_fpComplexMulTest_q : STD_LOGIC_VECTOR (31 downto 0);
    signal xMuxRange_uid579_rImag_uid17_fpComplexMulTest_in : STD_LOGIC_VECTOR (31 downto 0);
    signal xMuxRange_uid579_rImag_uid17_fpComplexMulTest_b : STD_LOGIC_VECTOR (31 downto 0);
    signal aSig_uid581_rImag_uid17_fpComplexMulTest_s : STD_LOGIC_VECTOR (0 downto 0);
    signal aSig_uid581_rImag_uid17_fpComplexMulTest_q : STD_LOGIC_VECTOR (31 downto 0);
    signal bSig_uid582_rImag_uid17_fpComplexMulTest_s : STD_LOGIC_VECTOR (0 downto 0);
    signal bSig_uid582_rImag_uid17_fpComplexMulTest_q : STD_LOGIC_VECTOR (31 downto 0);
    signal excAI_uid583_rImag_uid17_fpComplexMulTest_s : STD_LOGIC_VECTOR (0 downto 0);
    signal excAI_uid583_rImag_uid17_fpComplexMulTest_q : STD_LOGIC_VECTOR (0 downto 0);
    signal excAN_uid584_rImag_uid17_fpComplexMulTest_s : STD_LOGIC_VECTOR (0 downto 0);
    signal excAN_uid584_rImag_uid17_fpComplexMulTest_q : STD_LOGIC_VECTOR (0 downto 0);
    signal excAR_uid585_rImag_uid17_fpComplexMulTest_s : STD_LOGIC_VECTOR (0 downto 0);
    signal excAR_uid585_rImag_uid17_fpComplexMulTest_q : STD_LOGIC_VECTOR (0 downto 0);
    signal excAZ_uid586_rImag_uid17_fpComplexMulTest_s : STD_LOGIC_VECTOR (0 downto 0);
    signal excAZ_uid586_rImag_uid17_fpComplexMulTest_q : STD_LOGIC_VECTOR (0 downto 0);
    signal excBI_uid587_rImag_uid17_fpComplexMulTest_s : STD_LOGIC_VECTOR (0 downto 0);
    signal excBI_uid587_rImag_uid17_fpComplexMulTest_q : STD_LOGIC_VECTOR (0 downto 0);
    signal excBN_uid588_rImag_uid17_fpComplexMulTest_s : STD_LOGIC_VECTOR (0 downto 0);
    signal excBN_uid588_rImag_uid17_fpComplexMulTest_q : STD_LOGIC_VECTOR (0 downto 0);
    signal excBR_uid589_rImag_uid17_fpComplexMulTest_s : STD_LOGIC_VECTOR (0 downto 0);
    signal excBR_uid589_rImag_uid17_fpComplexMulTest_q : STD_LOGIC_VECTOR (0 downto 0);
    signal excBZ_uid590_rImag_uid17_fpComplexMulTest_s : STD_LOGIC_VECTOR (0 downto 0);
    signal excBZ_uid590_rImag_uid17_fpComplexMulTest_q : STD_LOGIC_VECTOR (0 downto 0);
    signal expA_uid591_rImag_uid17_fpComplexMulTest_in : STD_LOGIC_VECTOR (30 downto 0);
    signal expA_uid591_rImag_uid17_fpComplexMulTest_b : STD_LOGIC_VECTOR (7 downto 0);
    signal expB_uid592_rImag_uid17_fpComplexMulTest_in : STD_LOGIC_VECTOR (30 downto 0);
    signal expB_uid592_rImag_uid17_fpComplexMulTest_b : STD_LOGIC_VECTOR (7 downto 0);
    signal fracA_uid593_rImag_uid17_fpComplexMulTest_in : STD_LOGIC_VECTOR (22 downto 0);
    signal fracA_uid593_rImag_uid17_fpComplexMulTest_b : STD_LOGIC_VECTOR (22 downto 0);
    signal fracB_uid594_rImag_uid17_fpComplexMulTest_in : STD_LOGIC_VECTOR (22 downto 0);
    signal fracB_uid594_rImag_uid17_fpComplexMulTest_b : STD_LOGIC_VECTOR (22 downto 0);
    signal sigA_uid595_rImag_uid17_fpComplexMulTest_b : STD_LOGIC_VECTOR (0 downto 0);
    signal sigB_uid596_rImag_uid17_fpComplexMulTest_b : STD_LOGIC_VECTOR (0 downto 0);
    signal effSub_uid597_rImag_uid17_fpComplexMulTest_q : STD_LOGIC_VECTOR (0 downto 0);
    signal fracBz_uid603_rImag_uid17_fpComplexMulTest_s : STD_LOGIC_VECTOR (0 downto 0);
    signal fracBz_uid603_rImag_uid17_fpComplexMulTest_q : STD_LOGIC_VECTOR (22 downto 0);
    signal invExcBZ_uid605_rImag_uid17_fpComplexMulTest_q : STD_LOGIC_VECTOR (0 downto 0);
    signal oFracB_uid606_rImag_uid17_fpComplexMulTest_q : STD_LOGIC_VECTOR (23 downto 0);
    signal expAmExpB_uid607_rImag_uid17_fpComplexMulTest_a : STD_LOGIC_VECTOR (8 downto 0);
    signal expAmExpB_uid607_rImag_uid17_fpComplexMulTest_b : STD_LOGIC_VECTOR (8 downto 0);
    signal expAmExpB_uid607_rImag_uid17_fpComplexMulTest_i : STD_LOGIC_VECTOR (8 downto 0);
    signal expAmExpB_uid607_rImag_uid17_fpComplexMulTest_o : STD_LOGIC_VECTOR (8 downto 0);
    signal expAmExpB_uid607_rImag_uid17_fpComplexMulTest_q : STD_LOGIC_VECTOR (8 downto 0);
    signal shiftedOut_uid610_rImag_uid17_fpComplexMulTest_a : STD_LOGIC_VECTOR (10 downto 0);
    signal shiftedOut_uid610_rImag_uid17_fpComplexMulTest_b : STD_LOGIC_VECTOR (10 downto 0);
    signal shiftedOut_uid610_rImag_uid17_fpComplexMulTest_o : STD_LOGIC_VECTOR (10 downto 0);
    signal shiftedOut_uid610_rImag_uid17_fpComplexMulTest_c : STD_LOGIC_VECTOR (0 downto 0);
    signal rightPaddedIn_uid612_rImag_uid17_fpComplexMulTest_q : STD_LOGIC_VECTOR (48 downto 0);
    signal iShiftedOut_uid614_rImag_uid17_fpComplexMulTest_q : STD_LOGIC_VECTOR (0 downto 0);
    signal alignFracBPostShiftOut_uid615_rImag_uid17_fpComplexMulTest_b : STD_LOGIC_VECTOR (48 downto 0);
    signal alignFracBPostShiftOut_uid615_rImag_uid17_fpComplexMulTest_q : STD_LOGIC_VECTOR (48 downto 0);
    signal cmpEQ_stickyBits_cZwF_uid618_rImag_uid17_fpComplexMulTest_q : STD_LOGIC_VECTOR (0 downto 0);
    signal invCmpEQ_stickyBits_cZwF_uid619_rImag_uid17_fpComplexMulTest_qi : STD_LOGIC_VECTOR (0 downto 0);
    signal invCmpEQ_stickyBits_cZwF_uid619_rImag_uid17_fpComplexMulTest_q : STD_LOGIC_VECTOR (0 downto 0);
    signal effSubInvSticky_uid621_rImag_uid17_fpComplexMulTest_q : STD_LOGIC_VECTOR (0 downto 0);
    signal fracAAddOp_uid624_rImag_uid17_fpComplexMulTest_q : STD_LOGIC_VECTOR (26 downto 0);
    signal fracBAddOp_uid627_rImag_uid17_fpComplexMulTest_q : STD_LOGIC_VECTOR (26 downto 0);
    signal fracBAddOpPostXor_uid628_rImag_uid17_fpComplexMulTest_b : STD_LOGIC_VECTOR (26 downto 0);
    signal fracBAddOpPostXor_uid628_rImag_uid17_fpComplexMulTest_q : STD_LOGIC_VECTOR (26 downto 0);
    signal fracAddResult_uid629_rImag_uid17_fpComplexMulTest_a : STD_LOGIC_VECTOR (27 downto 0);
    signal fracAddResult_uid629_rImag_uid17_fpComplexMulTest_b : STD_LOGIC_VECTOR (27 downto 0);
    signal fracAddResult_uid629_rImag_uid17_fpComplexMulTest_o : STD_LOGIC_VECTOR (27 downto 0);
    signal fracAddResult_uid629_rImag_uid17_fpComplexMulTest_q : STD_LOGIC_VECTOR (27 downto 0);
    signal rangeFracAddResultMwfp3Dto0_uid630_rImag_uid17_fpComplexMulTest_in : STD_LOGIC_VECTOR (26 downto 0);
    signal rangeFracAddResultMwfp3Dto0_uid630_rImag_uid17_fpComplexMulTest_b : STD_LOGIC_VECTOR (26 downto 0);
    signal fracGRS_uid631_rImag_uid17_fpComplexMulTest_q : STD_LOGIC_VECTOR (27 downto 0);
    signal aMinusA_uid634_rImag_uid17_fpComplexMulTest_qi : STD_LOGIC_VECTOR (0 downto 0);
    signal aMinusA_uid634_rImag_uid17_fpComplexMulTest_q : STD_LOGIC_VECTOR (0 downto 0);
    signal fracPostNorm_uid636_rImag_uid17_fpComplexMulTest_b : STD_LOGIC_VECTOR (26 downto 0);
    signal expInc_uid638_rImag_uid17_fpComplexMulTest_a : STD_LOGIC_VECTOR (8 downto 0);
    signal expInc_uid638_rImag_uid17_fpComplexMulTest_b : STD_LOGIC_VECTOR (8 downto 0);
    signal expInc_uid638_rImag_uid17_fpComplexMulTest_o : STD_LOGIC_VECTOR (8 downto 0);
    signal expInc_uid638_rImag_uid17_fpComplexMulTest_q : STD_LOGIC_VECTOR (8 downto 0);
    signal expPostNorm_uid639_rImag_uid17_fpComplexMulTest_a : STD_LOGIC_VECTOR (9 downto 0);
    signal expPostNorm_uid639_rImag_uid17_fpComplexMulTest_b : STD_LOGIC_VECTOR (9 downto 0);
    signal expPostNorm_uid639_rImag_uid17_fpComplexMulTest_o : STD_LOGIC_VECTOR (9 downto 0);
    signal expPostNorm_uid639_rImag_uid17_fpComplexMulTest_q : STD_LOGIC_VECTOR (9 downto 0);
    signal Sticky0_uid640_rImag_uid17_fpComplexMulTest_in : STD_LOGIC_VECTOR (0 downto 0);
    signal Sticky0_uid640_rImag_uid17_fpComplexMulTest_b : STD_LOGIC_VECTOR (0 downto 0);
    signal Sticky1_uid641_rImag_uid17_fpComplexMulTest_in : STD_LOGIC_VECTOR (1 downto 0);
    signal Sticky1_uid641_rImag_uid17_fpComplexMulTest_b : STD_LOGIC_VECTOR (0 downto 0);
    signal Round_uid642_rImag_uid17_fpComplexMulTest_in : STD_LOGIC_VECTOR (2 downto 0);
    signal Round_uid642_rImag_uid17_fpComplexMulTest_b : STD_LOGIC_VECTOR (0 downto 0);
    signal Guard_uid643_rImag_uid17_fpComplexMulTest_in : STD_LOGIC_VECTOR (3 downto 0);
    signal Guard_uid643_rImag_uid17_fpComplexMulTest_b : STD_LOGIC_VECTOR (0 downto 0);
    signal LSB_uid644_rImag_uid17_fpComplexMulTest_in : STD_LOGIC_VECTOR (4 downto 0);
    signal LSB_uid644_rImag_uid17_fpComplexMulTest_b : STD_LOGIC_VECTOR (0 downto 0);
    signal rndBitCond_uid645_rImag_uid17_fpComplexMulTest_q : STD_LOGIC_VECTOR (4 downto 0);
    signal rBi_uid647_rImag_uid17_fpComplexMulTest_qi : STD_LOGIC_VECTOR (0 downto 0);
    signal rBi_uid647_rImag_uid17_fpComplexMulTest_q : STD_LOGIC_VECTOR (0 downto 0);
    signal roundBit_uid648_rImag_uid17_fpComplexMulTest_q : STD_LOGIC_VECTOR (0 downto 0);
    signal fracPostNormRndRange_uid649_rImag_uid17_fpComplexMulTest_in : STD_LOGIC_VECTOR (25 downto 0);
    signal fracPostNormRndRange_uid649_rImag_uid17_fpComplexMulTest_b : STD_LOGIC_VECTOR (23 downto 0);
    signal expFracR_uid650_rImag_uid17_fpComplexMulTest_q : STD_LOGIC_VECTOR (33 downto 0);
    signal rndExpFrac_uid651_rImag_uid17_fpComplexMulTest_a : STD_LOGIC_VECTOR (34 downto 0);
    signal rndExpFrac_uid651_rImag_uid17_fpComplexMulTest_b : STD_LOGIC_VECTOR (34 downto 0);
    signal rndExpFrac_uid651_rImag_uid17_fpComplexMulTest_o : STD_LOGIC_VECTOR (34 downto 0);
    signal rndExpFrac_uid651_rImag_uid17_fpComplexMulTest_q : STD_LOGIC_VECTOR (34 downto 0);
    signal rndExp_uid653_rImag_uid17_fpComplexMulTest_in : STD_LOGIC_VECTOR (33 downto 0);
    signal rndExp_uid653_rImag_uid17_fpComplexMulTest_b : STD_LOGIC_VECTOR (9 downto 0);
    signal rOvfEQMax_uid654_rImag_uid17_fpComplexMulTest_q : STD_LOGIC_VECTOR (0 downto 0);
    signal rndExpFracOvfBits_uid656_rImag_uid17_fpComplexMulTest_in : STD_LOGIC_VECTOR (33 downto 0);
    signal rndExpFracOvfBits_uid656_rImag_uid17_fpComplexMulTest_b : STD_LOGIC_VECTOR (1 downto 0);
    signal rOvfExtraBits_uid657_rImag_uid17_fpComplexMulTest_q : STD_LOGIC_VECTOR (0 downto 0);
    signal rOvf_uid658_rImag_uid17_fpComplexMulTest_q : STD_LOGIC_VECTOR (0 downto 0);
    signal rUdfEQMin_uid660_rImag_uid17_fpComplexMulTest_q : STD_LOGIC_VECTOR (0 downto 0);
    signal rUdfExtraBit_uid661_rImag_uid17_fpComplexMulTest_in : STD_LOGIC_VECTOR (33 downto 0);
    signal rUdfExtraBit_uid661_rImag_uid17_fpComplexMulTest_b : STD_LOGIC_VECTOR (0 downto 0);
    signal rUdf_uid662_rImag_uid17_fpComplexMulTest_q : STD_LOGIC_VECTOR (0 downto 0);
    signal fracRPreExc_uid663_rImag_uid17_fpComplexMulTest_in : STD_LOGIC_VECTOR (23 downto 0);
    signal fracRPreExc_uid663_rImag_uid17_fpComplexMulTest_b : STD_LOGIC_VECTOR (22 downto 0);
    signal expRPreExc_uid664_rImag_uid17_fpComplexMulTest_in : STD_LOGIC_VECTOR (31 downto 0);
    signal expRPreExc_uid664_rImag_uid17_fpComplexMulTest_b : STD_LOGIC_VECTOR (7 downto 0);
    signal regInputs_uid665_rImag_uid17_fpComplexMulTest_q : STD_LOGIC_VECTOR (0 downto 0);
    signal excRZeroVInC_uid666_rImag_uid17_fpComplexMulTest_q : STD_LOGIC_VECTOR (4 downto 0);
    signal excRZero_uid667_rImag_uid17_fpComplexMulTest_q : STD_LOGIC_VECTOR (0 downto 0);
    signal aRegBZeroFPLib_uid668_rImag_uid17_fpComplexMulTest_q : STD_LOGIC_VECTOR (0 downto 0);
    signal aZeroBRegFPLib_uid669_rImag_uid17_fpComplexMulTest_q : STD_LOGIC_VECTOR (0 downto 0);
    signal fpLibRegInputs_uid670_rImag_uid17_fpComplexMulTest_q : STD_LOGIC_VECTOR (0 downto 0);
    signal rInfOvf_uid671_rImag_uid17_fpComplexMulTest_q : STD_LOGIC_VECTOR (0 downto 0);
    signal excRInfVInC_uid672_rImag_uid17_fpComplexMulTest_q : STD_LOGIC_VECTOR (5 downto 0);
    signal excRInf_uid673_rImag_uid17_fpComplexMulTest_q : STD_LOGIC_VECTOR (0 downto 0);
    signal excRNaN2_uid674_rImag_uid17_fpComplexMulTest_q : STD_LOGIC_VECTOR (0 downto 0);
    signal excAIBISub_uid675_rImag_uid17_fpComplexMulTest_q : STD_LOGIC_VECTOR (0 downto 0);
    signal excRNaN_uid676_rImag_uid17_fpComplexMulTest_q : STD_LOGIC_VECTOR (0 downto 0);
    signal concExc_uid677_rImag_uid17_fpComplexMulTest_q : STD_LOGIC_VECTOR (2 downto 0);
    signal excREnc_uid678_rImag_uid17_fpComplexMulTest_q : STD_LOGIC_VECTOR (1 downto 0);
    signal invAMinusA_uid679_rImag_uid17_fpComplexMulTest_q : STD_LOGIC_VECTOR (0 downto 0);
    signal signRReg_uid680_rImag_uid17_fpComplexMulTest_q : STD_LOGIC_VECTOR (0 downto 0);
    signal sigBBInf_uid681_rImag_uid17_fpComplexMulTest_q : STD_LOGIC_VECTOR (0 downto 0);
    signal sigAAInf_uid682_rImag_uid17_fpComplexMulTest_q : STD_LOGIC_VECTOR (0 downto 0);
    signal signRInf_uid683_rImag_uid17_fpComplexMulTest_q : STD_LOGIC_VECTOR (0 downto 0);
    signal excAZBZSigASigB_uid684_rImag_uid17_fpComplexMulTest_q : STD_LOGIC_VECTOR (0 downto 0);
    signal excBZARSigA_uid685_rImag_uid17_fpComplexMulTest_q : STD_LOGIC_VECTOR (0 downto 0);
    signal signRZero_uid686_rImag_uid17_fpComplexMulTest_q : STD_LOGIC_VECTOR (0 downto 0);
    signal signRInfRZRReg_uid687_rImag_uid17_fpComplexMulTest_q : STD_LOGIC_VECTOR (0 downto 0);
    signal invExcRNaN_uid688_rImag_uid17_fpComplexMulTest_q : STD_LOGIC_VECTOR (0 downto 0);
    signal signRPostExc_uid689_rImag_uid17_fpComplexMulTest_q : STD_LOGIC_VECTOR (0 downto 0);
    signal fracRPostExc_uid693_rImag_uid17_fpComplexMulTest_s : STD_LOGIC_VECTOR (1 downto 0);
    signal fracRPostExc_uid693_rImag_uid17_fpComplexMulTest_q : STD_LOGIC_VECTOR (22 downto 0);
    signal expRPostExc_uid697_rImag_uid17_fpComplexMulTest_s : STD_LOGIC_VECTOR (1 downto 0);
    signal expRPostExc_uid697_rImag_uid17_fpComplexMulTest_q : STD_LOGIC_VECTOR (7 downto 0);
    signal R_uid698_rImag_uid17_fpComplexMulTest_q : STD_LOGIC_VECTOR (31 downto 0);
    signal zs_uid712_lzCountVal_uid472_rReal_uid16_fpComplexMulTest_q : STD_LOGIC_VECTOR (15 downto 0);
    signal rVStage_uid713_lzCountVal_uid472_rReal_uid16_fpComplexMulTest_b : STD_LOGIC_VECTOR (15 downto 0);
    signal vCount_uid714_lzCountVal_uid472_rReal_uid16_fpComplexMulTest_q : STD_LOGIC_VECTOR (0 downto 0);
    signal mO_uid715_lzCountVal_uid472_rReal_uid16_fpComplexMulTest_q : STD_LOGIC_VECTOR (3 downto 0);
    signal vStage_uid716_lzCountVal_uid472_rReal_uid16_fpComplexMulTest_in : STD_LOGIC_VECTOR (11 downto 0);
    signal vStage_uid716_lzCountVal_uid472_rReal_uid16_fpComplexMulTest_b : STD_LOGIC_VECTOR (11 downto 0);
    signal cStage_uid717_lzCountVal_uid472_rReal_uid16_fpComplexMulTest_q : STD_LOGIC_VECTOR (15 downto 0);
    signal vStagei_uid719_lzCountVal_uid472_rReal_uid16_fpComplexMulTest_s : STD_LOGIC_VECTOR (0 downto 0);
    signal vStagei_uid719_lzCountVal_uid472_rReal_uid16_fpComplexMulTest_q : STD_LOGIC_VECTOR (15 downto 0);
    signal vCount_uid722_lzCountVal_uid472_rReal_uid16_fpComplexMulTest_q : STD_LOGIC_VECTOR (0 downto 0);
    signal vStagei_uid725_lzCountVal_uid472_rReal_uid16_fpComplexMulTest_s : STD_LOGIC_VECTOR (0 downto 0);
    signal vStagei_uid725_lzCountVal_uid472_rReal_uid16_fpComplexMulTest_q : STD_LOGIC_VECTOR (7 downto 0);
    signal zs_uid726_lzCountVal_uid472_rReal_uid16_fpComplexMulTest_q : STD_LOGIC_VECTOR (3 downto 0);
    signal vCount_uid728_lzCountVal_uid472_rReal_uid16_fpComplexMulTest_q : STD_LOGIC_VECTOR (0 downto 0);
    signal vStagei_uid731_lzCountVal_uid472_rReal_uid16_fpComplexMulTest_s : STD_LOGIC_VECTOR (0 downto 0);
    signal vStagei_uid731_lzCountVal_uid472_rReal_uid16_fpComplexMulTest_q : STD_LOGIC_VECTOR (3 downto 0);
    signal vCount_uid734_lzCountVal_uid472_rReal_uid16_fpComplexMulTest_q : STD_LOGIC_VECTOR (0 downto 0);
    signal vStagei_uid737_lzCountVal_uid472_rReal_uid16_fpComplexMulTest_s : STD_LOGIC_VECTOR (0 downto 0);
    signal vStagei_uid737_lzCountVal_uid472_rReal_uid16_fpComplexMulTest_q : STD_LOGIC_VECTOR (1 downto 0);
    signal rVStage_uid739_lzCountVal_uid472_rReal_uid16_fpComplexMulTest_b : STD_LOGIC_VECTOR (0 downto 0);
    signal vCount_uid740_lzCountVal_uid472_rReal_uid16_fpComplexMulTest_q : STD_LOGIC_VECTOR (0 downto 0);
    signal r_uid741_lzCountVal_uid472_rReal_uid16_fpComplexMulTest_q : STD_LOGIC_VECTOR (4 downto 0);
    signal rVStage_uid744_lzCountVal_uid632_rImag_uid17_fpComplexMulTest_b : STD_LOGIC_VECTOR (15 downto 0);
    signal vCount_uid745_lzCountVal_uid632_rImag_uid17_fpComplexMulTest_q : STD_LOGIC_VECTOR (0 downto 0);
    signal vStage_uid747_lzCountVal_uid632_rImag_uid17_fpComplexMulTest_in : STD_LOGIC_VECTOR (11 downto 0);
    signal vStage_uid747_lzCountVal_uid632_rImag_uid17_fpComplexMulTest_b : STD_LOGIC_VECTOR (11 downto 0);
    signal cStage_uid748_lzCountVal_uid632_rImag_uid17_fpComplexMulTest_q : STD_LOGIC_VECTOR (15 downto 0);
    signal vStagei_uid750_lzCountVal_uid632_rImag_uid17_fpComplexMulTest_s : STD_LOGIC_VECTOR (0 downto 0);
    signal vStagei_uid750_lzCountVal_uid632_rImag_uid17_fpComplexMulTest_q : STD_LOGIC_VECTOR (15 downto 0);
    signal vCount_uid753_lzCountVal_uid632_rImag_uid17_fpComplexMulTest_q : STD_LOGIC_VECTOR (0 downto 0);
    signal vStagei_uid756_lzCountVal_uid632_rImag_uid17_fpComplexMulTest_s : STD_LOGIC_VECTOR (0 downto 0);
    signal vStagei_uid756_lzCountVal_uid632_rImag_uid17_fpComplexMulTest_q : STD_LOGIC_VECTOR (7 downto 0);
    signal vCount_uid759_lzCountVal_uid632_rImag_uid17_fpComplexMulTest_q : STD_LOGIC_VECTOR (0 downto 0);
    signal vStagei_uid762_lzCountVal_uid632_rImag_uid17_fpComplexMulTest_s : STD_LOGIC_VECTOR (0 downto 0);
    signal vStagei_uid762_lzCountVal_uid632_rImag_uid17_fpComplexMulTest_q : STD_LOGIC_VECTOR (3 downto 0);
    signal vCount_uid765_lzCountVal_uid632_rImag_uid17_fpComplexMulTest_q : STD_LOGIC_VECTOR (0 downto 0);
    signal vStagei_uid768_lzCountVal_uid632_rImag_uid17_fpComplexMulTest_s : STD_LOGIC_VECTOR (0 downto 0);
    signal vStagei_uid768_lzCountVal_uid632_rImag_uid17_fpComplexMulTest_q : STD_LOGIC_VECTOR (1 downto 0);
    signal rVStage_uid770_lzCountVal_uid632_rImag_uid17_fpComplexMulTest_b : STD_LOGIC_VECTOR (0 downto 0);
    signal vCount_uid771_lzCountVal_uid632_rImag_uid17_fpComplexMulTest_q : STD_LOGIC_VECTOR (0 downto 0);
    signal r_uid772_lzCountVal_uid632_rImag_uid17_fpComplexMulTest_q : STD_LOGIC_VECTOR (4 downto 0);
    signal expUdf_uid87_ac_uid6_fpComplexMulTest_cmp_sign_q : STD_LOGIC_VECTOR (0 downto 0);
    signal expUdf_uid177_bd_uid7_fpComplexMulTest_cmp_sign_q : STD_LOGIC_VECTOR (0 downto 0);
    signal expUdf_uid267_ad_uid8_fpComplexMulTest_cmp_sign_q : STD_LOGIC_VECTOR (0 downto 0);
    signal expUdf_uid357_bc_uid9_fpComplexMulTest_cmp_sign_q : STD_LOGIC_VECTOR (0 downto 0);
    signal wIntCst_uid784_alignmentShifter_uid451_rReal_uid16_fpComplexMulTest_q : STD_LOGIC_VECTOR (5 downto 0);
    signal shiftedOut_uid785_alignmentShifter_uid451_rReal_uid16_fpComplexMulTest_a : STD_LOGIC_VECTOR (10 downto 0);
    signal shiftedOut_uid785_alignmentShifter_uid451_rReal_uid16_fpComplexMulTest_b : STD_LOGIC_VECTOR (10 downto 0);
    signal shiftedOut_uid785_alignmentShifter_uid451_rReal_uid16_fpComplexMulTest_o : STD_LOGIC_VECTOR (10 downto 0);
    signal shiftedOut_uid785_alignmentShifter_uid451_rReal_uid16_fpComplexMulTest_n : STD_LOGIC_VECTOR (0 downto 0);
    signal rightShiftStage0Idx1Rng16_uid786_alignmentShifter_uid451_rReal_uid16_fpComplexMulTest_b : STD_LOGIC_VECTOR (32 downto 0);
    signal rightShiftStage0Idx1_uid788_alignmentShifter_uid451_rReal_uid16_fpComplexMulTest_q : STD_LOGIC_VECTOR (48 downto 0);
    signal rightShiftStage0Idx2Rng32_uid789_alignmentShifter_uid451_rReal_uid16_fpComplexMulTest_b : STD_LOGIC_VECTOR (16 downto 0);
    signal rightShiftStage0Idx2Pad32_uid790_alignmentShifter_uid451_rReal_uid16_fpComplexMulTest_q : STD_LOGIC_VECTOR (31 downto 0);
    signal rightShiftStage0Idx2_uid791_alignmentShifter_uid451_rReal_uid16_fpComplexMulTest_q : STD_LOGIC_VECTOR (48 downto 0);
    signal rightShiftStage0Idx3Rng48_uid792_alignmentShifter_uid451_rReal_uid16_fpComplexMulTest_b : STD_LOGIC_VECTOR (0 downto 0);
    signal rightShiftStage0Idx3Pad48_uid793_alignmentShifter_uid451_rReal_uid16_fpComplexMulTest_q : STD_LOGIC_VECTOR (47 downto 0);
    signal rightShiftStage0Idx3_uid794_alignmentShifter_uid451_rReal_uid16_fpComplexMulTest_q : STD_LOGIC_VECTOR (48 downto 0);
    signal rightShiftStage0_uid796_alignmentShifter_uid451_rReal_uid16_fpComplexMulTest_s : STD_LOGIC_VECTOR (1 downto 0);
    signal rightShiftStage0_uid796_alignmentShifter_uid451_rReal_uid16_fpComplexMulTest_q : STD_LOGIC_VECTOR (48 downto 0);
    signal rightShiftStage1Idx1Rng4_uid797_alignmentShifter_uid451_rReal_uid16_fpComplexMulTest_b : STD_LOGIC_VECTOR (44 downto 0);
    signal rightShiftStage1Idx1_uid799_alignmentShifter_uid451_rReal_uid16_fpComplexMulTest_q : STD_LOGIC_VECTOR (48 downto 0);
    signal rightShiftStage1Idx2Rng8_uid800_alignmentShifter_uid451_rReal_uid16_fpComplexMulTest_b : STD_LOGIC_VECTOR (40 downto 0);
    signal rightShiftStage1Idx2_uid802_alignmentShifter_uid451_rReal_uid16_fpComplexMulTest_q : STD_LOGIC_VECTOR (48 downto 0);
    signal rightShiftStage1Idx3Rng12_uid803_alignmentShifter_uid451_rReal_uid16_fpComplexMulTest_b : STD_LOGIC_VECTOR (36 downto 0);
    signal rightShiftStage1Idx3Pad12_uid804_alignmentShifter_uid451_rReal_uid16_fpComplexMulTest_q : STD_LOGIC_VECTOR (11 downto 0);
    signal rightShiftStage1Idx3_uid805_alignmentShifter_uid451_rReal_uid16_fpComplexMulTest_q : STD_LOGIC_VECTOR (48 downto 0);
    signal rightShiftStage1_uid807_alignmentShifter_uid451_rReal_uid16_fpComplexMulTest_s : STD_LOGIC_VECTOR (1 downto 0);
    signal rightShiftStage1_uid807_alignmentShifter_uid451_rReal_uid16_fpComplexMulTest_q : STD_LOGIC_VECTOR (48 downto 0);
    signal rightShiftStage2Idx1Rng1_uid808_alignmentShifter_uid451_rReal_uid16_fpComplexMulTest_b : STD_LOGIC_VECTOR (47 downto 0);
    signal rightShiftStage2Idx1_uid810_alignmentShifter_uid451_rReal_uid16_fpComplexMulTest_q : STD_LOGIC_VECTOR (48 downto 0);
    signal rightShiftStage2Idx2Rng2_uid811_alignmentShifter_uid451_rReal_uid16_fpComplexMulTest_b : STD_LOGIC_VECTOR (46 downto 0);
    signal rightShiftStage2Idx2_uid813_alignmentShifter_uid451_rReal_uid16_fpComplexMulTest_q : STD_LOGIC_VECTOR (48 downto 0);
    signal rightShiftStage2Idx3Rng3_uid814_alignmentShifter_uid451_rReal_uid16_fpComplexMulTest_b : STD_LOGIC_VECTOR (45 downto 0);
    signal rightShiftStage2Idx3Pad3_uid815_alignmentShifter_uid451_rReal_uid16_fpComplexMulTest_q : STD_LOGIC_VECTOR (2 downto 0);
    signal rightShiftStage2Idx3_uid816_alignmentShifter_uid451_rReal_uid16_fpComplexMulTest_q : STD_LOGIC_VECTOR (48 downto 0);
    signal rightShiftStage2_uid818_alignmentShifter_uid451_rReal_uid16_fpComplexMulTest_s : STD_LOGIC_VECTOR (1 downto 0);
    signal rightShiftStage2_uid818_alignmentShifter_uid451_rReal_uid16_fpComplexMulTest_q : STD_LOGIC_VECTOR (48 downto 0);
    signal zeroOutCst_uid819_alignmentShifter_uid451_rReal_uid16_fpComplexMulTest_q : STD_LOGIC_VECTOR (48 downto 0);
    signal r_uid820_alignmentShifter_uid451_rReal_uid16_fpComplexMulTest_s : STD_LOGIC_VECTOR (0 downto 0);
    signal r_uid820_alignmentShifter_uid451_rReal_uid16_fpComplexMulTest_q : STD_LOGIC_VECTOR (48 downto 0);
    signal leftShiftStage0Idx1Rng8_uid825_fracPostNormExt_uid475_rReal_uid16_fpComplexMulTest_in : STD_LOGIC_VECTOR (19 downto 0);
    signal leftShiftStage0Idx1Rng8_uid825_fracPostNormExt_uid475_rReal_uid16_fpComplexMulTest_b : STD_LOGIC_VECTOR (19 downto 0);
    signal leftShiftStage0Idx1_uid826_fracPostNormExt_uid475_rReal_uid16_fpComplexMulTest_q : STD_LOGIC_VECTOR (27 downto 0);
    signal leftShiftStage0Idx2_uid829_fracPostNormExt_uid475_rReal_uid16_fpComplexMulTest_q : STD_LOGIC_VECTOR (27 downto 0);
    signal leftShiftStage0Idx3Pad24_uid830_fracPostNormExt_uid475_rReal_uid16_fpComplexMulTest_q : STD_LOGIC_VECTOR (23 downto 0);
    signal leftShiftStage0Idx3Rng24_uid831_fracPostNormExt_uid475_rReal_uid16_fpComplexMulTest_in : STD_LOGIC_VECTOR (3 downto 0);
    signal leftShiftStage0Idx3Rng24_uid831_fracPostNormExt_uid475_rReal_uid16_fpComplexMulTest_b : STD_LOGIC_VECTOR (3 downto 0);
    signal leftShiftStage0Idx3_uid832_fracPostNormExt_uid475_rReal_uid16_fpComplexMulTest_q : STD_LOGIC_VECTOR (27 downto 0);
    signal leftShiftStage0_uid834_fracPostNormExt_uid475_rReal_uid16_fpComplexMulTest_s : STD_LOGIC_VECTOR (1 downto 0);
    signal leftShiftStage0_uid834_fracPostNormExt_uid475_rReal_uid16_fpComplexMulTest_q : STD_LOGIC_VECTOR (27 downto 0);
    signal leftShiftStage1Idx1Rng2_uid836_fracPostNormExt_uid475_rReal_uid16_fpComplexMulTest_in : STD_LOGIC_VECTOR (25 downto 0);
    signal leftShiftStage1Idx1Rng2_uid836_fracPostNormExt_uid475_rReal_uid16_fpComplexMulTest_b : STD_LOGIC_VECTOR (25 downto 0);
    signal leftShiftStage1Idx1_uid837_fracPostNormExt_uid475_rReal_uid16_fpComplexMulTest_q : STD_LOGIC_VECTOR (27 downto 0);
    signal leftShiftStage1Idx2Rng4_uid839_fracPostNormExt_uid475_rReal_uid16_fpComplexMulTest_in : STD_LOGIC_VECTOR (23 downto 0);
    signal leftShiftStage1Idx2Rng4_uid839_fracPostNormExt_uid475_rReal_uid16_fpComplexMulTest_b : STD_LOGIC_VECTOR (23 downto 0);
    signal leftShiftStage1Idx2_uid840_fracPostNormExt_uid475_rReal_uid16_fpComplexMulTest_q : STD_LOGIC_VECTOR (27 downto 0);
    signal leftShiftStage1Idx3Pad6_uid841_fracPostNormExt_uid475_rReal_uid16_fpComplexMulTest_q : STD_LOGIC_VECTOR (5 downto 0);
    signal leftShiftStage1Idx3Rng6_uid842_fracPostNormExt_uid475_rReal_uid16_fpComplexMulTest_in : STD_LOGIC_VECTOR (21 downto 0);
    signal leftShiftStage1Idx3Rng6_uid842_fracPostNormExt_uid475_rReal_uid16_fpComplexMulTest_b : STD_LOGIC_VECTOR (21 downto 0);
    signal leftShiftStage1Idx3_uid843_fracPostNormExt_uid475_rReal_uid16_fpComplexMulTest_q : STD_LOGIC_VECTOR (27 downto 0);
    signal leftShiftStage1_uid845_fracPostNormExt_uid475_rReal_uid16_fpComplexMulTest_s : STD_LOGIC_VECTOR (1 downto 0);
    signal leftShiftStage1_uid845_fracPostNormExt_uid475_rReal_uid16_fpComplexMulTest_q : STD_LOGIC_VECTOR (27 downto 0);
    signal leftShiftStage2Idx1Rng1_uid847_fracPostNormExt_uid475_rReal_uid16_fpComplexMulTest_in : STD_LOGIC_VECTOR (26 downto 0);
    signal leftShiftStage2Idx1Rng1_uid847_fracPostNormExt_uid475_rReal_uid16_fpComplexMulTest_b : STD_LOGIC_VECTOR (26 downto 0);
    signal leftShiftStage2Idx1_uid848_fracPostNormExt_uid475_rReal_uid16_fpComplexMulTest_q : STD_LOGIC_VECTOR (27 downto 0);
    signal leftShiftStage2_uid850_fracPostNormExt_uid475_rReal_uid16_fpComplexMulTest_s : STD_LOGIC_VECTOR (0 downto 0);
    signal leftShiftStage2_uid850_fracPostNormExt_uid475_rReal_uid16_fpComplexMulTest_q : STD_LOGIC_VECTOR (27 downto 0);
    signal shiftedOut_uid855_alignmentShifter_uid611_rImag_uid17_fpComplexMulTest_a : STD_LOGIC_VECTOR (10 downto 0);
    signal shiftedOut_uid855_alignmentShifter_uid611_rImag_uid17_fpComplexMulTest_b : STD_LOGIC_VECTOR (10 downto 0);
    signal shiftedOut_uid855_alignmentShifter_uid611_rImag_uid17_fpComplexMulTest_o : STD_LOGIC_VECTOR (10 downto 0);
    signal shiftedOut_uid855_alignmentShifter_uid611_rImag_uid17_fpComplexMulTest_n : STD_LOGIC_VECTOR (0 downto 0);
    signal rightShiftStage0Idx1Rng16_uid856_alignmentShifter_uid611_rImag_uid17_fpComplexMulTest_b : STD_LOGIC_VECTOR (32 downto 0);
    signal rightShiftStage0Idx1_uid858_alignmentShifter_uid611_rImag_uid17_fpComplexMulTest_q : STD_LOGIC_VECTOR (48 downto 0);
    signal rightShiftStage0Idx2Rng32_uid859_alignmentShifter_uid611_rImag_uid17_fpComplexMulTest_b : STD_LOGIC_VECTOR (16 downto 0);
    signal rightShiftStage0Idx2_uid861_alignmentShifter_uid611_rImag_uid17_fpComplexMulTest_q : STD_LOGIC_VECTOR (48 downto 0);
    signal rightShiftStage0Idx3Rng48_uid862_alignmentShifter_uid611_rImag_uid17_fpComplexMulTest_b : STD_LOGIC_VECTOR (0 downto 0);
    signal rightShiftStage0Idx3_uid864_alignmentShifter_uid611_rImag_uid17_fpComplexMulTest_q : STD_LOGIC_VECTOR (48 downto 0);
    signal rightShiftStage0_uid866_alignmentShifter_uid611_rImag_uid17_fpComplexMulTest_s : STD_LOGIC_VECTOR (1 downto 0);
    signal rightShiftStage0_uid866_alignmentShifter_uid611_rImag_uid17_fpComplexMulTest_q : STD_LOGIC_VECTOR (48 downto 0);
    signal rightShiftStage1Idx1Rng4_uid867_alignmentShifter_uid611_rImag_uid17_fpComplexMulTest_b : STD_LOGIC_VECTOR (44 downto 0);
    signal rightShiftStage1Idx1_uid869_alignmentShifter_uid611_rImag_uid17_fpComplexMulTest_q : STD_LOGIC_VECTOR (48 downto 0);
    signal rightShiftStage1Idx2Rng8_uid870_alignmentShifter_uid611_rImag_uid17_fpComplexMulTest_b : STD_LOGIC_VECTOR (40 downto 0);
    signal rightShiftStage1Idx2_uid872_alignmentShifter_uid611_rImag_uid17_fpComplexMulTest_q : STD_LOGIC_VECTOR (48 downto 0);
    signal rightShiftStage1Idx3Rng12_uid873_alignmentShifter_uid611_rImag_uid17_fpComplexMulTest_b : STD_LOGIC_VECTOR (36 downto 0);
    signal rightShiftStage1Idx3_uid875_alignmentShifter_uid611_rImag_uid17_fpComplexMulTest_q : STD_LOGIC_VECTOR (48 downto 0);
    signal rightShiftStage1_uid877_alignmentShifter_uid611_rImag_uid17_fpComplexMulTest_s : STD_LOGIC_VECTOR (1 downto 0);
    signal rightShiftStage1_uid877_alignmentShifter_uid611_rImag_uid17_fpComplexMulTest_q : STD_LOGIC_VECTOR (48 downto 0);
    signal rightShiftStage2Idx1Rng1_uid878_alignmentShifter_uid611_rImag_uid17_fpComplexMulTest_b : STD_LOGIC_VECTOR (47 downto 0);
    signal rightShiftStage2Idx1_uid880_alignmentShifter_uid611_rImag_uid17_fpComplexMulTest_q : STD_LOGIC_VECTOR (48 downto 0);
    signal rightShiftStage2Idx2Rng2_uid881_alignmentShifter_uid611_rImag_uid17_fpComplexMulTest_b : STD_LOGIC_VECTOR (46 downto 0);
    signal rightShiftStage2Idx2_uid883_alignmentShifter_uid611_rImag_uid17_fpComplexMulTest_q : STD_LOGIC_VECTOR (48 downto 0);
    signal rightShiftStage2Idx3Rng3_uid884_alignmentShifter_uid611_rImag_uid17_fpComplexMulTest_b : STD_LOGIC_VECTOR (45 downto 0);
    signal rightShiftStage2Idx3_uid886_alignmentShifter_uid611_rImag_uid17_fpComplexMulTest_q : STD_LOGIC_VECTOR (48 downto 0);
    signal rightShiftStage2_uid888_alignmentShifter_uid611_rImag_uid17_fpComplexMulTest_s : STD_LOGIC_VECTOR (1 downto 0);
    signal rightShiftStage2_uid888_alignmentShifter_uid611_rImag_uid17_fpComplexMulTest_q : STD_LOGIC_VECTOR (48 downto 0);
    signal r_uid890_alignmentShifter_uid611_rImag_uid17_fpComplexMulTest_s : STD_LOGIC_VECTOR (0 downto 0);
    signal r_uid890_alignmentShifter_uid611_rImag_uid17_fpComplexMulTest_q : STD_LOGIC_VECTOR (48 downto 0);
    signal leftShiftStage0Idx1Rng8_uid895_fracPostNormExt_uid635_rImag_uid17_fpComplexMulTest_in : STD_LOGIC_VECTOR (19 downto 0);
    signal leftShiftStage0Idx1Rng8_uid895_fracPostNormExt_uid635_rImag_uid17_fpComplexMulTest_b : STD_LOGIC_VECTOR (19 downto 0);
    signal leftShiftStage0Idx1_uid896_fracPostNormExt_uid635_rImag_uid17_fpComplexMulTest_q : STD_LOGIC_VECTOR (27 downto 0);
    signal leftShiftStage0Idx2_uid899_fracPostNormExt_uid635_rImag_uid17_fpComplexMulTest_q : STD_LOGIC_VECTOR (27 downto 0);
    signal leftShiftStage0Idx3Rng24_uid901_fracPostNormExt_uid635_rImag_uid17_fpComplexMulTest_in : STD_LOGIC_VECTOR (3 downto 0);
    signal leftShiftStage0Idx3Rng24_uid901_fracPostNormExt_uid635_rImag_uid17_fpComplexMulTest_b : STD_LOGIC_VECTOR (3 downto 0);
    signal leftShiftStage0Idx3_uid902_fracPostNormExt_uid635_rImag_uid17_fpComplexMulTest_q : STD_LOGIC_VECTOR (27 downto 0);
    signal leftShiftStage0_uid904_fracPostNormExt_uid635_rImag_uid17_fpComplexMulTest_s : STD_LOGIC_VECTOR (1 downto 0);
    signal leftShiftStage0_uid904_fracPostNormExt_uid635_rImag_uid17_fpComplexMulTest_q : STD_LOGIC_VECTOR (27 downto 0);
    signal leftShiftStage1Idx1Rng2_uid906_fracPostNormExt_uid635_rImag_uid17_fpComplexMulTest_in : STD_LOGIC_VECTOR (25 downto 0);
    signal leftShiftStage1Idx1Rng2_uid906_fracPostNormExt_uid635_rImag_uid17_fpComplexMulTest_b : STD_LOGIC_VECTOR (25 downto 0);
    signal leftShiftStage1Idx1_uid907_fracPostNormExt_uid635_rImag_uid17_fpComplexMulTest_q : STD_LOGIC_VECTOR (27 downto 0);
    signal leftShiftStage1Idx2Rng4_uid909_fracPostNormExt_uid635_rImag_uid17_fpComplexMulTest_in : STD_LOGIC_VECTOR (23 downto 0);
    signal leftShiftStage1Idx2Rng4_uid909_fracPostNormExt_uid635_rImag_uid17_fpComplexMulTest_b : STD_LOGIC_VECTOR (23 downto 0);
    signal leftShiftStage1Idx2_uid910_fracPostNormExt_uid635_rImag_uid17_fpComplexMulTest_q : STD_LOGIC_VECTOR (27 downto 0);
    signal leftShiftStage1Idx3Rng6_uid912_fracPostNormExt_uid635_rImag_uid17_fpComplexMulTest_in : STD_LOGIC_VECTOR (21 downto 0);
    signal leftShiftStage1Idx3Rng6_uid912_fracPostNormExt_uid635_rImag_uid17_fpComplexMulTest_b : STD_LOGIC_VECTOR (21 downto 0);
    signal leftShiftStage1Idx3_uid913_fracPostNormExt_uid635_rImag_uid17_fpComplexMulTest_q : STD_LOGIC_VECTOR (27 downto 0);
    signal leftShiftStage1_uid915_fracPostNormExt_uid635_rImag_uid17_fpComplexMulTest_s : STD_LOGIC_VECTOR (1 downto 0);
    signal leftShiftStage1_uid915_fracPostNormExt_uid635_rImag_uid17_fpComplexMulTest_q : STD_LOGIC_VECTOR (27 downto 0);
    signal leftShiftStage2Idx1Rng1_uid917_fracPostNormExt_uid635_rImag_uid17_fpComplexMulTest_in : STD_LOGIC_VECTOR (26 downto 0);
    signal leftShiftStage2Idx1Rng1_uid917_fracPostNormExt_uid635_rImag_uid17_fpComplexMulTest_b : STD_LOGIC_VECTOR (26 downto 0);
    signal leftShiftStage2Idx1_uid918_fracPostNormExt_uid635_rImag_uid17_fpComplexMulTest_q : STD_LOGIC_VECTOR (27 downto 0);
    signal leftShiftStage2_uid920_fracPostNormExt_uid635_rImag_uid17_fpComplexMulTest_s : STD_LOGIC_VECTOR (0 downto 0);
    signal leftShiftStage2_uid920_fracPostNormExt_uid635_rImag_uid17_fpComplexMulTest_q : STD_LOGIC_VECTOR (27 downto 0);
    signal prodXY_uid700_prod_uid61_ac_uid6_fpComplexMulTest_cma_reset : std_logic;
    type prodXY_uid700_prod_uid61_ac_uid6_fpComplexMulTest_cma_a0type is array(NATURAL range <>) of UNSIGNED(23 downto 0);
    signal prodXY_uid700_prod_uid61_ac_uid6_fpComplexMulTest_cma_a0 : prodXY_uid700_prod_uid61_ac_uid6_fpComplexMulTest_cma_a0type(0 to 0);
    attribute preserve : boolean;
    attribute preserve of prodXY_uid700_prod_uid61_ac_uid6_fpComplexMulTest_cma_a0 : signal is true;
    signal prodXY_uid700_prod_uid61_ac_uid6_fpComplexMulTest_cma_c0 : prodXY_uid700_prod_uid61_ac_uid6_fpComplexMulTest_cma_a0type(0 to 0);
    attribute preserve of prodXY_uid700_prod_uid61_ac_uid6_fpComplexMulTest_cma_c0 : signal is true;
    type prodXY_uid700_prod_uid61_ac_uid6_fpComplexMulTest_cma_ptype is array(NATURAL range <>) of UNSIGNED(47 downto 0);
    signal prodXY_uid700_prod_uid61_ac_uid6_fpComplexMulTest_cma_p : prodXY_uid700_prod_uid61_ac_uid6_fpComplexMulTest_cma_ptype(0 to 0);
    signal prodXY_uid700_prod_uid61_ac_uid6_fpComplexMulTest_cma_u : prodXY_uid700_prod_uid61_ac_uid6_fpComplexMulTest_cma_ptype(0 to 0);
    signal prodXY_uid700_prod_uid61_ac_uid6_fpComplexMulTest_cma_w : prodXY_uid700_prod_uid61_ac_uid6_fpComplexMulTest_cma_ptype(0 to 0);
    signal prodXY_uid700_prod_uid61_ac_uid6_fpComplexMulTest_cma_x : prodXY_uid700_prod_uid61_ac_uid6_fpComplexMulTest_cma_ptype(0 to 0);
    signal prodXY_uid700_prod_uid61_ac_uid6_fpComplexMulTest_cma_y : prodXY_uid700_prod_uid61_ac_uid6_fpComplexMulTest_cma_ptype(0 to 0);
    signal prodXY_uid700_prod_uid61_ac_uid6_fpComplexMulTest_cma_s : prodXY_uid700_prod_uid61_ac_uid6_fpComplexMulTest_cma_ptype(0 to 0);
    signal prodXY_uid700_prod_uid61_ac_uid6_fpComplexMulTest_cma_qq : STD_LOGIC_VECTOR (47 downto 0);
    signal prodXY_uid700_prod_uid61_ac_uid6_fpComplexMulTest_cma_q : STD_LOGIC_VECTOR (47 downto 0);
    signal prodXY_uid700_prod_uid61_ac_uid6_fpComplexMulTest_cma_ena0 : std_logic;
    signal prodXY_uid700_prod_uid61_ac_uid6_fpComplexMulTest_cma_ena1 : std_logic;
    signal prodXY_uid703_prod_uid151_bd_uid7_fpComplexMulTest_cma_reset : std_logic;
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
    signal prodXY_uid709_prod_uid331_bc_uid9_fpComplexMulTest_cma_u : prodXY_uid700_prod_uid61_ac_uid6_fpComplexMulTest_cma_ptype(0 to 0);
    signal prodXY_uid709_prod_uid331_bc_uid9_fpComplexMulTest_cma_w : prodXY_uid700_prod_uid61_ac_uid6_fpComplexMulTest_cma_ptype(0 to 0);
    signal prodXY_uid709_prod_uid331_bc_uid9_fpComplexMulTest_cma_x : prodXY_uid700_prod_uid61_ac_uid6_fpComplexMulTest_cma_ptype(0 to 0);
    signal prodXY_uid709_prod_uid331_bc_uid9_fpComplexMulTest_cma_y : prodXY_uid700_prod_uid61_ac_uid6_fpComplexMulTest_cma_ptype(0 to 0);
    signal prodXY_uid709_prod_uid331_bc_uid9_fpComplexMulTest_cma_s : prodXY_uid700_prod_uid61_ac_uid6_fpComplexMulTest_cma_ptype(0 to 0);
    signal prodXY_uid709_prod_uid331_bc_uid9_fpComplexMulTest_cma_qq : STD_LOGIC_VECTOR (47 downto 0);
    signal prodXY_uid709_prod_uid331_bc_uid9_fpComplexMulTest_cma_q : STD_LOGIC_VECTOR (47 downto 0);
    signal prodXY_uid709_prod_uid331_bc_uid9_fpComplexMulTest_cma_ena0 : std_logic;
    signal prodXY_uid709_prod_uid331_bc_uid9_fpComplexMulTest_cma_ena1 : std_logic;
    signal rightShiftStageSel5Dto4_uid795_alignmentShifter_uid451_rReal_uid16_fpComplexMulTest_merged_bit_select_in : STD_LOGIC_VECTOR (5 downto 0);
    signal rightShiftStageSel5Dto4_uid795_alignmentShifter_uid451_rReal_uid16_fpComplexMulTest_merged_bit_select_b : STD_LOGIC_VECTOR (1 downto 0);
    signal rightShiftStageSel5Dto4_uid795_alignmentShifter_uid451_rReal_uid16_fpComplexMulTest_merged_bit_select_c : STD_LOGIC_VECTOR (1 downto 0);
    signal rightShiftStageSel5Dto4_uid795_alignmentShifter_uid451_rReal_uid16_fpComplexMulTest_merged_bit_select_d : STD_LOGIC_VECTOR (1 downto 0);
    signal stickyBits_uid456_rReal_uid16_fpComplexMulTest_merged_bit_select_b : STD_LOGIC_VECTOR (22 downto 0);
    signal stickyBits_uid456_rReal_uid16_fpComplexMulTest_merged_bit_select_c : STD_LOGIC_VECTOR (25 downto 0);
    signal rightShiftStageSel5Dto4_uid865_alignmentShifter_uid611_rImag_uid17_fpComplexMulTest_merged_bit_select_in : STD_LOGIC_VECTOR (5 downto 0);
    signal rightShiftStageSel5Dto4_uid865_alignmentShifter_uid611_rImag_uid17_fpComplexMulTest_merged_bit_select_b : STD_LOGIC_VECTOR (1 downto 0);
    signal rightShiftStageSel5Dto4_uid865_alignmentShifter_uid611_rImag_uid17_fpComplexMulTest_merged_bit_select_c : STD_LOGIC_VECTOR (1 downto 0);
    signal rightShiftStageSel5Dto4_uid865_alignmentShifter_uid611_rImag_uid17_fpComplexMulTest_merged_bit_select_d : STD_LOGIC_VECTOR (1 downto 0);
    signal stickyBits_uid616_rImag_uid17_fpComplexMulTest_merged_bit_select_b : STD_LOGIC_VECTOR (22 downto 0);
    signal stickyBits_uid616_rImag_uid17_fpComplexMulTest_merged_bit_select_c : STD_LOGIC_VECTOR (25 downto 0);
    signal rVStage_uid721_lzCountVal_uid472_rReal_uid16_fpComplexMulTest_merged_bit_select_b : STD_LOGIC_VECTOR (7 downto 0);
    signal rVStage_uid721_lzCountVal_uid472_rReal_uid16_fpComplexMulTest_merged_bit_select_c : STD_LOGIC_VECTOR (7 downto 0);
    signal rVStage_uid727_lzCountVal_uid472_rReal_uid16_fpComplexMulTest_merged_bit_select_b : STD_LOGIC_VECTOR (3 downto 0);
    signal rVStage_uid727_lzCountVal_uid472_rReal_uid16_fpComplexMulTest_merged_bit_select_c : STD_LOGIC_VECTOR (3 downto 0);
    signal rVStage_uid733_lzCountVal_uid472_rReal_uid16_fpComplexMulTest_merged_bit_select_b : STD_LOGIC_VECTOR (1 downto 0);
    signal rVStage_uid733_lzCountVal_uid472_rReal_uid16_fpComplexMulTest_merged_bit_select_c : STD_LOGIC_VECTOR (1 downto 0);
    signal leftShiftStageSel4Dto3_uid833_fracPostNormExt_uid475_rReal_uid16_fpComplexMulTest_merged_bit_select_b : STD_LOGIC_VECTOR (1 downto 0);
    signal leftShiftStageSel4Dto3_uid833_fracPostNormExt_uid475_rReal_uid16_fpComplexMulTest_merged_bit_select_c : STD_LOGIC_VECTOR (1 downto 0);
    signal leftShiftStageSel4Dto3_uid833_fracPostNormExt_uid475_rReal_uid16_fpComplexMulTest_merged_bit_select_d : STD_LOGIC_VECTOR (0 downto 0);
    signal rVStage_uid752_lzCountVal_uid632_rImag_uid17_fpComplexMulTest_merged_bit_select_b : STD_LOGIC_VECTOR (7 downto 0);
    signal rVStage_uid752_lzCountVal_uid632_rImag_uid17_fpComplexMulTest_merged_bit_select_c : STD_LOGIC_VECTOR (7 downto 0);
    signal rVStage_uid758_lzCountVal_uid632_rImag_uid17_fpComplexMulTest_merged_bit_select_b : STD_LOGIC_VECTOR (3 downto 0);
    signal rVStage_uid758_lzCountVal_uid632_rImag_uid17_fpComplexMulTest_merged_bit_select_c : STD_LOGIC_VECTOR (3 downto 0);
    signal rVStage_uid764_lzCountVal_uid632_rImag_uid17_fpComplexMulTest_merged_bit_select_b : STD_LOGIC_VECTOR (1 downto 0);
    signal rVStage_uid764_lzCountVal_uid632_rImag_uid17_fpComplexMulTest_merged_bit_select_c : STD_LOGIC_VECTOR (1 downto 0);
    signal leftShiftStageSel4Dto3_uid903_fracPostNormExt_uid635_rImag_uid17_fpComplexMulTest_merged_bit_select_b : STD_LOGIC_VECTOR (1 downto 0);
    signal leftShiftStageSel4Dto3_uid903_fracPostNormExt_uid635_rImag_uid17_fpComplexMulTest_merged_bit_select_c : STD_LOGIC_VECTOR (1 downto 0);
    signal leftShiftStageSel4Dto3_uid903_fracPostNormExt_uid635_rImag_uid17_fpComplexMulTest_merged_bit_select_d : STD_LOGIC_VECTOR (0 downto 0);
    signal redist0_fracPostNormRndRange_uid649_rImag_uid17_fpComplexMulTest_b_1_q : STD_LOGIC_VECTOR (23 downto 0);
    signal redist1_rangeFracAddResultMwfp3Dto0_uid630_rImag_uid17_fpComplexMulTest_b_1_q : STD_LOGIC_VECTOR (26 downto 0);
    signal redist2_effSub_uid597_rImag_uid17_fpComplexMulTest_q_2_q : STD_LOGIC_VECTOR (0 downto 0);
    signal redist3_sigB_uid596_rImag_uid17_fpComplexMulTest_b_1_q : STD_LOGIC_VECTOR (0 downto 0);
    signal redist4_sigB_uid596_rImag_uid17_fpComplexMulTest_b_3_q : STD_LOGIC_VECTOR (0 downto 0);
    signal redist5_sigA_uid595_rImag_uid17_fpComplexMulTest_b_1_q : STD_LOGIC_VECTOR (0 downto 0);
    signal redist6_sigA_uid595_rImag_uid17_fpComplexMulTest_b_3_q : STD_LOGIC_VECTOR (0 downto 0);
    signal redist7_fracB_uid594_rImag_uid17_fpComplexMulTest_b_1_q : STD_LOGIC_VECTOR (22 downto 0);
    signal redist8_fracA_uid593_rImag_uid17_fpComplexMulTest_b_1_q : STD_LOGIC_VECTOR (22 downto 0);
    signal redist9_expA_uid591_rImag_uid17_fpComplexMulTest_b_2_q : STD_LOGIC_VECTOR (7 downto 0);
    signal redist10_excBZ_uid590_rImag_uid17_fpComplexMulTest_q_1_q : STD_LOGIC_VECTOR (0 downto 0);
    signal redist11_excBZ_uid590_rImag_uid17_fpComplexMulTest_q_3_q : STD_LOGIC_VECTOR (0 downto 0);
    signal redist12_excAZ_uid586_rImag_uid17_fpComplexMulTest_q_3_q : STD_LOGIC_VECTOR (0 downto 0);
    signal redist13_xGTEy_uid573_rImag_uid17_fpComplexMulTest_q_3_q : STD_LOGIC_VECTOR (0 downto 0);
    signal redist14_excX_uid559_rImag_uid17_fpComplexMulTest_b_3_q : STD_LOGIC_VECTOR (1 downto 0);
    signal redist15_excX_uid545_rImag_uid17_fpComplexMulTest_b_3_q : STD_LOGIC_VECTOR (1 downto 0);
    signal redist16_fracPostNormRndRange_uid489_rReal_uid16_fpComplexMulTest_b_1_q : STD_LOGIC_VECTOR (23 downto 0);
    signal redist17_aMinusA_uid474_rReal_uid16_fpComplexMulTest_q_1_q : STD_LOGIC_VECTOR (0 downto 0);
    signal redist18_rangeFracAddResultMwfp3Dto0_uid470_rReal_uid16_fpComplexMulTest_b_1_q : STD_LOGIC_VECTOR (26 downto 0);
    signal redist19_effSub_uid437_rReal_uid16_fpComplexMulTest_q_2_q : STD_LOGIC_VECTOR (0 downto 0);
    signal redist20_sigB_uid436_rReal_uid16_fpComplexMulTest_b_1_q : STD_LOGIC_VECTOR (0 downto 0);
    signal redist21_sigB_uid436_rReal_uid16_fpComplexMulTest_b_2_q : STD_LOGIC_VECTOR (0 downto 0);
    signal redist22_sigA_uid435_rReal_uid16_fpComplexMulTest_b_1_q : STD_LOGIC_VECTOR (0 downto 0);
    signal redist23_sigA_uid435_rReal_uid16_fpComplexMulTest_b_2_q : STD_LOGIC_VECTOR (0 downto 0);
    signal redist24_fracB_uid434_rReal_uid16_fpComplexMulTest_b_1_q : STD_LOGIC_VECTOR (22 downto 0);
    signal redist25_fracA_uid433_rReal_uid16_fpComplexMulTest_b_1_q : STD_LOGIC_VECTOR (22 downto 0);
    signal redist26_expA_uid431_rReal_uid16_fpComplexMulTest_b_2_q : STD_LOGIC_VECTOR (7 downto 0);
    signal redist27_excBZ_uid430_rReal_uid16_fpComplexMulTest_q_1_q : STD_LOGIC_VECTOR (0 downto 0);
    signal redist28_excBZ_uid430_rReal_uid16_fpComplexMulTest_q_2_q : STD_LOGIC_VECTOR (0 downto 0);
    signal redist29_excBZ_uid430_rReal_uid16_fpComplexMulTest_q_3_q : STD_LOGIC_VECTOR (0 downto 0);
    signal redist30_excBR_uid429_rReal_uid16_fpComplexMulTest_q_1_q : STD_LOGIC_VECTOR (0 downto 0);
    signal redist31_excBI_uid427_rReal_uid16_fpComplexMulTest_q_1_q : STD_LOGIC_VECTOR (0 downto 0);
    signal redist32_excAZ_uid426_rReal_uid16_fpComplexMulTest_q_2_q : STD_LOGIC_VECTOR (0 downto 0);
    signal redist33_excAZ_uid426_rReal_uid16_fpComplexMulTest_q_3_q : STD_LOGIC_VECTOR (0 downto 0);
    signal redist34_excAR_uid425_rReal_uid16_fpComplexMulTest_q_1_q : STD_LOGIC_VECTOR (0 downto 0);
    signal redist35_excAI_uid423_rReal_uid16_fpComplexMulTest_q_1_q : STD_LOGIC_VECTOR (0 downto 0);
    signal redist36_xGTEy_uid413_rReal_uid16_fpComplexMulTest_q_2_q : STD_LOGIC_VECTOR (0 downto 0);
    signal redist37_excX_uid399_rReal_uid16_fpComplexMulTest_b_2_q : STD_LOGIC_VECTOR (1 downto 0);
    signal redist38_excX_uid385_rReal_uid16_fpComplexMulTest_b_2_q : STD_LOGIC_VECTOR (1 downto 0);
    signal redist39_expRPreExc_uid356_bc_uid9_fpComplexMulTest_b_1_q : STD_LOGIC_VECTOR (7 downto 0);
    signal redist40_fracRPreExc_uid354_bc_uid9_fpComplexMulTest_b_1_q : STD_LOGIC_VECTOR (22 downto 0);
    signal redist41_expRPreExc_uid266_ad_uid8_fpComplexMulTest_b_1_q : STD_LOGIC_VECTOR (7 downto 0);
    signal redist42_fracRPreExc_uid264_ad_uid8_fpComplexMulTest_b_1_q : STD_LOGIC_VECTOR (22 downto 0);
    signal redist43_fracXIsZero_uid135_bd_uid7_fpComplexMulTest_q_2_q : STD_LOGIC_VECTOR (0 downto 0);
    signal redist44_fracXIsZero_uid121_bd_uid7_fpComplexMulTest_q_2_q : STD_LOGIC_VECTOR (0 downto 0);
    signal redist45_signY_uid113_bd_uid7_fpComplexMulTest_b_2_q : STD_LOGIC_VECTOR (0 downto 0);
    signal redist46_signX_uid112_bd_uid7_fpComplexMulTest_b_2_q : STD_LOGIC_VECTOR (0 downto 0);
    signal redist47_expY_uid111_bd_uid7_fpComplexMulTest_b_2_q : STD_LOGIC_VECTOR (7 downto 0);
    signal redist48_expX_uid110_bd_uid7_fpComplexMulTest_b_2_q : STD_LOGIC_VECTOR (7 downto 0);
    signal redist49_expRPreExc_uid86_ac_uid6_fpComplexMulTest_b_1_q : STD_LOGIC_VECTOR (7 downto 0);
    signal redist50_fracRPreExc_uid84_ac_uid6_fpComplexMulTest_b_1_q : STD_LOGIC_VECTOR (22 downto 0);
    signal redist51_fracXIsZero_uid45_ac_uid6_fpComplexMulTest_q_2_q : STD_LOGIC_VECTOR (0 downto 0);
    signal redist52_fracXIsZero_uid31_ac_uid6_fpComplexMulTest_q_2_q : STD_LOGIC_VECTOR (0 downto 0);
    signal redist53_signY_uid23_ac_uid6_fpComplexMulTest_b_2_q : STD_LOGIC_VECTOR (0 downto 0);
    signal redist54_signX_uid22_ac_uid6_fpComplexMulTest_b_2_q : STD_LOGIC_VECTOR (0 downto 0);
    signal redist55_expY_uid21_ac_uid6_fpComplexMulTest_b_2_q : STD_LOGIC_VECTOR (7 downto 0);
    signal redist56_expX_uid20_ac_uid6_fpComplexMulTest_b_2_q : STD_LOGIC_VECTOR (7 downto 0);
    signal redist57_exp_uid13_fpComplexMulTest_b_1_q : STD_LOGIC_VECTOR (7 downto 0);
    signal redist58_fraction_uid12_fpComplexMulTest_b_1_q : STD_LOGIC_VECTOR (22 downto 0);
    signal redist59_excBits_uid11_fpComplexMulTest_b_1_q : STD_LOGIC_VECTOR (1 downto 0);
    signal redist60_ySign_uid10_fpComplexMulTest_b_1_q : STD_LOGIC_VECTOR (0 downto 0);
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
