pocper/SoC-GPS-Hybrid-Acquisition/rtl/ip/FP_mult/FP_mult/FP_mult_0002.vhd

-- ------------------------------------------------------------------------- 
-- High Level Design Compiler for Intel(R) FPGAs Version 25.1std (Release Build #1129)
-- Quartus Prime development tool and MATLAB/Simulink Interface
-- 
-- Legal Notice: Copyright 2025 Intel Corporation.  All rights reserved.
-- Your use of  Intel Corporation's design tools,  logic functions and other
-- software and  tools, and its AMPP partner logic functions, and any output
-- files any  of the foregoing (including  device programming  or simulation
-- files), and  any associated  documentation  or information  are expressly
-- subject  to the terms and  conditions of the  Intel FPGA Software License
-- Agreement, Intel MegaCore Function License Agreement, or other applicable
-- license agreement,  including,  without limitation,  that your use is for
-- the  sole  purpose of  programming  logic devices  manufactured by  Intel
-- and  sold by Intel  or its authorized  distributors. Please refer  to the
-- applicable agreement for further details.
-- ---------------------------------------------------------------------------

-- VHDL created from FP_mult_0002
-- VHDL created on Sat Feb 21 22:27:37 2026


library IEEE;
use IEEE.std_logic_1164.all;
use IEEE.NUMERIC_STD.all;
use IEEE.MATH_REAL.all;
use std.TextIO.all;
use work.dspba_library_package.all;

LIBRARY altera_mf;
USE altera_mf.altera_mf_components.all;
LIBRARY altera_lnsim;
USE altera_lnsim.altera_lnsim_components.altera_syncram;
LIBRARY lpm;
USE lpm.lpm_components.all;

entity FP_mult_0002 is
    port (
        a : in std_logic_vector(31 downto 0);  -- float32_m23
        b : in std_logic_vector(31 downto 0);  -- float32_m23
        q : out std_logic_vector(31 downto 0);  -- float32_m23
        clk : in std_logic;
        areset : in std_logic
    );
end FP_mult_0002;

architecture normal of FP_mult_0002 is

    attribute altera_attribute : string;
    attribute altera_attribute of normal : architecture is "-name AUTO_SHIFT_REGISTER_RECOGNITION OFF; -name PHYSICAL_SYNTHESIS_REGISTER_DUPLICATION ON; -name MESSAGE_DISABLE 10036; -name MESSAGE_DISABLE 10037; -name MESSAGE_DISABLE 14130; -name MESSAGE_DISABLE 14320; -name MESSAGE_DISABLE 15400; -name MESSAGE_DISABLE 14130; -name MESSAGE_DISABLE 10036; -name MESSAGE_DISABLE 12020; -name MESSAGE_DISABLE 12030; -name MESSAGE_DISABLE 12010; -name MESSAGE_DISABLE 12110; -name MESSAGE_DISABLE 14320; -name MESSAGE_DISABLE 13410; -name MESSAGE_DISABLE 113007";
    
    signal GND_q : STD_LOGIC_VECTOR (0 downto 0);
    signal VCC_q : STD_LOGIC_VECTOR (0 downto 0);
    signal expX_uid6_fpMulTest_b : STD_LOGIC_VECTOR (7 downto 0);
    signal expY_uid7_fpMulTest_b : STD_LOGIC_VECTOR (7 downto 0);
    signal signX_uid8_fpMulTest_b : STD_LOGIC_VECTOR (0 downto 0);
    signal signY_uid9_fpMulTest_b : STD_LOGIC_VECTOR (0 downto 0);
    signal cstAllOWE_uid10_fpMulTest_q : STD_LOGIC_VECTOR (7 downto 0);
    signal cstZeroWF_uid11_fpMulTest_q : STD_LOGIC_VECTOR (22 downto 0);
    signal cstAllZWE_uid12_fpMulTest_q : STD_LOGIC_VECTOR (7 downto 0);
    signal frac_x_uid14_fpMulTest_b : STD_LOGIC_VECTOR (22 downto 0);
    signal excZ_x_uid15_fpMulTest_qi : STD_LOGIC_VECTOR (0 downto 0);
    signal excZ_x_uid15_fpMulTest_q : STD_LOGIC_VECTOR (0 downto 0);
    signal expXIsMax_uid16_fpMulTest_qi : STD_LOGIC_VECTOR (0 downto 0);
    signal expXIsMax_uid16_fpMulTest_q : STD_LOGIC_VECTOR (0 downto 0);
    signal fracXIsZero_uid17_fpMulTest_qi : STD_LOGIC_VECTOR (0 downto 0);
    signal fracXIsZero_uid17_fpMulTest_q : STD_LOGIC_VECTOR (0 downto 0);
    signal fracXIsNotZero_uid18_fpMulTest_q : STD_LOGIC_VECTOR (0 downto 0);
    signal excI_x_uid19_fpMulTest_q : STD_LOGIC_VECTOR (0 downto 0);
    signal excN_x_uid20_fpMulTest_q : STD_LOGIC_VECTOR (0 downto 0);
    signal invExpXIsMax_uid21_fpMulTest_q : STD_LOGIC_VECTOR (0 downto 0);
    signal InvExpXIsZero_uid22_fpMulTest_q : STD_LOGIC_VECTOR (0 downto 0);
    signal excR_x_uid23_fpMulTest_q : STD_LOGIC_VECTOR (0 downto 0);
    signal frac_y_uid28_fpMulTest_b : STD_LOGIC_VECTOR (22 downto 0);
    signal excZ_y_uid29_fpMulTest_qi : STD_LOGIC_VECTOR (0 downto 0);
    signal excZ_y_uid29_fpMulTest_q : STD_LOGIC_VECTOR (0 downto 0);
    signal expXIsMax_uid30_fpMulTest_qi : STD_LOGIC_VECTOR (0 downto 0);
    signal expXIsMax_uid30_fpMulTest_q : STD_LOGIC_VECTOR (0 downto 0);
    signal fracXIsZero_uid31_fpMulTest_qi : STD_LOGIC_VECTOR (0 downto 0);
    signal fracXIsZero_uid31_fpMulTest_q : STD_LOGIC_VECTOR (0 downto 0);
    signal fracXIsNotZero_uid32_fpMulTest_q : STD_LOGIC_VECTOR (0 downto 0);
    signal excI_y_uid33_fpMulTest_q : STD_LOGIC_VECTOR (0 downto 0);
    signal excN_y_uid34_fpMulTest_q : STD_LOGIC_VECTOR (0 downto 0);
    signal invExpXIsMax_uid35_fpMulTest_q : STD_LOGIC_VECTOR (0 downto 0);
    signal InvExpXIsZero_uid36_fpMulTest_q : STD_LOGIC_VECTOR (0 downto 0);
    signal excR_y_uid37_fpMulTest_q : STD_LOGIC_VECTOR (0 downto 0);
    signal ofracX_uid40_fpMulTest_q : STD_LOGIC_VECTOR (23 downto 0);
    signal ofracY_uid43_fpMulTest_q : STD_LOGIC_VECTOR (23 downto 0);
    signal expSum_uid44_fpMulTest_a : STD_LOGIC_VECTOR (8 downto 0);
    signal expSum_uid44_fpMulTest_b : STD_LOGIC_VECTOR (8 downto 0);
    signal expSum_uid44_fpMulTest_o : STD_LOGIC_VECTOR (8 downto 0);
    signal expSum_uid44_fpMulTest_q : STD_LOGIC_VECTOR (8 downto 0);
    signal biasInc_uid45_fpMulTest_q : STD_LOGIC_VECTOR (9 downto 0);
    signal expSumMBias_uid46_fpMulTest_a : STD_LOGIC_VECTOR (11 downto 0);
    signal expSumMBias_uid46_fpMulTest_b : STD_LOGIC_VECTOR (11 downto 0);
    signal expSumMBias_uid46_fpMulTest_o : STD_LOGIC_VECTOR (11 downto 0);
    signal expSumMBias_uid46_fpMulTest_q : STD_LOGIC_VECTOR (10 downto 0);
    signal signR_uid48_fpMulTest_qi : STD_LOGIC_VECTOR (0 downto 0);
    signal signR_uid48_fpMulTest_q : STD_LOGIC_VECTOR (0 downto 0);
    signal normalizeBit_uid49_fpMulTest_b : STD_LOGIC_VECTOR (0 downto 0);
    signal fracRPostNormHigh_uid51_fpMulTest_in : STD_LOGIC_VECTOR (46 downto 0);
    signal fracRPostNormHigh_uid51_fpMulTest_b : STD_LOGIC_VECTOR (23 downto 0);
    signal fracRPostNormLow_uid52_fpMulTest_in : STD_LOGIC_VECTOR (45 downto 0);
    signal fracRPostNormLow_uid52_fpMulTest_b : STD_LOGIC_VECTOR (23 downto 0);
    signal fracRPostNorm_uid53_fpMulTest_s : STD_LOGIC_VECTOR (0 downto 0);
    signal fracRPostNorm_uid53_fpMulTest_q : STD_LOGIC_VECTOR (23 downto 0);
    signal stickyRange_uid54_fpMulTest_in : STD_LOGIC_VECTOR (21 downto 0);
    signal stickyRange_uid54_fpMulTest_b : STD_LOGIC_VECTOR (21 downto 0);
    signal extraStickyBitOfProd_uid55_fpMulTest_in : STD_LOGIC_VECTOR (22 downto 0);
    signal extraStickyBitOfProd_uid55_fpMulTest_b : STD_LOGIC_VECTOR (0 downto 0);
    signal extraStickyBit_uid56_fpMulTest_s : STD_LOGIC_VECTOR (0 downto 0);
    signal extraStickyBit_uid56_fpMulTest_q : STD_LOGIC_VECTOR (0 downto 0);
    signal stickyExtendedRange_uid57_fpMulTest_q : STD_LOGIC_VECTOR (22 downto 0);
    signal stickyRangeComparator_uid59_fpMulTest_q : STD_LOGIC_VECTOR (0 downto 0);
    signal sticky_uid60_fpMulTest_q : STD_LOGIC_VECTOR (0 downto 0);
    signal fracRPostNorm1dto0_uid61_fpMulTest_in : STD_LOGIC_VECTOR (1 downto 0);
    signal fracRPostNorm1dto0_uid61_fpMulTest_b : STD_LOGIC_VECTOR (1 downto 0);
    signal lrs_uid62_fpMulTest_q : STD_LOGIC_VECTOR (2 downto 0);
    signal roundBitDetectionConstant_uid63_fpMulTest_q : STD_LOGIC_VECTOR (2 downto 0);
    signal roundBitDetectionPattern_uid64_fpMulTest_q : STD_LOGIC_VECTOR (0 downto 0);
    signal roundBit_uid65_fpMulTest_q : STD_LOGIC_VECTOR (0 downto 0);
    signal expFracPreRound_uid66_fpMulTest_q : STD_LOGIC_VECTOR (34 downto 0);
    signal roundBitAndNormalizationOp_uid68_fpMulTest_q : STD_LOGIC_VECTOR (25 downto 0);
    signal expFracRPostRounding_uid69_fpMulTest_a : STD_LOGIC_VECTOR (36 downto 0);
    signal expFracRPostRounding_uid69_fpMulTest_b : STD_LOGIC_VECTOR (36 downto 0);
    signal expFracRPostRounding_uid69_fpMulTest_o : STD_LOGIC_VECTOR (36 downto 0);
    signal expFracRPostRounding_uid69_fpMulTest_q : STD_LOGIC_VECTOR (35 downto 0);
    signal fracRPreExc_uid70_fpMulTest_in : STD_LOGIC_VECTOR (23 downto 0);
    signal fracRPreExc_uid70_fpMulTest_b : STD_LOGIC_VECTOR (22 downto 0);
    signal expRPreExcExt_uid71_fpMulTest_b : STD_LOGIC_VECTOR (11 downto 0);
    signal expRPreExc_uid72_fpMulTest_in : STD_LOGIC_VECTOR (7 downto 0);
    signal expRPreExc_uid72_fpMulTest_b : STD_LOGIC_VECTOR (7 downto 0);
    signal expUdf_uid73_fpMulTest_a : STD_LOGIC_VECTOR (13 downto 0);
    signal expUdf_uid73_fpMulTest_b : STD_LOGIC_VECTOR (13 downto 0);
    signal expUdf_uid73_fpMulTest_o : STD_LOGIC_VECTOR (13 downto 0);
    signal expUdf_uid73_fpMulTest_n : STD_LOGIC_VECTOR (0 downto 0);
    signal expOvf_uid75_fpMulTest_a : STD_LOGIC_VECTOR (13 downto 0);
    signal expOvf_uid75_fpMulTest_b : STD_LOGIC_VECTOR (13 downto 0);
    signal expOvf_uid75_fpMulTest_o : STD_LOGIC_VECTOR (13 downto 0);
    signal expOvf_uid75_fpMulTest_n : STD_LOGIC_VECTOR (0 downto 0);
    signal excXZAndExcYZ_uid76_fpMulTest_q : STD_LOGIC_VECTOR (0 downto 0);
    signal excXZAndExcYR_uid77_fpMulTest_q : STD_LOGIC_VECTOR (0 downto 0);
    signal excYZAndExcXR_uid78_fpMulTest_q : STD_LOGIC_VECTOR (0 downto 0);
    signal excZC3_uid79_fpMulTest_q : STD_LOGIC_VECTOR (0 downto 0);
    signal excRZero_uid80_fpMulTest_q : STD_LOGIC_VECTOR (0 downto 0);
    signal excXIAndExcYI_uid81_fpMulTest_q : STD_LOGIC_VECTOR (0 downto 0);
    signal excXRAndExcYI_uid82_fpMulTest_q : STD_LOGIC_VECTOR (0 downto 0);
    signal excYRAndExcXI_uid83_fpMulTest_q : STD_LOGIC_VECTOR (0 downto 0);
    signal ExcROvfAndInReg_uid84_fpMulTest_q : STD_LOGIC_VECTOR (0 downto 0);
    signal excRInf_uid85_fpMulTest_q : STD_LOGIC_VECTOR (0 downto 0);
    signal excYZAndExcXI_uid86_fpMulTest_q : STD_LOGIC_VECTOR (0 downto 0);
    signal excXZAndExcYI_uid87_fpMulTest_q : STD_LOGIC_VECTOR (0 downto 0);
    signal ZeroTimesInf_uid88_fpMulTest_q : STD_LOGIC_VECTOR (0 downto 0);
    signal excRNaN_uid89_fpMulTest_q : STD_LOGIC_VECTOR (0 downto 0);
    signal concExc_uid90_fpMulTest_q : STD_LOGIC_VECTOR (2 downto 0);
    signal excREnc_uid91_fpMulTest_q : STD_LOGIC_VECTOR (1 downto 0);
    signal oneFracRPostExc2_uid92_fpMulTest_q : STD_LOGIC_VECTOR (22 downto 0);
    signal fracRPostExc_uid95_fpMulTest_s : STD_LOGIC_VECTOR (1 downto 0);
    signal fracRPostExc_uid95_fpMulTest_q : STD_LOGIC_VECTOR (22 downto 0);
    signal expRPostExc_uid100_fpMulTest_s : STD_LOGIC_VECTOR (1 downto 0);
    signal expRPostExc_uid100_fpMulTest_q : STD_LOGIC_VECTOR (7 downto 0);
    signal invExcRNaN_uid101_fpMulTest_q : STD_LOGIC_VECTOR (0 downto 0);
    signal signRPostExc_uid102_fpMulTest_q : STD_LOGIC_VECTOR (0 downto 0);
    signal R_uid103_fpMulTest_q : STD_LOGIC_VECTOR (31 downto 0);
    signal prodXY_uid105_prod_uid47_fpMulTest_cma_reset : std_logic;
    type prodXY_uid105_prod_uid47_fpMulTest_cma_a0type is array(NATURAL range <>) of UNSIGNED(23 downto 0);
    signal prodXY_uid105_prod_uid47_fpMulTest_cma_a0 : prodXY_uid105_prod_uid47_fpMulTest_cma_a0type(0 to 0);
    attribute preserve : boolean;
    attribute preserve of prodXY_uid105_prod_uid47_fpMulTest_cma_a0 : signal is true;
    signal prodXY_uid105_prod_uid47_fpMulTest_cma_c0 : prodXY_uid105_prod_uid47_fpMulTest_cma_a0type(0 to 0);
    attribute preserve of prodXY_uid105_prod_uid47_fpMulTest_cma_c0 : signal is true;
    type prodXY_uid105_prod_uid47_fpMulTest_cma_ptype is array(NATURAL range <>) of UNSIGNED(47 downto 0);
    signal prodXY_uid105_prod_uid47_fpMulTest_cma_p : prodXY_uid105_prod_uid47_fpMulTest_cma_ptype(0 to 0);
    signal prodXY_uid105_prod_uid47_fpMulTest_cma_u : prodXY_uid105_prod_uid47_fpMulTest_cma_ptype(0 to 0);
    signal prodXY_uid105_prod_uid47_fpMulTest_cma_w : prodXY_uid105_prod_uid47_fpMulTest_cma_ptype(0 to 0);
    signal prodXY_uid105_prod_uid47_fpMulTest_cma_x : prodXY_uid105_prod_uid47_fpMulTest_cma_ptype(0 to 0);
    signal prodXY_uid105_prod_uid47_fpMulTest_cma_y : prodXY_uid105_prod_uid47_fpMulTest_cma_ptype(0 to 0);
    signal prodXY_uid105_prod_uid47_fpMulTest_cma_s : prodXY_uid105_prod_uid47_fpMulTest_cma_ptype(0 to 0);
    signal prodXY_uid105_prod_uid47_fpMulTest_cma_qq : STD_LOGIC_VECTOR (47 downto 0);
    signal prodXY_uid105_prod_uid47_fpMulTest_cma_q : STD_LOGIC_VECTOR (47 downto 0);
    signal prodXY_uid105_prod_uid47_fpMulTest_cma_ena0 : std_logic;
    signal prodXY_uid105_prod_uid47_fpMulTest_cma_ena1 : std_logic;
    signal redist0_signR_uid48_fpMulTest_q_2_q : STD_LOGIC_VECTOR (0 downto 0);
    signal redist1_expSum_uid44_fpMulTest_q_2_q : STD_LOGIC_VECTOR (8 downto 0);
    signal redist2_fracXIsZero_uid31_fpMulTest_q_2_q : STD_LOGIC_VECTOR (0 downto 0);
    signal redist3_expXIsMax_uid30_fpMulTest_q_2_q : STD_LOGIC_VECTOR (0 downto 0);
    signal redist4_excZ_y_uid29_fpMulTest_q_2_q : STD_LOGIC_VECTOR (0 downto 0);
    signal redist5_fracXIsZero_uid17_fpMulTest_q_2_q : STD_LOGIC_VECTOR (0 downto 0);
    signal redist6_expXIsMax_uid16_fpMulTest_q_2_q : STD_LOGIC_VECTOR (0 downto 0);
    signal redist7_excZ_x_uid15_fpMulTest_q_2_q : STD_LOGIC_VECTOR (0 downto 0);

begin


    -- frac_x_uid14_fpMulTest(BITSELECT,13)@0
    frac_x_uid14_fpMulTest_b <= a(22 downto 0);

    -- cstZeroWF_uid11_fpMulTest(CONSTANT,10)
    cstZeroWF_uid11_fpMulTest_q <= "00000000000000000000000";

    -- fracXIsZero_uid17_fpMulTest(LOGICAL,16)@0 + 1
    fracXIsZero_uid17_fpMulTest_qi <= "1" WHEN cstZeroWF_uid11_fpMulTest_q = frac_x_uid14_fpMulTest_b ELSE "0";
    fracXIsZero_uid17_fpMulTest_delay : dspba_delay
    GENERIC MAP ( width => 1, depth => 1, reset_kind => "ASYNC" )
    PORT MAP ( xin => fracXIsZero_uid17_fpMulTest_qi, xout => fracXIsZero_uid17_fpMulTest_q, clk => clk, aclr => areset );

    -- redist5_fracXIsZero_uid17_fpMulTest_q_2(DELAY,113)
    redist5_fracXIsZero_uid17_fpMulTest_q_2 : dspba_delay
    GENERIC MAP ( width => 1, depth => 1, reset_kind => "ASYNC" )
    PORT MAP ( xin => fracXIsZero_uid17_fpMulTest_q, xout => redist5_fracXIsZero_uid17_fpMulTest_q_2_q, clk => clk, aclr => areset );

    -- cstAllOWE_uid10_fpMulTest(CONSTANT,9)
    cstAllOWE_uid10_fpMulTest_q <= "11111111";

    -- expX_uid6_fpMulTest(BITSELECT,5)@0
    expX_uid6_fpMulTest_b <= a(30 downto 23);

    -- expXIsMax_uid16_fpMulTest(LOGICAL,15)@0 + 1
    expXIsMax_uid16_fpMulTest_qi <= "1" WHEN expX_uid6_fpMulTest_b = cstAllOWE_uid10_fpMulTest_q ELSE "0";
    expXIsMax_uid16_fpMulTest_delay : dspba_delay
    GENERIC MAP ( width => 1, depth => 1, reset_kind => "ASYNC" )
    PORT MAP ( xin => expXIsMax_uid16_fpMulTest_qi, xout => expXIsMax_uid16_fpMulTest_q, clk => clk, aclr => areset );

    -- redist6_expXIsMax_uid16_fpMulTest_q_2(DELAY,114)
    redist6_expXIsMax_uid16_fpMulTest_q_2 : dspba_delay
    GENERIC MAP ( width => 1, depth => 1, reset_kind => "ASYNC" )
    PORT MAP ( xin => expXIsMax_uid16_fpMulTest_q, xout => redist6_expXIsMax_uid16_fpMulTest_q_2_q, clk => clk, aclr => areset );

    -- excI_x_uid19_fpMulTest(LOGICAL,18)@2
    excI_x_uid19_fpMulTest_q <= redist6_expXIsMax_uid16_fpMulTest_q_2_q and redist5_fracXIsZero_uid17_fpMulTest_q_2_q;

    -- cstAllZWE_uid12_fpMulTest(CONSTANT,11)
    cstAllZWE_uid12_fpMulTest_q <= "00000000";

    -- expY_uid7_fpMulTest(BITSELECT,6)@0
    expY_uid7_fpMulTest_b <= b(30 downto 23);

    -- excZ_y_uid29_fpMulTest(LOGICAL,28)@0 + 1
    excZ_y_uid29_fpMulTest_qi <= "1" WHEN expY_uid7_fpMulTest_b = cstAllZWE_uid12_fpMulTest_q ELSE "0";
    excZ_y_uid29_fpMulTest_delay : dspba_delay
    GENERIC MAP ( width => 1, depth => 1, reset_kind => "ASYNC" )
    PORT MAP ( xin => excZ_y_uid29_fpMulTest_qi, xout => excZ_y_uid29_fpMulTest_q, clk => clk, aclr => areset );

    -- redist4_excZ_y_uid29_fpMulTest_q_2(DELAY,112)
    redist4_excZ_y_uid29_fpMulTest_q_2 : dspba_delay
    GENERIC MAP ( width => 1, depth => 1, reset_kind => "ASYNC" )
    PORT MAP ( xin => excZ_y_uid29_fpMulTest_q, xout => redist4_excZ_y_uid29_fpMulTest_q_2_q, clk => clk, aclr => areset );

    -- excYZAndExcXI_uid86_fpMulTest(LOGICAL,85)@2
    excYZAndExcXI_uid86_fpMulTest_q <= redist4_excZ_y_uid29_fpMulTest_q_2_q and excI_x_uid19_fpMulTest_q;

    -- frac_y_uid28_fpMulTest(BITSELECT,27)@0
    frac_y_uid28_fpMulTest_b <= b(22 downto 0);

    -- fracXIsZero_uid31_fpMulTest(LOGICAL,30)@0 + 1
    fracXIsZero_uid31_fpMulTest_qi <= "1" WHEN cstZeroWF_uid11_fpMulTest_q = frac_y_uid28_fpMulTest_b ELSE "0";
    fracXIsZero_uid31_fpMulTest_delay : dspba_delay
    GENERIC MAP ( width => 1, depth => 1, reset_kind => "ASYNC" )
    PORT MAP ( xin => fracXIsZero_uid31_fpMulTest_qi, xout => fracXIsZero_uid31_fpMulTest_q, clk => clk, aclr => areset );

    -- redist2_fracXIsZero_uid31_fpMulTest_q_2(DELAY,110)
    redist2_fracXIsZero_uid31_fpMulTest_q_2 : dspba_delay
    GENERIC MAP ( width => 1, depth => 1, reset_kind => "ASYNC" )
    PORT MAP ( xin => fracXIsZero_uid31_fpMulTest_q, xout => redist2_fracXIsZero_uid31_fpMulTest_q_2_q, clk => clk, aclr => areset );

    -- expXIsMax_uid30_fpMulTest(LOGICAL,29)@0 + 1
    expXIsMax_uid30_fpMulTest_qi <= "1" WHEN expY_uid7_fpMulTest_b = cstAllOWE_uid10_fpMulTest_q ELSE "0";
    expXIsMax_uid30_fpMulTest_delay : dspba_delay
    GENERIC MAP ( width => 1, depth => 1, reset_kind => "ASYNC" )
    PORT MAP ( xin => expXIsMax_uid30_fpMulTest_qi, xout => expXIsMax_uid30_fpMulTest_q, clk => clk, aclr => areset );

    -- redist3_expXIsMax_uid30_fpMulTest_q_2(DELAY,111)
    redist3_expXIsMax_uid30_fpMulTest_q_2 : dspba_delay
    GENERIC MAP ( width => 1, depth => 1, reset_kind => "ASYNC" )
    PORT MAP ( xin => expXIsMax_uid30_fpMulTest_q, xout => redist3_expXIsMax_uid30_fpMulTest_q_2_q, clk => clk, aclr => areset );

    -- excI_y_uid33_fpMulTest(LOGICAL,32)@2
    excI_y_uid33_fpMulTest_q <= redist3_expXIsMax_uid30_fpMulTest_q_2_q and redist2_fracXIsZero_uid31_fpMulTest_q_2_q;

    -- excZ_x_uid15_fpMulTest(LOGICAL,14)@0 + 1
    excZ_x_uid15_fpMulTest_qi <= "1" WHEN expX_uid6_fpMulTest_b = cstAllZWE_uid12_fpMulTest_q ELSE "0";
    excZ_x_uid15_fpMulTest_delay : dspba_delay
    GENERIC MAP ( width => 1, depth => 1, reset_kind => "ASYNC" )
    PORT MAP ( xin => excZ_x_uid15_fpMulTest_qi, xout => excZ_x_uid15_fpMulTest_q, clk => clk, aclr => areset );

    -- redist7_excZ_x_uid15_fpMulTest_q_2(DELAY,115)
    redist7_excZ_x_uid15_fpMulTest_q_2 : dspba_delay
    GENERIC MAP ( width => 1, depth => 1, reset_kind => "ASYNC" )
    PORT MAP ( xin => excZ_x_uid15_fpMulTest_q, xout => redist7_excZ_x_uid15_fpMulTest_q_2_q, clk => clk, aclr => areset );

    -- excXZAndExcYI_uid87_fpMulTest(LOGICAL,86)@2
    excXZAndExcYI_uid87_fpMulTest_q <= redist7_excZ_x_uid15_fpMulTest_q_2_q and excI_y_uid33_fpMulTest_q;

    -- ZeroTimesInf_uid88_fpMulTest(LOGICAL,87)@2
    ZeroTimesInf_uid88_fpMulTest_q <= excXZAndExcYI_uid87_fpMulTest_q or excYZAndExcXI_uid86_fpMulTest_q;

    -- fracXIsNotZero_uid32_fpMulTest(LOGICAL,31)@2
    fracXIsNotZero_uid32_fpMulTest_q <= not (redist2_fracXIsZero_uid31_fpMulTest_q_2_q);

    -- excN_y_uid34_fpMulTest(LOGICAL,33)@2
    excN_y_uid34_fpMulTest_q <= redist3_expXIsMax_uid30_fpMulTest_q_2_q and fracXIsNotZero_uid32_fpMulTest_q;

    -- fracXIsNotZero_uid18_fpMulTest(LOGICAL,17)@2
    fracXIsNotZero_uid18_fpMulTest_q <= not (redist5_fracXIsZero_uid17_fpMulTest_q_2_q);

    -- excN_x_uid20_fpMulTest(LOGICAL,19)@2
    excN_x_uid20_fpMulTest_q <= redist6_expXIsMax_uid16_fpMulTest_q_2_q and fracXIsNotZero_uid18_fpMulTest_q;

    -- excRNaN_uid89_fpMulTest(LOGICAL,88)@2
    excRNaN_uid89_fpMulTest_q <= excN_x_uid20_fpMulTest_q or excN_y_uid34_fpMulTest_q or ZeroTimesInf_uid88_fpMulTest_q;

    -- invExcRNaN_uid101_fpMulTest(LOGICAL,100)@2
    invExcRNaN_uid101_fpMulTest_q <= not (excRNaN_uid89_fpMulTest_q);

    -- signY_uid9_fpMulTest(BITSELECT,8)@0
    signY_uid9_fpMulTest_b <= STD_LOGIC_VECTOR(b(31 downto 31));
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
